341151719/sine-resistor-pcb-analysis/blender/output/c11_35_v8_pcb_isometric.png

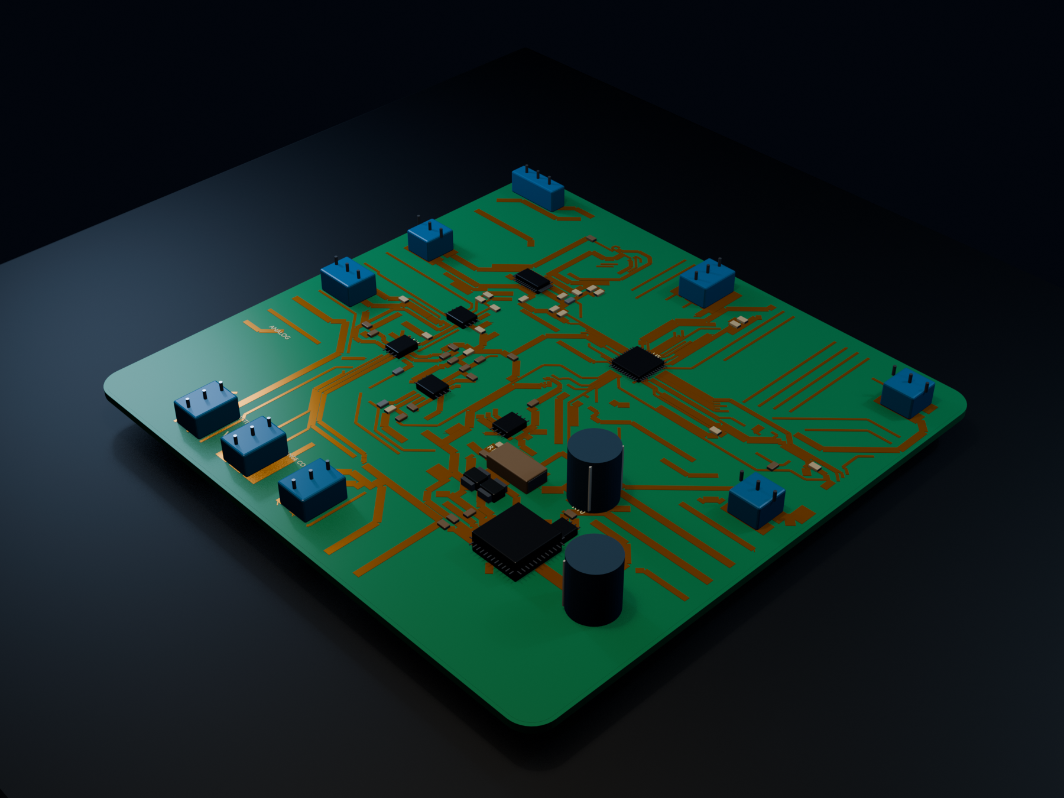
blender/output/c11_35_v8_pcb_isometric.png
