341151719/sine-resistor-pcb-analysis/实际遇到的问题/实板安全排障与根因判定计划.md

# 实板安全排障与根因判定计划

**项目：** Active Acoustic Impedance Controller C11_35  
**日期：** 2026-09-04  
**适用对象：** 已完成SMT的现有板卡  
**目标：** 在不依赖探测IC细脚、不让OPA548长时间进入异常功耗的前提下，用可重复A/B实验确定TP8约100–110 kHz振荡的真实来源，并将它与BOOT/SWD问题、控制算法问题分开。

---

## 1. 当前结论与证据边界

### 1.1 已确认的现象

- TP7/MUL_RAW基本稳定，异常首次明显出现在TP8/VCMD。
- TP8在OPA命令OFF时可出现约100–110 kHz、接近模拟电源轨的大幅周期波形。
- 改变J1的OPA548供电后，TP8波形会发生明显变化。
- OPA ON后J1电源约70 mA进入CC；watchdog关闭OPA后恢复。
- U4 pin6金属脚至U4B_N外部网络约20 mΩ；未上电新板也相同，因此外部pin6兆欧级虚焊模型已经被否定。
- 文档报告OPA OFF时TP9−TP14约0.55–0.65 V；这个值低于OPA548明确Disable阈值0.8 V，但缺少同一振荡时刻的原始波形。

### 1.2 已独立复跑的模型结果

- PCB-aware reduced模型：交越频率1.135410 MHz，相位裕量63.5245°。
- full segmented模型：交越频率1.136326 MHz，相位裕量63.7882°。
- reduced transient尾段TP8仅约1.88×10⁻⁷ Vpp；Gear与Trap算法结论一致。
- 因此，健康OPA1656、1 kΩ/39 kΩ反馈和模型已覆盖的一阶走线/去耦寄生不会自行产生实板的105 kHz振荡。
- 人为加入“U4内部动态异常”能够拟合105 kHz，但它只是等效故障模型，不能代替换件或隔离实验。

### 1.3 当前需要区分的三个故障族

| 故障族 | 能解释什么 | 尚缺的决定性证据 |
|---|---|---|
| U4B本地环路/器件异常 | TP7干净、TP8发振；健康模型与实物不符 | R5断开后仍振；更换U4后消失并可重复 |
| OPA548关断支路经R5参与 | 改变J1会改变TP8；OPA ON后高耗流 | 断开R5后消失；恢复R5后复现 |
| ANA电源或AGND高频异常 | 可从供电/参考端调制U4B | TP11/TP12存在与TP8同步且足够大的纹波；改善供电后可逆消失 |

不得因为“加补偿电容后不振”就直接判定缺少补偿是根因。补偿可能只是在压制任何来源造成的环路异常。

---

## 2. 测试点与可接触位置

### 2.1 连接器引脚——优先用于电源和地

以下映射由当前`project.kicad_pcb`原文件确认。

| 连接器 | Pin 1 | Pin 2 | Pin 3 | 用途 |
|---|---|---|---|---|
| J1 | PWR_P | PGND | PWR_N | OPA548对称电源 |
| J2 | ANA_P_EXT | AGND | ANA_N_EXT | 精密模拟对称电源 |
| J3 | V5_IN | DGND | — | MCU/数字5 V输入 |
| J4 | SPK | PGND | — | 扬声器输出；根因定位期间必须开路 |
| J5 | VK_MCU | VK | VK_EXT | VK来源选择；使用MCU控制时外接1–2桥接 |
| J7 | V3V3 | SWDIO | SWCLK | SWD，另有Pin4=NRST、Pin5=DGND |

接线前必须根据PCB丝印和断电导通再确认Pin 1方向，不能仅凭“左/右”描述接线。

J7没有列入SMT装配，实际焊盘也不适合通电时手压杜邦线。烧录前应一次性焊好匹配排针/短线，或使用带定位的pogo夹具；不得把五根散线临时按在焊盘上完成重复性测试。

### 2.2 现有测试点

| 测试点 | 网络 | PCB坐标(mm) | 用途 | 推荐接法 |
|---|---|---:|---|---|
| TP7 | MUL_RAW | 93.013, 113.362 | U4B输入 | 断电预焊细线；只测量，不外部驱动 |
| TP8 | VCMD | 163.244, 54.307 | U4B输出/OPA548命令 | 断电预焊细同轴中心线 |
| TP9 | OPA_ES | 203.376, 93.677 | OPA548 E/S | DMM测量；需要看交流时预焊线 |
| TP11 | ANA_P | 97.331, 112.346 | U4实际正模拟轨 | 预焊线后示波器测量 |
| TP12 | ANA_N | 93.140, 83.517 | U4实际负模拟轨 | 仅用差分或两通道数学运算测量 |
| TP13 | PWR_P | 203.376, 99.138 | OPA548正轨 | DMM/差分测量 |
| TP14 | PWR_N | 143.305, 86.057 | OPA548负轨 | DMM；绝不能接普通台式示波器地夹 |
| TP16 | AGND | 93.140, 95.455 | 模拟测量参考 | TP7/TP8/TP11/TP12的唯一高频参考 |
| TP17 | PGND | 156.005, 54.307 | 功率测量参考 | TP1/TP2/TP9/TP13/TP14参考 |
| TP1 | SPK | 203.376, 118.696 | 电流取样后扬声器端 | 后期功率级测试使用 |
| TP2 | DRV | 203.376, 88.216 | OPA548功率输出 | 仅在TP8已稳定后使用 |
| TP15 | V3V3 | 187.755, 123.776 | MCU 3.3 V | 数字电源确认 |

**机械限制：** PCB原文件中这些测试点大多实际为约1×1 mm顶层SMD裸焊盘，不是通孔测试柱，而且参考标号在PCB中被隐藏，成品丝印上可能找不到TP编号。上表坐标以PCB左上外形约`(89.965, 51.640)`为参考，可在KiCad中定位。禁止通电时用手持表笔长时间压住。推荐在断电状态焊接30 AWG软线或短细同轴，长度尽量小于50 mm，并用胶带/热熔胶在离焊点5–10 mm处做应力释放。焊完后用放大镜检查锡桥。

### 2.3 没有独立大测试点的U4B_N

U4B_N没有独立编号测试点。若必须同步测反馈比例，不探U4 pin6，优先使用DNP补偿位C14的焊盘；C14 pad 1为VCMD，pad 2为U4B_N。C37/C38/C39/C40/C41也跨接相同两网，可作为备选：

1. 全部电源关闭并确认TP11、TP12、TP13、TP14相对各自地小于0.2 V。
2. 用蜂鸣档寻找与TP8导通的一侧，该侧是VCMD。
3. 另一侧是U4B_N；在这一侧预焊30 AWG短线。即使使用C14，也必须用导通关系复核，不凭左右方向猜测。
4. 上电前再次确认该线未与VCMD或相邻焊盘短路。

不要根据电容在板上的“左/右”猜焊盘编号；以断电导通测试为准。

---

## 3. 仪器与通用安全限制

### 3.1 最低设备

- 三组受控电源：5 V数字电源、±10 V模拟电源、OPA548对称电源。对称电源优先使用跟踪双路或明确隔离的两个通道。
- 两通道或四通道示波器，10×探头；优先使用短地弹簧、细同轴或差分探头。
- 浮地电池式DMM。
- 细线、放大镜、ESD工作台；进行R5/U4操作时需要合格返修工具。

### 3.2 台式示波器接地规则

- 普通台式示波器所有BNC外壳通常与保护地相连，各通道地夹彼此相通。
- 模拟信号TP7/TP8统一以TP16/AGND为参考。
- 功率输出TP1/TP2统一以TP17/PGND为参考。
- 禁止把示波器地夹接到TP12/ANA_N、TP14/PWR_N、TP8或任何信号点。
- 测`TP9−TP14`时优先用浮地DMM；若要观察高频分量，使用差分探头，或两通道分别对TP17测量后用`CH1−CH2`。两个通道的地都只能接TP17。
- 已发生过地夹误接TP2/TP8的事故。每次上电前由第二人或按检查表复核全部地线。

### 3.3 电源连接原则

- 若使用两个电源通道串联生成±电源，先断电用欧姆档确认通道输出之间允许浮地；不允许把两个共地通道强行串联。
- J1中心点只接PGND，J2中心点只接AGND，J3负端只接DGND。板上已有R3连接地域，不再用额外粗线任意短接不同地。
- 先设置电压和限流，再连接板卡；所有改焊均在电源线物理拔除后进行。
- 初次上电不要接扬声器、电子负载或函数发生器。

### 3.4 保守限流与停止条件

下表是排障用保守值，不是产品额定能力签核。

| 电源 | 初始条件 | 初始限流 | 可放宽上限 | 立即停止条件 |
|---|---:|---:|---:|---|
| J3 | 5.0 V | 50 mA | 确认无短路后100 mA；已知固件确需时最高200 mA | 3.3 V异常、器件发热、持续CC |
| J2 | ±8.0 V跟踪预检，随后±10.0 V | 每轨30 mA | 已建立健康基线后每轨50 mA | 任一轨CC超过0.2 s、两轨相差>15 mA、TP8撞轨 |
| J1，OPA OFF | 从±4.0 V开始 | 每轨20 mA | 扫描时每轨30 mA | 任一轨CC、比基线增加>10 mA、器件升温 |
| J1，OPA ON | 仅后期，±4.0 V | 每轨25 mA | 首次脉冲正常后40 mA；本轮不建议超过60 mA | 高频输出>1 Vpp、CC、异常声响或温升 |

若电源只能显示总电流而不能分别显示正负轨，不能执行“轨电流不平衡”判据，应增加串联电流表或使用独立可读通道。

所有阶段通用停止条件：

- TP8出现超过1 Vpp的持续高频时只允许单次捕获，并在0.2 s内关断；明显贴轨时立即关断；
- 任一电源进入CC超过0.2 s；
- 电流比同配置基线上升10 mA以上且原因不明；
- U1/U4/R12/C4达到50 °C停止观察，60 °C为硬停止；没有测温仪时不得用手触摸判断，采用短脉冲和电流门限；
- 负电源极性错误、示波器地线位置不能确认、探线松动。

正常停机时先关闭J2，避免J2仍经R5驱动已经失去供电的OPA548输入；随后关闭J1，最后关闭J3。紧急情况下用总输出键同时关闭J1/J2；若J1已经CC或功率级异常，则优先立即关闭J1并紧接着关闭J2。等待所有正负轨相对各自地低于0.2 V后才能触碰或焊接。需要加速放电时使用10 kΩ、至少1 W绝缘电阻逐轨放电，禁止用螺丝刀短接。

---

## 4. 统一记录格式

每次实验只改变一个变量。每块板分配固定Board ID，至少记录：

| 字段 | 内容 |
|---|---|
| Board ID/批次 | 板号、生产批次、U4/U1顶标照片编号 |
| 硬件状态 | R5装/拆、R10是否并联、Cfb值、J5连接 |
| 电源 | J1/J2/J3设定、电流限制、实际正负轨电流 |
| 控制状态 | 固件版本、OPTR值、OPA命令OFF/ON、DAC设置 |
| 波形 | TP7、TP8 Vpp/频率/DC；必要时U4B_N、ANA轨纹波 |
| 结果 | 稳定/振荡/CC/停止条件 |
| 原始数据 | 示波器截图与CSV文件名 |

示波器应固定使用同一探头倍率、带宽限制和采样率。观察105 kHz时建议：

- 10×探头；
- 采样率至少10 MS/s；
- 时间基准约2–5 µs/div观察单周期，同时保存100–500 µs窗口观察包络；
- 先不开20 MHz带宽限制保存一次原始波形，再开20 MHz限制比较；
- 每次同时保存TP7和TP8，不能用不同时刻的截图计算比例。

---

## 5. 分阶段测试流程

## 阶段A：断电外观与电阻基线

**目的：** 在上电前排除明显错件、焊桥及测试接线风险。

1. 拔除J1/J2/J3/J4全部线缆；等待各测试轨低于0.2 V。
2. 确认J4开路，C14、C37–C41及其他标记DNP的补偿位没有意外装件或锡桥。
3. 拍摄U4、U1顶标和方向照片，记录Board ID。不要只检查振荡板，至少包含一块未修改板。
4. 测U4 pin6外部网络连续性时继续采用已经建立的方法，但不要把20 mΩ解释成芯片内部一定健康。
5. 在电路板内测量R15、R16仅作为筛查：目标约1 kΩ和39 kΩ。若偏差超过标称5%，先考虑并联通路影响；只有抬起一端后的测量才能用于确认错值。
6. 检查J1/J2各轨对中心地是否存在硬短路。电容充电造成的读数变化属于正常可能性，不规定一个绝对电阻门限；使用同批未改板横向比较。

**判定：**

- 多块板同一位置、同一顶标、同一症状：系统性设计/物料问题权重上升。
- 只有个别板异常且外观/阻值不同：装配或器件个体问题权重上升。

## 阶段B：数字与烧录问题独立验证

**目的：** 不给模拟/功率域供电，判断“普通上机和烧录不稳定”是否与模拟振荡是两个问题。

连接：

- J1、J2、J4全部断开。
- J3接5.0 V，初始限流50 mA；确认无短路但正常启动确实需要时再升到100 mA。
- SWD只接J7：Pin1 V3V3检测、Pin2 SWDIO、Pin3 SWCLK、Pin4 NRST、Pin5 DGND。
- 调试器不得同时向目标板供电；只检测V3V3。

流程：

1. 上电后从TP15确认V3V3稳定；若50 mA限流导致正常启动失败，先断电检查无短路，再提高到100 mA。
2. SWD先固定1 MHz并使用connect-under-reset。
3. 读取并记录OPTR；已验证的Flash启动值为`0xFBEFF8AA`，历史异常值为`0xFFEFF8AA`。复位后PC应进入`0x0800....`主Flash范围，而不是`0x1FFF....`系统存储器。
4. 连续执行10次“断电5 s→上电→连接→擦除→写入→verify→复位运行”。
5. 每次记录成功/失败、错误原文、V3V3和NRST状态。
6. 只有1 MHz十次全通过后，才可另做4 MHz对照；4 MHz失败而1 MHz稳定只证明接口裕量问题，不证明MCU损坏。

**判定：**

- J1/J2完全断开仍烧录失败：模拟振荡不是烧录失败的必要条件，继续沿BOOT、SWD接触、NRST及3.3 V调查。
- 数字单独10/10通过，而接入模拟电源后失败：再建立模拟电源接入的单变量A/B。

## 阶段C：原板零输入振荡基线

**目的：** 在OPA始终OFF、J4开路条件下重现实板异常，建立后续A/B基线。

准备：

- 在断电状态预焊TP7、TP8、TP16短线；TP7/TP8只接10×示波器输入。
- J5必须保持“原始故障复现时”的准确状态并记录。若原测试为OPEN，本轮先保持OPEN；只有另立单变量实验时才桥接1–2或2–3，不能在建立基线时顺便改变J5。
- 固件将OPA命令保持OFF，DAC/算法保持静态零测试状态。
- 不接外部函数发生器；TP7是AD633输出，直接驱动会造成输出争用。

上电顺序：

1. J3 5 V上电，确认固件运行且OPA命令OFF。
2. J1设±4.0 V、每轨20 mA，同时使能正负轨。先给处于Disable命令的OPA548供电，再启动J2，是为了避免TP8经R5驱动一个完全无电的OPA548输入。
3. J2先设±8.0 V、每轨30 mA完成极性和电流预检；AD633保证工作范围从±8 V开始，低于此值的波形不能用于根因判定。预检正常后升至原故障条件±10.0 V，每轨35 mA。
4. 立即记录三组电流和TP7/TP8；若触发停止条件，优先总键同时关闭J1/J2；不能同时关闭时按3.4节的紧急停机规则执行，最后关闭J3。
5. 在±4.0、±4.5、±5.0、±5.5、±6.0、±6.5 V逐级改变J1，J2保持±10 V不变。波形稳定且小于1 Vpp时每档最多停留3 s；一旦触发到>1 Vpp持续高频，只做预设单次捕获，并在0.2 s内关闭J1/J2，不继续扫更高电压。优先使用电源总输出键同时关闭；不能同时关闭时先关J2，若J1已CC则先关J1并立即关J2。
6. 每档保存TP7/TP8同步波形、TP8频率/Vpp/DC和J1正负轨电流。若在某档进入CC，不继续提高。

**这个阶段不允许OPA ON。**

**判定：**

- TP7稳定而TP8出现105 kHz：确认问题仍定位在TP7之后。
- J1电压可重复改变TP8波形：证明J1域参与或调制，但不能单凭此点认定OPA548是振荡源。
- 不同板的转变电压高度一致：系统性设计/器件特性权重上升；离散很大则装配、器件批次或接触问题权重上升。

## 阶段D：使用现成TP确认OPA548实际关断状态

**目的：** 不探U1细脚，确认振荡时E/S相对PWR_N是否仍处于Disable区。

连接：

- 浮地DMM直接接TP9与TP14，红表笔TP9、黑表笔TP14。
- 示波器仍只观察TP7/TP8；不把示波器地接TP14。
- DMM只能提供慢速/直流筛查；它不能证明E/S在105 kHz每个周期都未跨越门限。

流程：

1. 重复阶段C中最容易产生规则105 kHz的一档J1电压。
2. 用DMM读取`V(TP9)−V(TP14)`的慢速值；若要记录最小/最大和门限跨越，必须用有足够带宽的差分波形。
3. 在J1各电压档重复；不要只测一个静态电压。
4. 若需要观察E/S交流分量，使用差分探头；没有差分探头则两通道均对TP17测量后相减。

**波形判据：**

- 全过程≤0.8 V：数据手册意义上明确Disable；“R10导致实际一直Enable”不成立。
- 全过程≥2.4 V：实际Enable，过去的“OPA OFF”定义错误。
- 进入0.8–2.4 V或随105 kHz跨越门限：E/S处于未保证区，优先调查R10/U7动态。
- 即使≤0.8 V，也只能证明关断逻辑电平正确，不能证明关断器件在105 kHz下完全没有输入/保护耦合。

仅有DMM时，≤0.8 V或≥2.4 V只能作为平均/慢速状态证据，不得写成“全过程”判定。

## 阶段E：R5隔离——最高信息量实验

**目的：** 直接判断OPA548输入支路是不是TP8振荡成立的必要条件。

返修：

1. 全部电源线拔除，确认TP11/TP12/TP13/TP14相对地均低于0.2 V。
2. 完整拆下R5=100 Ω，不切PCB走线；保存原件或准备同规格新件。
3. 放大检查焊盘。用蜂鸣档确认其中一侧与TP8导通，该侧为VCMD；两焊盘之间应开路。
4. 不在通电状态触碰R5焊盘，也不需要探测OPA_IN_P或U1细脚。

测试E1——J1不供电：

1. J4开路、OPA命令OFF。
2. 先J3上电，再给J2±10 V、每轨35 mA上电；J1保持物理断开。此处R5已经拆除，因此不会经TP8反向驱动无电的OPA548输入。
3. 观察TP7/TP8 10 s。

测试E2——J1供电但OPA OFF：

1. 保持R5拆除。
2. J1从±4.0 V开始，按阶段C的档位扫到异常发生前的最高安全档。
3. 同步记录TP7/TP8和电流。

恢复验证：

1. 全部断电并放电后重新焊接100 Ω R5。
2. 重复阶段C完全相同的电压档和固件状态。

**决定性判因：**

| R5拆除 | R5恢复 | 结论 |
|---|---|---|
| 仍以相同频率/幅度振荡 | 仍振荡 | OPA548输入支路不是必要条件；转向U4本地/ANA供电 |
| 稳定 | 恢复后重新振荡 | OPA548/R5支路是必要条件，形成强因果证据 |
| 稳定 | 恢复后仍稳定 | 不能判因；返修加热或接触变化可能影响了U4/R5周围状态 |
| 频率/幅度改变但未消失 | 恢复后可逆 | OPA548支路是参与者，但可能不是唯一振荡源 |

至少在两块板重复，不能用单板单次结果结束调查。

## 阶段F：若R5拆除后仍振荡——调查U4本地环路

### F1. 同步反馈比例

1. 按2.3节优先在DNP C14的U4B_N侧预焊短线，不探U4 pin6；C37–C41仅作为备选。
2. CH1接TP8，CH2接预焊的U4B_N线；两个通道地都接TP16。
3. 同步读取Vpp和相位，计算`U4B_N Vpp / TP8 Vpp`。

判据：在Cfb确认DNP、正弦基波、共同AGND参考且输入电流可忽略时，健康1 kΩ/39 kΩ反馈的基波比例应接近1/40=0.025。对方波或装有Cfb时应比较105 kHz基波复数幅值和相位，不直接比总Vpp。若在上述条件下稳定得到0.045–0.055：

- 先断电确认R15/R16实物值；
- 检查AGND高频运动；
- 在排除前两项后，才把U4输入异常提高优先级。

### F2. ANA电源轨同步测量

- CH1：TP8对TP16。
- CH2：TP11对TP16，记录ANA_P纹波。
- 测ANA_N时使用差分探头，或两个通道分别测TP12和TP16后相减；禁止地夹接TP12。
- 分别保存100–110 kHz处的幅度与相位。

判据：

- 轨纹波仅几十mV，而TP8接近十几Vpp：不支持“外部电源纹波直接驱动TP8”。已有模型估计需要数V峰值的轨纹波才能直接产生16 Vpp TP8。
- 轨纹波达到0.5 Vpp以上：供电完整性成为高优先级。
- 达到1 Vpp或电源进入CC：立即停机，不继续扫电压。

### F3. Cfb诊断，不作为最终修复结论

1. 全部断电并放电。
2. 优先在C39=22 pF位置安装22 pF C0G/NP0；保持R5拆除状态，重复阶段E1/E2。
3. 记录是否消振、频率、TP8噪声和低频增益。
4. 移除22 pF确认是否恢复；必要时再在C40位置试47 pF。
5. 本阶段不直接安装220 pF作为最终值。

若22/47 pF使振荡消失，只能证明降低高频环路增益有效。只有结合R5隔离、供电测量和U4换件结果才能判断根因。

### F4. U4可逆换件

这是返修级操作，不要求操作者探测SOIC细脚。

1. 选择一块症状可稳定复现的板，保持Cfb=DNP并记录完整基线。
2. 由具备SOIC返修能力的人员更换为来源可追溯的OPA1656IDR。
3. 清洗并检查焊点，不顺便改动R5/R15/R16或去耦。
4. 重复阶段C和阶段E1条件。
5. 如果新U4不振，条件允许时把旧U4装到测试载板或原板复测；否则“换件后好了”仍混入了重焊效应。

强确认条件：同一板、同一条件下旧U4振荡，新U4稳定，而且第二块板重复相同结果。

## 阶段G：若R5拆除后稳定——调查OPA548关断支路

先恢复R5=100 Ω并确认异常可复现，再做以下单变量测试。

### G1. R10加强下拉A/B

1. 断电并放电。
2. 将10 kΩ电阻临时接在TP9与TP14之间，等效与R10=100 kΩ并联。优先焊接带绝缘的短引线，不在通电时夹持。
3. 保持OPA命令OFF，禁止执行OPA ON。
4. 重复阶段C的J1扫描，记录TP9−TP14、TP7/TP8和J1电流。
5. 断电移除10 kΩ后恢复原条件，确认现象是否返回。

判定：

- 并10 kΩ稳定、移除后恢复振荡：E/S偏置或动态是必要因素。
- TP9−TP14始终约0.6 V且并10 kΩ无影响：R10不是当前主因。
- 只改变波形但不消失：E/S参与，但仍有其他发生源。

### G2. J1参与性

保持R5装回、OPA OFF，比较：

- J1±4.0 V；
- J1±5.0 V；
- J1±6.0 V；

不建议把“J1完全断电”与“J1供电关断”直接等价，因为无电的OPA548输入保护结构可能以不同方式加载TP8。只有R5物理拆除才是真正的支路隔离。

### G3. OPA548换件

只有R5隔离已经证明该支路必要、而R10 A/B不能解释时，才安排OPA548返修换件。换件前后保持R5、J1、J2和固件完全一致，并在至少两块板验证。

---

## 6. 功率级重新启用的安全门槛

在满足以下全部条件以前，不允许OPA ON：

- 根因定位阶段J4保持开路；首次OPA ON前改接1 kΩ假负载；
- TP8在10 s观察内没有持续100–110 kHz分量；
- TP8高频Vpp小于50 mV；
- TP7/TP8直流工作点没有贴轨；
- J1/J2没有CC或明显正负轨不平衡；
- R5、Cfb及所有临时线状态已经记录。

### 6.1 首次OPA ON验证

1. 在J4接入1 kΩ、至少2 W的纯电阻假负载；不要直接接扬声器。J1只设±4.0 V，每轨限流25 mA；J2保持±10 V。
2. 示波器CH1接TP8/TP16，CH2接TP2/TP17。
3. 固件输出静态零命令，OPA ON脉冲先限制为20–50 ms；不要依赖5 s watchdog保护。
4. 任一条件出现立即OFF：TP2高频>1 Vpp、TP8高频>50 mVpp、J1触及25 mA限流或温度达到50 °C。
5. 20–50 ms连续三次正常后，可把限流提高到40 mA，再延长至100 ms、500 ms、1 s；每一级都保存波形和电流。

### 6.2 小信号功能测试

- 不从外部函数发生器直接驱动TP7/TP8。
- 使用固件/DAC产生低频命令，并以实测TP7作为真实输入量。
- 从100 Hz开始，令TP7≤10 mVpp；按非反相增益约40估算，TP8约0.4 Vpp。
- 依次测试10、30、100、300、1000 Hz；每次先确认无100–110 kHz寄生，再提高TP7至25 mVpp。
- 在1 kΩ初始假负载下输出稳定前，不提高到会让TP8超过2 Vpp的输入。

### 6.3 负载测试

实际扬声器最后连接。推荐顺序：

1. OPA OFF、J4开路的前级稳定性；
2. OPA ON、1 kΩ纯电阻初始假负载；
3. 合适功率等级的20 Ω纯电阻假负载；
4. 7.2 Ω纯电阻假负载；
5. 实际扬声器。

每换一种负载都从J1±4 V、小信号和低限流重新开始。负载电阻额定功率必须按测试信号计算并留至少2倍裕量；不能使用普通小功率电阻代替。

---

## 7. 根因判定矩阵

| 实验结果 | 支持的根因 | 被削弱的根因 | 下一步 |
|---|---|---|---|
| 数字域单独仍烧录失败 | BOOT/SWD/NRST/3.3 V独立问题 | 模拟振荡是唯一总根因 | 完成10次1 MHz/4 MHz受控A/B |
| R5拆除后105 kHz完全不变 | U4本地、反馈或ANA供电 | OPA548输入支路是必要条件 | F1/F2/U4换件 |
| R5拆除后稳定，恢复后复现 | OPA548/R5支路是维持该现象的必要条件 | 只由与R5无关的机制维持 | G1，再区分输入钳位、E/S、供电耦合和器件故障 |
| R10并10 kΩ后可逆消振 | E/S偏置/动态是维持现象的必要条件之一 | 与E/S状态无关的机制 | 验证ON/OFF裕量、温度/批次和R5两端电流 |
| U4换件后可逆消振 | U4错料/损伤/批次动态异常 | 单纯PCB寄生 | 查顶标、来源、批次和受损机制 |
| 22/47 pF消振但R5/U4 A/B无结论 | 仅证明补偿能压症状 | 无法确定发生源 | 不冻结量产值，继续隔离实验 |
| ANA轨存在同频>0.5 Vpp纹波 | 供电/地耦合参与 | 纯净供电假设 | 查FB1/FB2、去耦回路和电源源阻抗 |
| Cfb=DNP且基波TP8/U4B_N稳定接近1/20 | 实物反馈比、地参考或U4输入异常 | 健康1k/39k假设 | 断电隔离测R15/R16并查AGND；保留同步波形 |
| 多块未修改板完全相同 | 系统性设计/物料/布局 | 随机单板损伤 | 选一个变量跨板A/B |
| 只有受过误接地的板异常 | 个体器件损伤 | 系统性必现问题 | 与全新板同条件比较并换U4 |

根因达到“确认”至少需要：

1. 单变量改变使问题消失；
2. 恢复原变量使问题重新出现，或在第二块板重复；
3. 观察到的后果与电路机制相符；
4. 没有触发供电CC、测量接地或返修加热等混杂变量。

只满足其中一项时最多标记为“相关”或“候选”，不得写成最终根因。

---

## 8. 推荐实际执行批次

### 第一批：无需改焊器件

1. 阶段A外观和阻值筛查。
2. 阶段B数字域10次烧录基线。
3. 预焊TP7/TP8/TP16测量线。
4. 阶段C受控J1扫描。
5. 使用TP9/TP14完成阶段D。

### 第二批：只改R5，信息增益最高

1. 选择症状最稳定的一块板拆R5。
2. 完成E1、E2。
3. 恢复R5重复原条件。
4. 在第二块板重复。

### 第三批：根据R5结果二选一

- R5拆除后仍振：做F1、F2，然后U4换件；Cfb仅作为诊断。
- R5拆除后稳定：做R10并10 kΩ可逆A/B，再决定是否换OPA548。

### 第四批：功率级恢复

只有TP8稳定后才执行阶段6，先在1 kΩ假负载下做毫秒级OPA ON，再做小信号，然后才换20 Ω/7.2 Ω假负载，最后接扬声器。

---

## 9. 禁止事项

- 禁止通电时用普通表笔直接探U4/U1细脚。
- 禁止示波器地夹接负电源轨、TP8、TP2或任意非地信号。
- 禁止在TP7、TP8直接接函数发生器。
- 禁止在100–110 kHz仍存在时执行长达5 s的OPA ON。
- 禁止一边改变J1电压、一边改变限流、固件、Cfb或负载后再把结果当成单变量实验。
- 禁止因为22/47/220 pF使波形变小就宣布“根因是缺电容”。
- 禁止把ngspice的`timestep too small`当成实板振荡证据。
- 禁止使用已经发生示波器误接地的板作为唯一代表板。

---

## 10. 验证基础与局限

### 已执行

- KiCad原理图与PCB网络核对。
- 生产BOM、CPL和Gerber一致性核对。
- PCB-aware reduced/full AC复跑。
- reduced transient使用Gear/Trap两种方法复跑。
- 实际问题对话记录按“实测/仿真/推测/计划”重新分类。

### 本计划的限制

- 当前目录没有可复核的原始示波器CSV、完整截图、板号和逐板重复次数。
- OPA548厂商宏模型的OFF transient不可靠，不能用于关断状态定量签核。
- R15/R16约1/40矛盾缺少同步双通道原始测量。
- R5隔离、R10并联、U4换件和ANA轨同步波形尚未在实板执行。
- 本计划中的限流是排障保护设置，不是产品最大额定电流或最终性能指标。

因此，文档当前给出的是可执行的安全判因流程，而不是预先指定某一个元件为最终根因。

---

## 11. 主要证据来源

- **PCB原文件确认：** `KICAD部分/给厂商的板子加工数据/正弦电阻V7_KiCad10.0.4_校正转换版/project.kicad_pcb`。用于确认J1/J2/J3/J4/J5/J7引脚、TP网络、焊盘尺寸和R5/R10/R15/R16网络。
- **生产BOM确认：** `KICAD部分/给厂商的板子加工数据/正弦电阻V7_KiCad10.0.4_校正转换版/audit/bom_smt_73.csv`。用于确认U1、U4及关键电阻的实际下单值。
- **实板现象来源：** `实际遇到的问题/分支-·-分支-·-SPICE可行性测试结果.md`。其中同时包含用户实测、历史助手推测和仿真结果；本计划没有把三者混为一类。
- **独立复跑网表：** `实际遇到的问题/PCB_AWARE_U4B_OFF_reduced.cir`与`PCB_AWARE_full_extracted_loop.cir`。
- **OPA548数据手册依据：** 推荐双电源范围±4 V至±30 V；Disable为`E/S≤V−+0.8 V`，Enable为`E/S≥V−+2.4 V`；关断静态电流典型约±6 mA，正常静态电流典型约±17 mA；关断器件遇到高于20 kHz信号时泄漏可能增加。
- **AD633数据手册依据：** 工作电源范围±8 V至±18 V。因此低于±8 V只适合短路/极性预检查，不能用于判断正常模拟行为。

证据等级用法：原文件网络和独立仿真数值可以复核；数据手册阈值用于设置边界；“U4内部异常”“OPA548关断耦合”等在完成可逆实板A/B以前仍属于候选解释。
