341151719/sine-resistor-pcb-analysis/实际遇到的问题/分支-·-分支-·-SPICE可行性测试结果.md

> From: https://chatgpt.com/g/g-p-6a4f06948d488191a8b99392c0b437f0/c/6a8c0352-682c-83ec-a9a8-80c052f3bece

> 历史对话归档：包含后续被否定或限定的判断，不宜直接作为当前结论。
> 2026-09-15 复核见 [证据重新审查](../实验还原部分/主动审计/EVIDENCE_REASSESSMENT_20260915.md)：
> 峰值电流不能证明持续 CC；1/40 反馈比例只适用于规定的无补偿/近似高输入阻抗条件；
> 命令 OFF 与硬件 OFF、J1 参与性与振荡起源必须分开确认。

# you asked

message time: 2026-07-09 10:34:38

测试SPICE的可行性。

---

# chatgpt response

我会直接在沙盒里解压运行时和 Python wheel 包，离线安装 PySpice/spicelib，然后跑命令行 ngspice、raw 解析和 PySpice shared-library 三类最小测试。上传说明里提到的 runtime 文件名带“(1)”，但实际挂载路径是不带“(1)”的，我会按实际路径处理。

离线安装已完成。pip 报的是与系统现有包的版本冲突提示，但安装目标是独立的 `/mnt/data/spice_site`，不影响这次 SPICE 可行性测试。下一步验证 ngspice 二进制、动态库和最小 RC 仿真。

命令行 RC 瞬态仿真已经通过：ngspice 生成了 181 个数据点；raw 文件也已生成并可由 spicelib 读取。PySpice shared-library 调用也跑通，末点 `v(out)` 与 raw 解析结果一致。

结论：SPICE 在当前沙盒中可行。上传的两个 ZIP 包足以跑通基础 SPICE 工作流：ngspice 命令行、batch transient、raw 输出、spicelib 解析、OP/AC 分析，以及 PySpice 通过 `libngspice.so` 直接调用。上传说明文档中的目标和限制也与本次实测一致：基础仿真可用，OSDI/Verilog-A 需要额外 `.osdi` 模型文件。

实测结果：

| 项目 | 结果 |
|---|---|
| Python | 3.13.5 |
| ngspice | 42，可执行 |
| 动态库依赖 | `ngspice` 和 `libngspice.so.0` 均无 `not found` |
| PySpice | 1.5，可导入 |
| spicelib | 可导入 |
| ngspice 命令行 transient | 通过，181 个数据点 |
| raw 文件生成 | 通过 |
| spicelib 读取 raw | 通过，traces 为 `time`, `v(in)`, `v(out)`, `i(vin)` |
| OP/AC batch 分析 | 通过 |
| PySpice shared-library transient | 通过，181 个数据点 |

关键输出：

```text
last time: 9.999999999999999e-06
last v(out): 0.004976582241281845
ALL SPICE FEASIBILITY TESTS PASSED
```

我做了两个必要修正：

1. 实际上传路径是 `/mnt/data/ngspice_runtime_linux_x86_64.zip`，不是说明里的带 `(1)` 文件名。
2. `setup_spice_env.sh` 已改成兼容未定义环境变量的写法，例如 `${LD_LIBRARY_PATH:-}`，避免 `set -u` 下报错。

PySpice 测试中出现了两个非致命提示：

```text
Node name 'in' is a Python keyword
Unsupported Ngspice version 42
Using SPARSE 1.3 as Direct Linear Solver
```

这些没有阻止仿真完成。`Using SPARSE...` 已通过 PySpice stderr 判定补丁处理。

生成的文件：

[查看完整测试报告](sandbox:/mnt/data/spice_feasibility_report.txt)  
[下载/复用一键测试脚本](sandbox:/mnt/data/spice_feasibility_test.sh)  
[环境变量脚本](sandbox:/mnt/data/setup_spice_env.sh)

---

# you asked

message time: 2026-08-23 17:34:12

分析这个SPICE的准确性，计算成本高你就分多次计算，拆开算，比如频率拆开，时间拆开或者局部网格拆开。以后也是这样。

Rated power	30 W

Nominal impedance Z	8 Ohm

Frequency response	80–20000 Hz

Mean sound pressure level	86 dB (1 W/1 m)

Opening angle (-6 dB)	113°/4000 Hz

Excursion limit	+/−4 mm

Resonance frequency fs	90 Hz

Magnetic induction	0.95 T

Magnetic flux	180 µWb

Height of front pole-plate	3 mm

Voice coil diameter	20 mm

Height of winding	6 mm

Cutout diameter	100 mm

Net weight	0.38 kg

D.C. resistance Rdc	7.2 Ohm

Mechanical Q factor Qms	2.29

Electrical Q factor Qes	0.95

Total Q factor Qts	0.67

Equivalent volume Vas	2.3 l

Effective piston area Sd	50 cm²

Dynamically moved mass Mms	5.7 g

Force factor Bxl	4.6 T m

Inductance of the voice coil L	0.2 mH

如果我希望在一个被动电声膜，注意是被动性的情况下，使用负阻抗变换器的方式，将其的电阻变小。其会被外界的声压激发，我希望其最终的声学段看过去的电学阻抗小了。

重新强调，我希望是外界有一个声源，我们的电声膜是作为被动的反射体，来改变其阻抗

有一个特点是，我希望其电阻变大变小的方式是正弦的形式。

我希望可以以正弦的形式，甚至多个正弦函数或者任意形状电阻叠加的方式，使得其Rdc从7.2Ω到1-100Ω变化，实时变化，变化速度是10-1000hz之间变化。

---

# chatgpt response

我会把项目按“电声模型正确性、负阻抗实现、时变电阻实现、数值稳定性、物理可实现性”五层拆开检查。计算量大的部分会按频段和调制频率分批跑，不会为了省算力把验证范围缩掉。

项目本身已经展开。我先遇到的是运行环境不再保留上一次会话生成的 `/mnt/data/setup_spice_env.sh`；这不影响项目分析，但要重新用已上传的 runtime/wheel 包初始化，之后再跑分段签核。

基础回归已通过：项目结构检查、验收算法单测、7.2 Ω/1 kHz 纯厂商模型 smoke 都没有仿真或验收失败。现在进入真正关键的两组：固定 1/5/7.2/20/100 Ω，以及 10/30/100/300/1000 Hz 时变阻抗。

我已经按你要求把计算拆开跑了：固定阻抗按 1/5/7.2/20/100 Ω 分开，动态按 10/30/100/300/1000 Hz 分开，并另外做了 90 Hz 外部声压驱动的声学侧校验。运行环境按上传的 ngspice/PySpice 说明重新建立。

结论先说：这个 SPICE 目前可以作为“原理成立 + 低频小信号 + 首板调试”的模型，但不能把它当成“1–100 Ω、10–1000 Hz 任意时变阻抗已经准确实现”的签核模型。固定中间阻值已经不错；1 Ω 和 100 Ω 边界存在明显复阻抗误差；完整 1–100 Ω 正弦变化在当前默认补偿下 5 个调制频率全部不通过。更重要的是，现在的 SPICE 还没有真正建立“入射声波→反射声波”的完整声场模型，所以它不能直接证明真实反射系数。

### 1. 你的物理思路本身成立，但有一个非常关键的方向关系

你的膜片可以完全由外界声压激励，不需要 MCU 主动给它生成音频波形。电路只根据线圈电流形成一个合成电阻，因此本质上是一个“受外界声场驱动的主动电声边界”。

但严格说，它不是一个整体无源器件。膜片可以是被动的，声源也是外部的，但负阻抗变换器、OPA548、AD633 等需要供电，因此整个边界条件是 active boundary。

你真正改变的也不是扬声器的物理 `Rdc=7.2 Ω`。铜线的 Rdc 始终还是约 7.2 Ω。你实现的是：

$$
R_\text{total}(t)=R_e+R_x(t)
$$

其中

$$
R_e=7.2\Omega
$$

所以要得到 1–100 Ω 的“等效总电阻”：

$$
R_x=-6.2\Omega \quad\text{到}\quad +92.8\Omega
$$

也就是说：

- 目标 1 Ω：控制器必须产生约 `-6.2 Ω` 的负电阻；
- 目标 7.2 Ω：控制器约等于 0 Ω；
- 目标 100 Ω：控制器产生约 `+92.8 Ω`。

当前 SPICE 的控制数学关系是正确的。0.1 Ω 电流采样经过约 ×50，AD633 × `VK`，再经过 ×20，最终理论上得到：

$$
V_\text{SPK}\approx R_x(t)I_\text{port}
$$

所以架构思想没有根本性数学错误。

但有一个很重要的电声关系：

$$
Z_\mathrm{surf}(\omega)
\approx
\frac{
R_{ms}
+j(\omega M_{ms}-1/\omega C_{ms})
+\frac{(Bl)^2}{R_\text{target}+j\omega L_e}
}{S_d}
$$

这里是声压/膜速度形式的表面声阻抗。

注意里面是：

$$
\frac{(Bl)^2}{R_\text{target}}
$$

所以在低频近似下，**电阻越小，电磁阻尼反而越大，声学端看到的机械/声学阻力越大。**

这和“把电学电阻变小，所以声学阻抗也变小”并不是同一方向。

按你的参数，在 90 Hz 左右，仅使用这个简化活塞模型：

| 等效电阻 | 90 Hz 表面声阻抗约值 |
|---:|---:|
| 1 Ω | `4460 - j473 Pa·s/m` |
| 5 Ω | `1127 - j19 Pa·s/m` |
| 7.2 Ω | `869 - j9 Pa·s/m` |
| 20 Ω | `493 - j1 Pa·s/m` |
| 100 Ω | `324 - j0.05 Pa·s/m` |

空气特性阻抗大约是 413 Pa·s/m。

所以在这个极简模型中，90 Hz 附近大约 `20–35 Ω` 反而更接近空气阻抗匹配。1 Ω 会使膜片呈现很强的电磁制动，更接近高阻抗边界。

这一点对你最后想控制“反射/吸收”非常重要。

---

### 2. 固定电阻：当前 SPICE 的实际结果

我重新跑了纯厂商宏模型路径的固定阻抗签核，载波为 1 kHz：

| 目标 | SPICE 实测复阻抗 | 结果 |
|---:|---:|---|
| 1 Ω | `1.054 + j0.342 Ω` | 不通过 |
| 5 Ω | `5.046 + j0.122 Ω` | 通过 |
| 7.2 Ω | `7.249 - j0.0079 Ω` | 通过 |
| 20 Ω | `20.001 - j0.767 Ω` | 通过 |
| 100 Ω | `98.816 - j5.605 Ω` | 不通过 |

这里非常重要：1 Ω 的“实部”其实已经相当接近目标，只有约 +0.054 Ω；真正导致它失败的是 `+j0.342 Ω`。

100 Ω 同样不是实部特别糟，实部约 98.8 Ω；主要问题是出现 `-j5.61 Ω`。

也就是说，现在最主要的问题不是“完全做不出负电阻”，而是：

> 合成出来的东西没有保持纯电阻，而逐渐变成了带明显相位的复阻抗。

这和项目报告里判断的 INA149 → OPA1656 → AD633 → OPA1656 → OPA548 整条前馈链的带宽/相位问题一致。

[固定阻抗完整结果 CSV](sandbox:/mnt/data/spice_proj_analysis/SPICE_project_repaired_20260710_FINAL/1SPICE_SPICE_SIM/results_fixed_signoff_combined/all_summary.csv)

---

### 3. 10–1000 Hz 正弦变化：当前版本明确没有通过

你要求：

$$
R(t)=R_0+A\sin(2\pi f_m t)
$$

并且要求 `1–100 Ω`、`fm=10–1000 Hz`。

我把 5 个调制频率分开跑完了。项目当前动态签核使用 10 kHz 电流载波：

| R 调制频率 | p95 实部相对误差 | p95 虚部相对值 | 结果 |
|---:|---:|---:|---|
| 10 Hz | 48.3% | 103% | 失败 |
| 30 Hz | 56.5% | 120% | 失败 |
| 100 Hz | 69.8% | 175% | 失败 |
| 300 Hz | 88.3% | 108% | 失败 |
| 1000 Hz | 115% | 288% | 失败 |

5/5 都是 ngspice 正常完成以后，被工程验收判定失败，并不是求解不收敛。

[动态阻抗完整结果 CSV](sandbox:/mnt/data/spice_proj_analysis/SPICE_project_repaired_20260710_FINAL/1SPICE_SPICE_SIM/results_dynamic_signoff_combined/all_summary.csv)

这里我又进一步检查了一个问题：为什么连 10 Hz 这么慢的调制都这么差？

原因之一已经明确找到了：动态签核使用的是 10 kHz 载波，而当前电路在 10 kHz 本身就不具备足够好的纯电阻合成能力。

我单独跑固定 10 kHz：

- 目标 1 Ω → `2.436 + j3.110 Ω`
- 目标 7.2 Ω → `7.237 + j0.0048 Ω`
- 目标 100 Ω → `76.98 - j46.82 Ω`

这解释了动态结果里一个很明显的现象：

> 10 Hz 调制失败，不代表电路连“每秒变化 10 次”都跟不上；相当一部分误差其实来自 10 kHz 音频/电气载波上的基础相位误差。

所以以后不能只用一个 10 kHz carrier 来评价“10–1000 Hz 电阻变化速度”。

必须变成二维问题：

$$
f_\mathrm{acoustic}\times f_\mathrm{modulation}
$$

也就是“外界声音频率”和“你改变阻抗的速度”必须分开。

---

### 4. 外界声压驱动这一点，我也单独验证了

因为你强调了“不是主动扬声，而是外界声源激励膜片”，所以我没有只看电流注入测试。

我另外跑了：

- 外部声压：1 Pa；
- 声音频率：90 Hz；
- 不加主动音频电流源；
- 固定 Rtarget；
- 分别测 1 Ω、7.2 Ω、100 Ω。

得到声压/膜速度等效表面阻抗：

| Rtarget | SPICE | 同一 T/S 模型解析结果 | 幅值差 |
|---:|---:|---:|---:|
| 1 Ω | `4259 - j445` | `4460 - j473` Pa·s/m | -4.5% |
| 7.2 Ω | `865 - j1.95` | `869 - j9.23` | -0.46% |
| 100 Ω | `324.7 + j0.21` | `323.8 - j0.05` | +0.26% |

[90 Hz 声学侧校验结果](sandbox:/mnt/data/acoustic_probe_90Hz_summary.csv)

这说明一个好消息：

> 当前 SPICE 中“线圈电流 ↔ Bl ↔ 膜速度 ↔ 外界压力”的基本电机耦合写法是正确的。

特别在 7.2 Ω 和 100 Ω，SPICE 与同一组 T/S 参数的解析模型基本重合。

1 Ω 的差异增加到约 4.5%，也符合预期，因为这是负阻抗补偿最激进、控制链误差最容易放大的区域。

但这里一定要区分：

这是“SPICE 与它自己的数学扬声器模型一致”。

它并不能证明实际扬声器也能达到 0.5% 或 4.5% 的准确性。

---

### 5. 目前扬声器模型本身有一个明显的参数一致性问题

当前 netlist 实际使用的是：

`Re, Le, Bl, Mms, fs, Qms, Sd, Xmax`

它由：

$$
C_{ms}=\frac1{M_{ms}(2\pi f_s)^2}
$$

以及

$$
R_{ms}=\frac{2\pi f_sM_{ms}}{Q_{ms}}
$$

计算机械参数。

所以你给的 `Qes=0.95、Qts=0.67、Vas=2.3 L` 实际并没有作为独立约束进入 SPICE。

这造成了数据内部的不一致。

按照现在 SPICE 真正使用的：

- Re = 7.2 Ω
- Bl = 4.6 Tm
- Mms = 5.7 g
- fs = 90 Hz

算出来：

$$
Q_{es}\approx1.097
$$

而资料给的是：

$$
Q_{es}=0.95
$$

偏差约 +15.4%。

进一步得到：

$$
Q_{ts,\ model}\approx0.742
$$

资料是：

$$
Q_{ts}=0.67
$$

差约 +10.7%。

另外由 `Mms/fs/Sd` 得到的 Cms，再换算 Vas，大约只有：

$$
V_{as}\approx1.94L
$$

而你给的是：

$$
2.3L
$$

差约 -15.5%。

反过来如果强制相信 Vas=2.3 L，则对应的谐振频率约是：

$$
82.7Hz
$$

而不是 90 Hz。

所以，目前真正的扬声器模型精度，我认为只能定位成：

> 低频 T/S 一阶近似模型，但它对应的等效扬声器参数并没有完全复现你提供的厂家 T/S 数据。

这是当前“声学准确性”最大的误差源之一。

---

### 6. 还有几个比 SPICE 数值误差更重要的现实模型缺口

第一，当前没有真正的声辐射阻抗。

`BPRESS` 只是直接向膜片施加：

$$
F=P S_d
$$

它没有建立“入射波 + 膜片辐射波 + 反射波”的耦合声场。

因此目前不能直接从这个 SPICE 得到可信的：

- 反射系数；
- 吸声系数；
- 法向声阻抗；
- 前后声场；
- 有限尺寸挡板效应。

这也是为什么我上面算的约 20–35 Ω 接近匹配只能作为理论方向，不能当成最终反射率。

第二，厂家给的这些参数目前完全没有进入模型：

- 86 dB 1W/1m；
- 80–20000 Hz frequency response；
- 113° / 4 kHz opening angle；
- 30 W rated power；
- 0.95 T 磁感应；
- 180 µWb 磁通；
- 极板几何参数。

所以目前的 SPICE 绝对不能声称能够准确模拟 80 Hz–20 kHz 的实际声学行为，尤其 1 kHz 以上。

第三，没有 diaphragm breakup、辐射质量、频率相关机械损耗、Le 的频率依赖和涡流效应。

尤其到 5–20 kHz，单纯 `Le=0.2mH` 加一个理想刚性活塞已经不足以代表真实单元。

第四，没有：

$$
Bl(x),\quad C_{ms}(x),\quad L_e(i,x)
$$

所以接近 ±4 mm 时不能做真实非线性预测。

第五，`Re=7.2 Ω` 是固定常数。

这是 1 Ω 模式非常危险的建模乐观项。

因为 1 Ω 模式要求：

$$
7.2-6.2=1.0\Omega
$$

如果真实线圈因为温升变成 8.2 Ω，而控制器仍认为是 7.2：

$$
8.2-6.2=2.0\Omega
$$

目标直接从 1 Ω 变成 2 Ω。

因此 1 Ω 工作区最终必须有线圈 Re 的温度补偿/慢速标定，否则不可能保持高精度。

第六，外部声源驱动时特别需要关注再生能量。

当前 ±18 V 电源是理想电压源，相当于可以无限吸收返回电源轨的能量。真实电源不一定能够 sink current。

你的系统正好又是“外部声波→膜片→线圈发电→主动负阻抗”。

所以最终硬件一定还要检查：

$$
P_\mathrm{rail}(t)
$$

以及 rail pumping / bus overvoltage，而当前 SPICE 会因为理想电源而低估这一问题。

---

### 7. “full component”实际上仍有几块是理想行为模型

这也影响精度。

例如：

```spice
BVK_RAW VK_RAW 0 V = {soft(time)*(3.3*V(DAC_R)-0.62)}
```

这是理想数学增益/电平转换器。

真实硬件需要把 DAC 的大约 0–3 V 转换成：

$$
VK=-0.62\text{ V}\sim+9.28\text{ V}
$$

这一级真实运放、电阻、带宽、噪声、失调目前没有进入模型。

同样：

```spice
B_VSENSE_TRIM
B_ZSERVO
```

也是行为源。

因此这个所谓 `full_component_template` 更准确地说是：

> 主要信号链使用真实 AD633/OPA548/OPA1656/INA149 厂商宏模型，但 DAC 后级缩放、offset trim、servo 等部分仍然是理想化功能块。

所以现有动态结果其实还有一定程度的乐观性，而不是悲观性。

---

### 8. 你想要的“多个正弦甚至任意形状”在数学上完全可行

当前模型已经实现：

$$
R(t)=
R_0+
A_1\sin(2\pi f_1t+\phi_1)+
A_2\sin(2\pi f_2t+\phi_2)
$$

然后 clip 到 1–100 Ω。

继续扩展成：

$$
R(t)=R_0+\sum_k A_k\sin(2\pi f_kt+\phi_k)
$$

没有结构性问题。

任意形状也可以由 DAC LUT/PWL 实现。

但是当 R 随时间变化以后，这个系统就不是 LTI，而是 LTV 系统。外界如果有一个 `fa` 的声音，会产生：

$$
f_a\pm f_m,\quad
f_a\pm2f_m,\dots
$$

这样的声学/电气边带。

所以以后不能只问：

> “此刻的 R 是多少？”

而要同时看：

- 主载频的等效复阻抗；
- modulation sidebands；
- 是否产生净声学增益；
- 是否出现 parametric instability；
- 电源是否吸收/输出净能量。

---

### 9. 我对这个版本的最终判断

“负阻抗改变外界声压激励膜片的等效声学边界”这个原理是成立的；当前 SPICE 的机电耦合方向也是正确的。

固定低频状态已经足以证明原理，尤其大约 5–20 Ω 区域表现明显好于极端 1 Ω/100 Ω。

但是当前版本还不能完成你最核心的最终要求：

$$
R_\mathrm{target}=1\sim100\Omega
$$

且

$$
f_\mathrm{mod}=10\sim1000Hz
$$

同时在较宽外界声频范围内仍保持“接近纯电阻”的合成阻抗。

当前主要瓶颈不是 ngspice，也不是数值求解，而是实际控制链的带宽和相位。

项目以前做的 fast compensation 也已经给出了同一个方向：U4A/U4B 的反馈电容从 100 pF/220 pF 降到约 10 pF/22 pF 后动态表现明显改善，但仍未全范围通过。因此下一步不应该继续修 DC trim，而应该集中做前馈链相位补偿，或者转成真正的阻抗闭环。

另外，真正面向“被外界声音照射的反射膜”时，还必须把声学辐射阻抗/反射波模型加入 SPICE，否则电子部分即使完全通过，也只能证明“电气端等效阻抗”，不能证明真实“反射面声阻抗”。

后续这个项目我会继续按你说的方式计算：遇到大网格就按 `声频 fa`、`调制频率 fm`、`Rtarget 区域` 和时间段分别拆开跑，而不是减少测试范围。下一轮最值得做的是建立 `fa × fm` 二维声学动态网格，同时先修正 T/S 参数一致性和真实声辐射负载。

---

# you asked

message time: 2026-08-23 17:53:25

# U4B—OPA548局部异常独立 SPICE 仿真 Goal 与验证规划

## 1. 仿真目的

本次仿真不再建立完整的扬声器、AD633、DAC、ADC及阻抗合成系统，而只建立目前实板已经暴露异常的最小局部电路：

```text
TP7 / MUL_RAW
      ↓
U4B / OPA1656
      ↓
TP8 / VCMD
      ↓
R5 = 100 Ω
      ↓
OPA548 +IN

```

本次仿真的核心 Goal 是回答四个问题：

1. 为什么实板在 `OPA OFF` 状态下，TP7基本稳定，而TP8却出现约100～110 kHz的大幅振荡；
2. 为什么改变J1的OPA548供电电压后，TP8会从稳定方波变成不规则纹波；
3. 在反馈网络加入22～220 pF补偿电容后，振荡为什么能够减弱或消失；
4. 找到能够稳定U4B、同时尽可能不影响最终10～1000 Hz阻抗调制的最小补偿方案。

最终目标不是单纯得到“加220 pF以后不振”，而是建立：

> **故障复现 → 根因确认 → 修复参数扫描 → 修复后稳定性与带宽评估**

这一完整证据链。

实板测试已经发现“TP7干净、TP8出现约100～110 kHz大幅异常”，并且原始 `OPA ON` 会导致电源进入CC；同时也已经确认早期曾存在一次示波器跨TP2/TP8造成的测量伪影，因此本次仿真必须把真实振荡与测量负载影响分开。

---

## 2. 当前实板状态

目前已经基本排除MCU和DAC作为100 kHz振荡的直接来源。

已有测试链为：

```text
DAC1
→ TP6正常

DAC2
→ TP5具有正常可重复变化

TP7 MUL_RAW
→ 基本稳定

TP8 VCMD
→ 出现异常振荡

```

因此异常第一次明显出现于：

```text
TP7
 ↓
U4B
 ↓
TP8

```

实板主要现象为：

```text
J2 ≈ ±10 V

J1较低时：
TP8 ≈ 接近电源轨的大幅周期波形
频率 ≈ 100～110 kHz

U4B_N：
存在相同频率波形
与TP8基本同相
幅度明显小于TP8

J1提高到约±6 V以上：
TP8由规则振荡变为不规则纹波

```

同时，在最初测试中：

```text
OPA ON
→ 电源进入约70 mA CC
→ 5秒watchdog关闭OPA
→ 电流恢复

```

因此目前最合理的假设是：

```text
U4B局部动态异常
        ↓
TP8产生错误VCMD
        ↓
OPA548输入受到大幅高频驱动
        ↓
OPA ON后功率级参与
        ↓
出现异常耗流

```

但这个因果关系目前还没有被严格证明，因此正是本次SPICE仿真的主要任务。

---

# 3. 建立独立最小模型

第一版模型只保留：

```text
OPA1656 U4B
R15
R16
反馈补偿电容 Cfb
R5
OPA548输入级
J1供电
J2供电
探头等效负载

```

不加入：

```text
AD633
INA149
U4A
扬声器
RSH
MCU
DAC
ADC

```

TP7直接使用独立电压源模拟。

初始设置：

```text
V(TP7) = 0 V

```

并叠加很小的启动扰动，例如：

```text
1 mV脉冲

```

用于触发可能存在的不稳定模式。

这是必要的，因为理想SPICE模型在完全对称的0 V初始状态下，即使系统理论上不稳定，也可能长时间停留在数学上的零点。

---

# 4. 必须以实板参数重新建立模型

这里不能直接沿用现有旧SPICE模板。

当前已有SPICE模板中U4B仍存在：

```text
R_U4B_G = 1 kΩ
R_U4B_F = 19 kΩ

```

即闭环增益约20。

但当前实板实际参数为：

```text
R15 = 1 kΩ
R16 = 39 kΩ

```

所以：

[
A\_v=1+\frac{39k}{1k}\approx40
]

本次仿真必须修改为：

```text
R15 = 1 kΩ
R16 = 39 kΩ
R5  = 100 Ω

```

U4B使用OPA1656厂商宏模型。

OPA548使用现有厂商模型。

供电初始设为：

```text
J2：
ANA_P = +10 V
ANA_N = -10 V

J1：
PWR_P = +5 V
PWR_N = -5 V

```

OPA548首先保持Disable状态。

---

# 5. 第一阶段：复现实板100～110 kHz异常

第一轮：

```text
Cfb = 0 pF
J1 = ±5 V
J2 = ±10 V
TP7 ≈ 0
OPA548 = OFF

```

Transient建议至少仿真：

```text
2～5 ms

```

最大步长应明显小于100 kHz周期，例如：

```text
maxstep ≤ 100 ns

```

重点记录：

```text
V(TP7)
V(U4B_N)
V(TP8)
I(ANA_P)
I(ANA_N)
OPA1656 output current

```

第一目标是判断：

> 在TP7基本为零的条件下，模型能否自行产生接近100～110 kHz的持续振荡。

如果能够复现：

```text
TP7稳定
TP8振荡

```

说明实板异常可以由现有电路拓扑和器件动态特性解释。

如果完全不能复现，则不能直接否定实板结果，而应继续加入：

```text
TP8走线电容
OPA548输入电容
PCB寄生电容
电源ESR/ESL
示波器探头

```

逐步寻找振荡产生条件。

---

# 6. 第二阶段：判断OPA548输入是否参与振荡

保持U4B参数不变，对J1进行扫描：

```text
±4 V
±5 V
±5.5 V
±6 V
±6.5 V
±7 V
±8 V

```

每个工作点记录：

```text
TP8 Vpp
振荡频率
U4B_N Vpp
OPA548输入电流
J2供电电流

```

重点观察是否出现类似实板：

```text
低J1：
规则100kHz振荡

提高J1：
振荡突然改变为不规则状态

```

同时再做一个A/B：

```text
A：R5 = 100 Ω，并连接OPA548

B：断开R5，相当于OPA548输入完全隔离

```

判断标准非常明确。

如果断开R5后仍然出现相同振荡：

> 根因主要属于U4B局部环路。

如果断开R5后稳定，而连接OPA548后才振：

> OPA548输入负载是振荡成立的重要条件。

如果两者都振，但频率和幅值不同：

> U4B本身稳定裕量不足，OPA548输入进一步改变了极限环工作状态。

这一结果最符合目前的实板现象。

---

# 7. 第三阶段：补偿电容扫描

确认振荡机制以后，在：

```text
TP8 ↔ U4B_N

```

即R16两端并联反馈电容。

扫描：

```text
Cfb =
0 pF
4.7 pF
10 pF
22 pF
47 pF
100 pF
220 pF

```

其中当前已有220 pF，可以作为实板强补偿诊断值。

对应R16=39 kΩ，其近似反馈极点分别会逐渐下降。

特别是：

```text
22 pF  → 约185 kHz
47 pF  → 约87 kHz
100 pF → 约41 kHz
220 pF → 约18.5 kHz

```

因此220 pF应该能够非常明显地影响当前110 kHz异常。

每个值记录：

```text
是否持续振荡
TP8 Vpp
振荡频率
启动后的settling
J2电流

```

最终不是选择“电容最大”的方案，而是：

> **寻找能够可靠消除持续振荡的最小Cfb。**

---

# 8. 第四阶段：AC环路稳定性分析

Transient只能说明“振不振”，不能充分解释“为什么”。

因此必须增加U4B的AC loop-gain分析。

主要输出：

```text
0 dB crossover frequency
Phase Margin
Gain Margin

```

建议工程判据：

```text
Phase Margin < 30°
→ 明显风险

30～45°
→ 边缘稳定

≥45°
→ 基本可接受

≥55°
→ 更适合作为目标

```

然后建立：

```text
Cfb
↔
Phase Margin
↔
带宽

```

之间的关系。

理想结果可能类似：

```text
0p     → 不稳定
22p    → 裕量仍小
47p    → 接近可接受
100p   → 稳定
220p   → 很稳定但过补偿

```

具体数值必须由实际模型计算，不能预先假定。

---

# 9. 第五阶段：验证修复对1 kHz控制带宽的影响

因为最终系统需要：

```text
10～1000 Hz

```

电阻调制，所以不能只解决100 kHz自激。

对每个稳定的Cfb，在TP7输入：

```text
10 Hz
100 Hz
300 Hz
1000 Hz

```

小信号正弦。

测量：

```text
TP8增益
TP8相位

```

修复后的目标应为：

```text
1000 Hz范围内：
没有明显幅值损失
没有过大的额外相位延迟

同时：
100 kHz自激完全消失

```

如果：

```text
47p稳定
100p稳定
220p稳定

```

但47 pF的1 kHz相位性能最好，则优先47 pF。

这就是为什么220 pF不能因为“实板不振了”就直接定版。

---

# 10. 第六阶段：重新模拟OPA ON→CC

只有TP8已经稳定以后，才进入最终验证。

建立两组仿真：

```text
Case A：
Cfb = 0
TP8允许出现原始振荡
随后OPA ON

Case B：
使用最佳Cfb
TP8已经稳定
随后OPA ON

```

比较：

```text
J1电流
J2电流
TP8
OPA548输出

```

如果出现：

```text
Case A：
OPA ON → 大电流

Case B：
OPA ON → 电流恢复正常

```

则基本证明：

> U4B自激是原始OPA ON→CC的重要根因。

如果：

```text
Case B
仍然OPA ON→CC

```

则说明：

> U4B问题已经修复，但OPA548功率级仍存在第二个独立故障。

此时才继续单独建立OPA548输出级模型，检查反馈、RSH、R46、snubber及限流。

---

# 11. 最终仿真交付结果

本次独立SPICE任务最终应输出四项结论：

**第一，根因。**

明确回答100～110 kHz究竟来自：

```text
U4B自身稳定性
OPA548输入加载
二者共同作用
或PCB寄生因素

```

**第二，修复参数。**

得到类似：

```text
建议Cfb = XX pF
最小安全值 = XX pF
220 pF是否属于过补偿

```

而不是凭经验猜电容。

**第三，修复后性能。**

确认：

```text
TP8无持续100kHz振荡
相位裕量满足要求
J2异常耗流下降
10～1000Hz仍保持足够带宽

```

**第四，与原始CC问题建立因果关系。**

最终必须明确回答：

```text
修复TP8以后
OPA ON是否还会产生异常电流？

```

只有这一项通过，才可以宣布这轮“OPA ON→CC”排查形成完整闭环。

因此，这次独立SPICE仿真的核心并不是重新验证整个正弦电阻系统，而是非常具体地解决：

> **为什么TP7正常而TP8产生约100～110 kHz异常；OPA548输入为什么会改变这个振荡；最小补偿电容是多少；修复以后是否真正消除最初的OPA ON→CC，同时保留10～1000 Hz阻抗调制能力。**

完成这一局部模型以后，再把得到的最佳U4B参数放回完整阻抗合成SPICE模型进行最终动态Signoff，效率会远高于继续在整块实板上逐颗尝试电容。

---

# chatgpt response

我会按你这份局部验证规划直接做成独立模型，不再牵扯完整阻抗系统。先复现实板异常，再做 R5/OPA548 参与性 A/B、J1 扫描、Cfb 扫描、环路裕量和 10–1000 Hz 带宽，最后才做 OPA ON→CC 因果验证。

先指出一个电路层面的关键信号：你测到 `U4B_N` 与 TP8 同频、同相、幅值约小几十倍，本身正是 39 kΩ/1 kΩ 非反相反馈网络应有的现象，不能单独证明 U4B_N 在“发振”。真正要看的是断开 OPA548 输入、去掉探头负载后是否仍存在自激。

第一阶段已经得到很明确的否定结果：用 TI 的 OPA1656/OPA548 厂商宏模型、R15=1 kΩ、R16=39 kΩ、R5=100 Ω、J2=±10 V、J1=±5 V，TP7 施加 1 mV 启动扰动后，TP8 会回到约 19.57 mV 的静态偏置，没有任何 100–110 kHz 持续自激。OPA548 输入断开、10×/1×探头负载变化也都不产生振荡。

这轮独立 U4B—OPA548 局部 SPICE 已经按你的规划完成了主要验证。结果比“找到一个能止振的电容”更有价值，因为它把几种根因明显区分开了。

核心结论是：

> 当前 TI 厂商宏模型不支持“U4B 在 R15=1 kΩ、R16=39 kΩ、R5=100 Ω、正常 OPA548 输入负载下，本身会产生 100–110 kHz 自激”这个假设。

也就是说，实板的 100–110 kHz 异常里还缺少一个当前最小模型没有包含的真实因素。

### 1. 100–110 kHz 能否复现？

不能。

采用：

- OPA1656 TI 厂商宏模型；
- OPA548 TI 厂商宏模型；
- R15 = 1 kΩ；
- R16 = 39 kΩ；
- R5 = 100 Ω；
- J2 = ±10 V；
- J1 = ±5 V；
- OPA548 Disable；
- TP7 = 0 V，并注入 1 mV 启动扰动；
- transient 2 ms；
- maxstep = 100 ns；

最终 TP8 收敛到约：

$$
V_{TP8}\approx19.57\text{ mV}
$$

尾段振荡 Vpp 只有数值噪声级，没有任何 100–110 kHz 持续振荡。

更重要的是，以下 A/B 全都不振：

| 状态 | 结果 |
|---|---|
| OPA548 输入经 R5 连接 | 稳定 |
| R5/OPA548 输入完全断开 | 稳定 |
| 无探头负载 | 稳定 |
| 10×：约 10 MΩ // 10 pF | 稳定 |
| 1×：约 1 MΩ // 100 pF | 稳定 |
| 额外 200 pF | 稳定 |

因此目前可以排除：

> “正常示波器探头电容直接让当前 U4B 电路在 100 kHz 发振”。

你之前 TP2/TP8 跨接造成的测量伪影仍然完全可能，但那不是普通“探头负载”问题，而是错误电气连接。

---

## 2. U4B 本身稳定性怎么样？

比原先怀疑的好很多。

对 Cfb=0 的 U4B 做独立 loop-gain：

$$
f_c \approx 1.139\text{ MHz}
$$

$$
PM\approx62.3^\circ
$$

$$
GM\approx39.9\text{ dB}
$$

因此按照你定义的工程标准：

> ≥55°，属于比较健康的稳定状态。

不是 30° 左右的边缘系统。

Cfb 扫描：

| Cfb | 0 dB crossover | Phase Margin | Gain Margin |
|---:|---:|---:|---:|
| 0 pF | 1.14 MHz | 62.3° | 39.9 dB |
| 4.7 pF | 2.42 MHz | 117.5° | 24.1 dB |
| 10 pF | 7.58 MHz | 108.8° | 19.8 dB |
| 22 pF | 13.1 MHz | 85.9° | 16.5 dB |
| 47 pF | 16.3 MHz | 73.4° | 14.6 dB |
| 100 pF | 18.1 MHz | 66.9° | 13.5 dB |
| 220 pF | 19.0 MHz | 63.5° | 12.9 dB |

这里有个很值得注意的地方：

你是在 R16 两端并联 Cfb，因此随着频率升高，反馈阻抗下降，闭环噪声增益也下降。它并不是传统意义上“加电容降低 loop crossover”的简单主极点补偿。

所以不能用：

> “220 pF 把运放带宽压下来，因此稳定。”

这种简单解释。

---

## 3. OPA548 输入有没有参与？

有，而且找到了一个相当有价值的非线性转折点。

J1 扫描得到：

| J1 | OPA548 +IN 经 R5 的平均电流 | J2 正轨耗流 | TP8 |
|---:|---:|---:|---|
| ±4 V | ≈0 | 3.90 mA | 稳定 |
| ±5 V | ≈0 | 3.90 mA | 稳定 |
| ±5.5 V | ≈0 | 3.90 mA | 稳定 |
| ±6 V | 5.2 µA | 3.91 mA | 稳定 |
| ±6.5 V | 1.74 mA | 5.64 mA | 稳定 |
| ±7 V | 3.02 mA | 6.92 mA | 稳定 |
| ±8 V | 3.03 mA | 6.93 mA | 稳定 |

为什么恰好约 ±6～6.5 V 开始变化？

TI 的 OPA548 宏模型内部有约：

$$
BV\approx5.2\text{ V}
$$

的输入差分保护。

OPA548 Disable 时，其输出/反相输入停在接近负电源轨的位置，而 +IN 通过 R5 接近 0 V。

J1=±5 V 时，两输入间的差分还低于约 5.2 V。

J1继续升高后：

$$
|V_+-V_-|>5.2V
$$

模型里的输入保护开始导通。

结果就是：

> OPA548 即使处于 OFF，也开始通过 R5 对 TP8/U4B 形成非线性的毫安级负载。

这与实板的一个现象非常吻合：

> J1 提高到约 ±6 V 以上后，TP8 波形突然从规则状态变成另一种不规则状态。

所以目前我认为：

**OPA548输入参与实板异常的可能性很高。**

但当前模型告诉我们的更准确描述是：

> OPA548 OFF 状态下的输入非线性加载可以改变 U4B 的工作状态，但单靠这一机制还不足以产生 100 kHz 自激。

---

## 4. PCB/探头电容到底要多大才会让 U4B 真振？

我继续按你的要求增加 TP8 寄生电容。

结果非常清晰：

| TP8额外电容 | Phase Margin |
|---:|---:|
| 10 pF | 62.3° |
| 100 pF | 61.6° |
| 220 pF | 60.6° |
| 470 pF | 58.3° |
| 1 nF | 52.1° |
| 2.2 nF | 29.0° |
| 4.7 nF | **−12.2°** |
| 10 nF | −41.8° |

所以大约到：

$$
C_{TP8}\sim 4.7\text{ nF}
$$

才能明确把这个模型推入不稳定。

我又对 4.7 nF 跑了真实 transient。

确实自激：

$$
V_{TP8,pp}\approx4.96V
$$

但频率是：

$$
f_{osc}\approx1.32\text{ MHz}
$$

不是：

$$
100\sim110\text{ kHz}
$$

这一点很重要。

所以：

> 实板 100–110 kHz 不太像普通几十/几百 pF 输出电容导致的经典 OPA1656 capacitive-load oscillation。

甚至正常 1× 探头约 100 pF，离需要的几 nF 还有一个数量级以上。

---

## 5. 还有一个非常强的反证

我人为建立了一个真正的“4.7 nF 输出电容导致 U4B 不稳定”的压力模型，然后扫描 Cfb。

结果：

| Cfb | 4.7 nF负载下 PM |
|---:|---:|
| 0 pF | −12.2° |
| 4.7 pF | 27.8° |
| 10 pF | 28.1° |
| 22 pF | 16.6° |
| 47 pF | −1.7° |
| 100 pF | −16.1° |
| 220 pF | −24.6° |

也就是说，如果真实问题单纯是：

> OPA1656 输出直接驱动大电容，所以发振

那么增加到 100/220 pF 的 R16 并联电容在这个模型里反而会重新恶化稳定性。

因此，如果你的实板实际观察是：

> 220 pF 明确让 100 kHz 异常明显减弱/消失，

那么这反而进一步说明：

**实板异常并不像简单的 U4B capacitive-load instability。**

220 pF 很可能是在：

- 衰减进入 U4B 的 100 kHz 扰动；
- 改变某个非线性极限环；
- 减少 OPA548 输入保护参与程度；
- 改变当前最小模型里没有的 PCB/电源耦合路径；

而不是简单“修复 OPA1656 本身相位裕量”。

---

# 6. 那么 Cfb 为什么在实板可能有效？

因为它对 100–110 kHz 的闭环增益抑制非常明显。

无 Cfb：

$$
A_v\approx40
$$

也就是约：

$$
32.04\text{ dB}
$$

100/110 kHz 附近：

| Cfb | 100 kHz gain | 相对0pF抑制 |
|---:|---:|---:|
| 0 pF | 32.05 dB | 0 |
| 22 pF | 30.70 dB | ~1.35 dB |
| 47 pF | 28.09 dB | ~4 dB |
| 100 pF | 23.40 dB | ~8.7 dB |
| 220 pF | 17.23 dB | ~14.8 dB |

110 kHz 时 220 pF 的额外抑制约：

$$
15.6\text{ dB}
$$

所以，即使振荡的“源头”不是 U4B 自己，220 pF 也完全可能因为降低 U4B 对 100 kHz 信号/扰动的增益而把实板现象压掉。

这解释力比“220 pF增加相位裕量”更强。

---

# 7. 10–1000 Hz 会不会被补偿电容破坏？

不会严重影响。

1 kHz：

| Cfb | 增益变化 | 相位 |
|---:|---:|---:|
| 0 pF | 基准 | −0.04° |
| 22 pF | 几乎0 | −0.34° |
| 47 pF | 几乎0 | −0.68° |
| 100 pF | −0.003 dB左右 | −1.41° |
| 220 pF | −0.013 dB左右 | −3.05° |

所以单纯按你现在的：

$$
10\sim1000Hz
$$

阻抗调制频率看，甚至 220 pF 都不算严重。

但这里必须重新提醒我们之前发现的问题：

> 阻抗调制频率 ≠ 被控制的声频/电流 carrier 频率。

到了 20 kHz：

| Cfb | 增益相对DC | 相位 |
|---:|---:|---:|
| 47 pF | −0.25 dB | −13.4° |
| 100 pF | −0.98 dB | −26.1° |
| 220 pF | **−3.41 dB** | **−46.0°** |

所以如果最终电声阻抗控制要覆盖高音频：

**220 pF 确实偏重。**

---

# 8. 当前我对 Cfb 的选择

这轮不能诚实地宣布：

> “最小安全值 = XX pF”

因为最关键的前提没有成立——SPICE 中：

$$
Cfb=0
$$

本身就是稳定的。

所以现在不存在由该模型计算出的“最小止振电容”。

但如果把目标定义成：

> 尽量压制实板 100–110 kHz，同时尽量不伤害最终带宽，

我会把候选排序为：

**47 pF → 100 pF → 220 pF**

其中目前最值得实板重点验证的是：

$$
\boxed{100\text{ pF}}
$$

原因是：

- 1 kHz 几乎无幅度损失；
- 只有约 1.4° 相移；
- 100–110 kHz 可得到约 9 dB 抑制；
- 比 220 pF 对 10–20 kHz 的破坏明显小。

所以目前可以说：

> **100 pF 是本轮局部 SPICE 给出的首选折中候选。**

但不能说：

> **100 pF 已经被证明是最小安全值。**

这两句话区别很重要。

---

# 9. OPA ON → CC 的关系

这里得到了一条很强的“后果证据链”。

由于局部模型不自行产生 105 kHz，我没有伪造一个所谓“成功复现”。

而是另外做了压力测试：

人为向 U4B 输入 105 kHz，使 Cfb=0 时：

$$
TP8\approx16.05V_{pp}
$$

也就是模拟你实板看到的“接近轨的大幅 100–110 kHz VCMD”。

随后让 OPA548 ON，并接入当前项目里的主要 HF 负载：

- speaker：7.2 Ω + 0.2 mH；
- snubber：4.7 Ω + 47 nF。

结果：

| Cfb | TP8 Vpp | OPA548输出Vpp | J1平均输入功率 | OPA548输出Irms |
|---:|---:|---:|---:|---:|
| 0 pF | 16.05 V | 8.21 V | **0.918 W** | **145 mA** |
| 10 pF | 15.26 V | 8.21 V | 0.890 W | 138 mA |
| 22 pF | 13.53 V | 8.17 V | 0.819 W | 133 mA |
| 47 pF | 9.86 V | 8.11 V | 0.508 W | 95.6 mA |
| 100 pF | 5.67 V | 5.84 V | 0.307 W | 55.9 mA |
| 220 pF | 2.78 V | 2.86 V | 0.142 W | 24.2 mA |

无补偿时，J1两路模型平均电流达到约：

$$
68mA
$$

和

$$
116mA
$$

量级。

所以你的实板：

> OPA ON → 约70 mA CC

从电路物理上是完全合理的。

尤其是 4.7 Ω / 47 nF snubber 在 100 kHz 已经不是“几乎开路”。

47 nF 在 100 kHz：

$$
X_C\approx33.9\Omega
$$

和 4.7 Ω 串联以后，对 100 kHz 功率级是一个相当明显的负载。

所以现在可以建立：

$$
100kHz\ 大幅VCMD
$$

↓

$$
OPA548\ 高频大幅输出
$$

↓

$$
speaker+snubber\ 高频电流
$$

↓

$$
J1\ 电流显著增加
$$

↓

$$
电源进入CC
$$

这条链是 SPICE 支持的。

但是还差第一箭头：

> **究竟什么在实板上产生了原始 100–110 kHz TP8？**

这轮还没有找到。

因此现在的准确结论是：

> **TP8的100–110 kHz异常足以解释后续OPA ON→CC；但尚不能证明这个100–110 kHz由U4B自身稳定性问题产生。**

---

# 10. 当前根因优先级

现在我会把根因判断调整为：

**“U4B自身相位裕量不足”已经明显降级。**

目前更值得怀疑的是：

1. OPA548 Disable 状态输入的非线性加载 + 实板寄生；
2. U4B/OPA548 之间 PCB 上实际存在但 SPICE 未包含的耦合；
3. ANA ±10 V 电源上的实板 HF 纹波/公共阻抗；
4. 元件焊接、阻值、污染或反馈路径实际与图纸不一致；
5. 某个从 OPA548/电源返回 TP8/U4B 的寄生反馈；
6. 测量接线。

我还额外做了假设性的 J2 ESR/ESL 压力测试：

- 0.1–5 µH；
- 0.05–0.5 Ω；
- 100 nF + 10 µF 本地去耦；

仍然没有产生持续振荡。

因此普通“电源线有一点电感”也不足以直接解释。

---

## 下一次实板最有判别力的一个测试

现在最值得做的不是继续随意换 Cfb。

而是：

$$
\boxed{\text{真正断开 R5 一端}}
$$

然后保持其他所有条件不变，再看 TP8。

如果：

**R5断开后 TP8 仍然100–110 kHz：**

那 OPA548 基本退出根因，继续集中检查 U4B、J2、电源去耦、39k/1k反馈和 PCB。

如果：

**R5断开后 TP8立即稳定：**

那么这轮 SPICE 找到的 OPA548 Disable 输入非线性加载就会成为非常强的根因线索，下一版模型就应该专门建：

$$
OPA548\ OFF输入保护
+
R5
+
PCB寄生
+
实际J1供电阻抗
$$

而不是再研究整个阻抗合成系统。

完整报告和所有关键 CSV、netlist、运行脚本已经整理：

[下载完整 U4B—OPA548 局部 SPICE 报告](sandbox:/mnt/data/u4b_local_spice/U4B_OPA548_local_SPICE_report.md)

[下载完整仿真交付包 ZIP](sandbox:/mnt/data/U4B_OPA548_local_SPICE_deliverable.zip)

其中包含 J1 扫描、Cfb transient、loop margin、带宽、寄生电容压力测试、供电寄生压力测试和 105 kHz→OPA ON 高耗流验证的全部关键结果。

---

# you asked

message time: 2026-08-24 15:30:21

这个 SPICE 结果其实非常有价值，因为它把之前最直观的一个判断推翻了：

> **问题核心已经不应该定义为“U4B 原理设计天然不稳定”。更准确的定位是：实板上的 U4B B 通道没有按照理想的** **`R15=1k / R16=39k + OPA1656`** **闭环在工作。**

模型在 `Cfb=0` 时有约 62.3° 相位裕量，正常探头、200 pF负载以及相当大的供电寄生都没有产生实板的 100～110 kHz 自激。

所以现在根因搜索范围已经明显缩小。

## 1. 哪些原因现在可以基本降级

第一，**不是 MCU/DAC/AD633 产生了 100 kHz**。你实测 TP7 干净，而异常第一次出现在 TP8。

第二，**不是正常 OPA1656 + 1k/39k 这个拓扑本身天然会振**。SPICE 的 nominal model 是稳定的：

```text
Cfb = 0
Loop crossover ≈ 1.14 MHz
PM ≈ 62°
GM ≈ 40 dB

```

这已经不是“边缘稳定”。

第三，**不是普通示波器探头电容导致的**。模型一直加到 220 pF，PM 仍约 60°；要到约 2.2 nF 才明显危险，4.7 nF 才真正模拟出自激，而且频率约 1.32 MHz，不是实板的 100～110 kHz。

第四，**220 pF 不能再被解释成“修复了U4B设计缺陷”**。因为模型里没220 pF原本就稳定。220 pF真正做的是显著压低100 kHz附近的增益，所以它可以“压住症状”，但不等于找到了症状产生的根因。

---

# 2. 现在最可能的核心原因

我会把嫌疑重新排序成：

### 第一嫌疑：U4B 的实际负反馈没有真正进入 U4 pin6

这是目前我认为最值得优先排除的。

理论结构：

```text
                 R16 39k
TP8 OUT ─────────/\/\/\────●──── U4 pin6 (-IN)
                            │
                           R15 1k
                            │
                           AGND

```

SPICE假定这个连接是完美的。

但是实板可能出现：

```text
R15正常
R16正常

R15/R16交点 ─────●
                  X   ← 虚焊/裂焊/接触异常
                pin6

```

这里有一个很容易被骗的地方：

即使 U4 pin6 根本没有焊好，你测所谓的：

```text
U4B_N

```

仍然会看到100 kHz。

因为R15/R16本身仍然形成分压：

```text
TP8振荡
 ↓
39k
 ↓
U4B_N测试焊盘
 ↓
1k
 ↓
AGND

```

所以：

> **“U4B\_N和TP8同频、同相”并不能证明这个反馈信号真的进入了OPA1656 pin6。**

这正是 nominal SPICE 永远无法模拟出来的实板故障。

而且你的实测：

```text
TP7 ≈ 干净
U4B_N ≈ 0.9 Vpp
TP8 ≈ 大幅100~110 kHz

```

对于一个正常闭环的OPA1656来说非常异常。

---

# 3. 第二嫌疑：U4B这个通道已经损坏

这也属于高概率项。

SPICE使用的是：

```text
“健康的OPA1656”

```

它不可能模拟：

```text
输出级损伤
输入级损伤
局部ESD损伤
内部补偿异常
B通道部分失效

```

而测试过程中曾经发生过：

```text
普通示波器黑夹错误接TP8
→ TP8被强制拉到示波器地
→ J2从约20mA冲到70mA

```

TP8正是U4B输出。

这一次操作确实给U4B输出级施加过很强的负载。

但这里不能倒果为因：原来的 `OPA ON→CC` 在这次错误示波器连接之前就已经存在。因此目前不能说“示波器一定把U4烧坏了”。

只能说：

> **从发现100 kHz自激之后的状态来看，U4B损伤已经成为SPICE无法覆盖、但实板必须排除的高优先级原因。**

而且U4A正常并不能证明U4B正常。它们虽然在同一个OPA1656封装里，却是两个独立放大通道。

---

# 4. OPA548是什么角色？现在不是第一根因，更像“第二参与者”

SPICE得到的一个结果与实板非常吻合：

```text
J1 ≤ ±5.5V
OPA548 +IN加载很小

约±6V开始变化

±6.5V以后
经R5的输入电流明显增大

```

这很好地解释了实板为什么出现：

```text
J1 < 6V
→ 一种100kHz规则振荡

J1 > 6V
→ 波形变成另一种不规则纹波

```

也就是说：

```text
异常TP8
 ↓
R5
 ↓
OPA548输入保护/非线性
 ↑
J1电压改变

```

这条反馈加载确实存在。

但是它**不能作为100 kHz的最初根因**。

原因很简单：

模型中加入这个非线性以后仍然没有自己起振。

所以我现在对它的定义是：

> **OPA548 Disable输入是“振荡状态改变器/非线性负载”，不是目前已经证明的“振荡发生器”。**

特别是实板在 J1<6 V 时已经存在规则100 kHz振荡，这更说明问题首先应该继续查 U4B一侧。

---

# 5. SPICE报告还有一个需要谨慎的地方

我进一步检查了交付包里的CSV和测试电路。

OPA548 Disable模型在不同J1电压下表现出了很强的非线性状态变化，所以：

```text
6.0 V
6.5 V
5.2 V保护阈值

```

这些数字适合用于解释趋势，但**不能直接当成真实OPA548实物的精确门限**。

因此本次仿真真正可靠的是：

```text
“OPA548输入加载随J1发生明显非线性变化”

```

而不是：

```text
“实物一定在6.500V发生某个确定事件”

```

这一点需要区分。

---

# 6. “OPA ON → 70mA CC”反而已经比较容易解释

报告的105 kHz压力测试非常有价值：

```text
TP8大幅105kHz
↓
OPA548开启
↓
OPA548功率级输出高频
↓
功率电流明显增加

```

无Cfb时模拟出的OPA548输出约8.2 Vpp，已经足够造成70mA级甚至更高的供电电流。

但这里有一个需要修正的逻辑点：

**报告里的Stage 6加入了7.2 Ω + 0.2 mH扬声器模型，而你原来这轮 OPA ON 调试实际上是J4空载。**

所以 Stage 6 不是原始实验条件的严格复现。

不过这不意味着解释失败。

因为你的功率输出还有：

```text
4.7Ω + 47nF
snubber / Zobel

```

在105 kHz时，47 nF的容抗只有约32 Ω。

因此如果OPA548输出约8.2 Vpp，**光这一条snubber支路就已经可以产生接近0.09 A RMS量级的高频电流**。

也就是说即使：

```text
J4 = 空载

```

只要：

```text
TP8 = 大幅100kHz
↓
OPA ON
↓
OPA548输出跟着100kHz

```

仍然完全有可能：

```text
snubber吃掉大量HF电流
↓
J1碰70mA CC

```

所以我现在认为：

> **“OPA ON→CC”很可能已经不是一个独立神秘故障，而是100 kHz异常进入功率级后的直接后果。**

下一版SPICE应把Stage 6重新跑成：

```text
J4 OPEN
只保留真实snubber

```

这样才能与原始测试完全对应。

---

# 7. 因此当前真正的“核心问题”可以压缩成一句话

现在不是：

> 为什么OPA548一开就70mA？

而应该变成：

> **为什么健康OPA1656模型在完全相同1k/39k参数下非常稳定，而实际U4B却在TP7安静时产生100～110 kHz接近电源轨的输出？**

这才是根因问题。

目前最合理的答案不是“缺220pF”，而是：

> **实板U4B闭环存在模型里没有的异常，最优先怀疑 pin6负反馈实际连接/焊接异常，其次是U4B器件本身异常；OPA548 Disable输入的非线性加载在后面参与并改变振荡形态。**

---

# 8. 现在只需要三个实验，就能真正定位

我不建议继续扫十几个TP。

### 实验1——最重要：直接证明 pin6 真的接上了

全部断电。

不要测“U4B\_N焊盘到TP8”。

要把万用表探针真正碰到：

```text
U4 pin6 金属引脚本身

```

分别测：

```text
U4 pin6金属脚 → U4B_N的R15/R16交点
≈ 0Ω

U4 pin6金属脚 → TP16
≈ 1kΩ

U4 pin6金属脚 → TP8
≈ 39kΩ

```

关键是：

**表笔要碰芯片腿，而不是碰同一焊盘。**

如果第一项不通或不稳定：

> 根因基本已经找到——U4B负反馈没有真正进入OPA1656。

这比继续焊220pF重要得多。

---

### 实验2——不拆R5也能判断OPA548到底拉了多少电流

如果R5太小，不方便抬脚，可以不拆。

两通道：

```text
CH1 → TP8
CH2 → R5的OPA548侧焊盘

两个GND → TP16

```

示波器：

```text
MATH = CH1 - CH2

```

那么：

[
I\_{R5}=\frac{V\_{TP8}-V\_{OPA548+IN}}{100\Omega}
]

保持：

```text
OPA OFF
J1 = ±5V
J2 = ±10V

```

看100 kHz时R5两端压差。

如果：

```text
TP8振得非常大
但R5压差很小

```

那么：

> OPA548不是振荡源，继续查U4B。

如果：

```text
R5上存在明显100kHz压降

```

比如几十到几百mV：

> OPA548输入正在以mA级动态电流显著加载TP8，需要把真实OPA548输入网络纳入根因模型。

这项测试可以部分替代“抬R5”。

---

### 实验3——如果反馈连接正常，直接处理U4

如果：

```text
pin6确实连接正常
+
R5动态电流很小
+
TP7仍然干净
+
TP8仍100kHz满幅

```

这时候我不会再继续调补偿。

优先：

```text
重焊 U4 pin5 / pin6 / pin7

```

再测试。

如果没有改变：

**直接换一颗新的OPA1656。**

换完以后：

```text
Cfb仍保持DNP
OPA OFF

```

先看TP8。

如果：

```text
旧U4 → 100kHz
新U4 → TP8稳定

```

那么根因就真正闭环：

> **U4B器件/焊接问题。**

这比“加220pF不振了”强得多。

---

# 9. 220pF现在应该放在什么位置

220 pF仍然有用，但是它现在应该叫：

> **诊断/抑制措施**

不是：

> **根因修复。**

因为仿真明确告诉我们：

```text
正常U4B：
0pF就稳定

```

220pF只是把100～110kHz的传递再压低约15.6dB。

所以如果：

```text
加220p
→ TP8不振
→ OPA ON不CC

```

能够证明：

```text
100kHz异常确实导致了CC

```

但仍不能证明：

```text
100kHz为什么产生

```

这是两个不同问题。

最终若需要保留更宽声频性能，报告本身也显示100pF比220pF更加折中：100pF在1kHz只有约−1.4°相位，而220pF到20kHz已经产生约−3.4dB、−46°的明显影响。

---

## 当前最终诊断

我会把当前根因概率排序写成：

```text
最高：
U4 pin6 / R15-R16反馈实际焊接连接异常

很高：
U4B通道器件异常/损伤

中等：
OPA548 Disable输入非线性加载 + 实际寄生
（确定参与，但不像第一振荡源）

较低：
U4局部供电去耦/PCB寄生异常
前提是实物C15/C16等确实装对

很低：
普通示波器探头电容导致

基本否定：
正常OPA1656 + 1k/39k拓扑天然100kHz不稳定

```

因此，**现在不要优先继续研究补偿值。最关键的一刀是“U4 pin6金属腿的真实连续性”，第二刀是“R5两端100kHz压降”，第三刀才是重焊/替换U4。**

做完这三刀，基本就能从“仿真缺失因素”进一步收敛到具体的器件或连接问题。

\*\*\*

基于以上判断，尝试各种假设去做SPICE，尝试找到一种SPICE构造假设，即单个PCB错误，并且是加工商常见的错误，符合我们讨论中的成立和不成立的问题，比如引脚或者其他。
这个时间可能很长，因为需要多轮SPICE调试，多个角度假设和规划，但是这个很有必要，请深入完成。

---

# chatgpt response

我会把这次任务当成“单点 PCB/装配故障反推”来做，不预设 pin6 虚焊就是答案。会优先构造加工商常见、且能同时满足“TP7干净、TP8约100–110 kHz大幅振荡、J1升高后波形改变、nominal SPICE稳定、220 pF能压症状”的单一故障假设，并逐个用 SPICE 淘汰。

这类反推不能只测“完全断路/完全短路”，因为冷焊最常见的电气表现往往是“高接触电阻 + 极小寄生电容”，它可能恰好产生额外极点。第一批我会扫 U4 的 pin5/pin6/pin7 接触故障、R15/R16 开路/错值、R5 错值和常见焊桥；只有能在粗扫描里接近 100 kHz 的假设才进入 2–5 ms 精细仿真。

粗扫描现在已经进入真实厂商宏模型计算；163 个 pin 接触组合明显比 nominal 测试昂贵，所以我不会让一次大批量超时拖住全部结果。接下来按 pin6、pin7、pin5 分组分别跑，并优先保留接近 80–150 kHz 且 TP8 为伏级的候选。

这轮多轮 fault-injection SPICE 已经找到一个目前解释力显著高于其他假设的“单一 PCBA 故障”。

结论不是“pin6 完全开路”，而是更具体的：

> **U4B pin6（−IN）存在非润湿/裂焊/虚焊形成的高阻接触，等效接触电阻约 1.6–2.0 MΩ，板上 R15/R16 网络本身仍然完好。**

这个构造非常关键，因为它同时满足此前看起来互相矛盾的现象：

> TP7可以很干净；U4B_N测试点看起来仍然“反馈正常”；健康 nominal SPICE 不振；真正进入 OPA1656 pin6 的反馈却已经严重失真；共振频率自然落到约100–110 kHz；OPA548不需要成为最初振荡源；J1变化会改变振荡形态；22–220 pF 会强烈压制症状；OPA ON 后即使 J4 OPEN，仅真实 snubber 就足以产生接近 CC 的电流。

而且非润湿、poor wetting、open/partially soldered joint 本身就是实际 SMT 装配中存在的典型缺陷类别。TI 的资料也把 gull-wing 焊点的 wetting/non-wetting 作为焊接质量问题讨论；装配资料同样把 poor wetting/open solder joint 列为典型回流缺陷。([Texas Instruments](https://www.ti.com/jp/lit/pdf/szza004?utm_source=chatgpt.com))

## 1. 最重要的新发现：pin6“完全断”反而不是最佳模型

我首先把很多直观故障都实际塞进了 SPICE：

| 单一故障假设 | SPICE结果 | 与实板100–110 kHz匹配 |
|---|---|---|
| R16 开路/错值 | DC跑偏、饱和或稳定改变 | 差 |
| R15 开路/错值 | 可严重降低稳定性，但主要共振在数百kHz～MHz | 差 |
| pin6 完全开路 | 没有形成目标100–110 kHz大振荡 | 差 |
| pin5 接触不良 | 没有目标模式 | 差 |
| pin7 输出脚接触不良 | 没有目标模式 | 差 |
| R5 错值/短路/大阻 | 不能独立产生目标模式 | 差 |
| pin5-pin6 / pin6-pin7 等焊桥 | 主要表现为DC异常/饱和 | 差 |
| TP8正常探头电容 | 不振 | 已基本否定 |
| TP8约4.7 nF | 能振，但约1.32 MHz | 频率不符 |
| 去耦异常 | 常规范围不振 | 较差 |
| 极端30 µH供电寄生+缺去耦 | 约167 kHz | 能振但物理条件过于极端 |
| OPA548 OFF输入非线性 | 能改变U4B负载 | 是参与者，不是第一源 |
| **pin6 MΩ级高阻接触** | **100–110 kHz高Q共振** | **高度匹配** |

所以目前不是宽泛地说“反馈可能虚焊”。

可以进一步缩成：

$$
\boxed{R_{\text{contact,pin6}}\approx1.6\sim2.0\ {\rm M\Omega}}
$$

这一非常具体的故障窗口。

---

# 2. 最惊人的结果：接触电阻直接“调”出了实板的频率

我重新把 OPA1656 的**物理引脚**与板上的 `U4B_N` 节点拆开：

```text
TP8
 │
39k R16
 │
 ●──────── U4B_N测试点
 │
1k R15
 │
GND

但：

U4B_N ●── Rcontact_fault ── U4 pin6 metal lead
```

然后扫描 `Rcontact_fault`。

考虑一个很小的 0.05 pF 焊点跨隙寄生后：

| pin6接触电阻 | 共振峰 |
|---:|---:|
| 1.40 MΩ | 120.0 kHz |
| 1.50 MΩ | 116.1 kHz |
| 1.60 MΩ | 112.5 kHz |
| **1.65 MΩ** | **110.4 kHz** |
| 1.70 MΩ | 108.9 kHz |
| 1.75 MΩ | 107.4 kHz |
| **1.80 MΩ** | **105.9 kHz** |
| 1.85 MΩ | 104.5 kHz |
| 1.90 MΩ | 103.0 kHz |
| 1.95 MΩ | 101.6 kHz |
| **2.00 MΩ** | **100.7 kHz** |
| 2.20 MΩ | 95.7 kHz |

也就是说：

$$
\boxed{1.65\sim2.0\,{\rm M\Omega}}
$$

恰好把共振峰扫过：

$$
\boxed{100\sim110\,{\rm kHz}}
$$

这不是预先把一个 LC 调到105 kHz得到的。

SPICE 中没有增加一个人为的105 kHz谐振器。

它是：

> OPA1656厂商宏模型已有的输入动态特性 + 正常39k/1k反馈 + 一个pin6高阻接触

自己产生的。

[下载 pin6 精细频率映射](sandbox:/mnt/data/pcb_fault_search/pin6_fine_map.csv)

---

# 3. 为什么这个故障以前特别容易漏掉

这是它解释力最强的地方。

假设：

$$
R_{contact}=1.8M\Omega
$$

板上的 R15/R16 仍然完全正常。

所以你拿表从：

```text
U4B_N测试点 → TP8
```

依然得到：

$$
39k\Omega
$$

而：

```text
U4B_N测试点 → GND
```

依然得到：

$$
1k\Omega
$$

示波器测 U4B_N 也仍然会看到：

$$
V_{U4B_N}\approx\frac{V_{TP8}}{40}
$$

本次 transient 得到：

$$
\frac{V_{U4B_N}}{V_{TP8}}\approx0.02499
$$

几乎就是理论：

$$
1/40=0.025
$$

更重要的是，相位：

```text
TP8                    reference
U4B_N board test node  ≈ -0.004° relative to TP8
actual U4 pin6         ≈ -80.2° relative to TP8
```

所以示波器会告诉你：

> “U4B_N和TP8完全同相，反馈分压也正确。”

但真正发生的是：

> **测试点上的反馈正确；真正进入硅片 pin6 的反馈已经落后约80°。**

这非常接近你之前提出的“U4B_N会骗人”，但 SPICE 把它进一步定量化了。

---

# 4. 为什么1.8 MΩ这么危险

nominal：

$$
R_{contact}\approx0
$$

得到：

$$
f_c\approx1.139MHz
$$

$$
PM\approx62.3^\circ
$$

非常健康。

随着 pin6 接触电阻增加：

| Rcontact | crossover | PM |
|---:|---:|---:|
| 10 kΩ | 965 kHz | 32.8° |
| 33 kΩ | 681 kHz | 15.8° |
| 100 kΩ | 429 kHz | 7.7° |
| 330 kΩ | 244 kHz | 3.8° |
| 1 MΩ | 142 kHz | 2.15° |
| **1.8 MΩ** | **106 kHz** | **1.63°** |
| 2.2 MΩ | 95.9 kHz | 1.48° |
| 3.3 MΩ | 78.4 kHz | 1.24° |

这意味着：

> nominal设计的62°相位裕量，被一个pin6高阻焊接故障吃到只剩约1–2°。

它不再是“OPA1656天然不稳定”。

而变成：

$$
\boxed{\text{反馈信号没有真正低阻地进入 }-IN}
$$

---

# 5. 更直接的证据：闭环在105.9 kHz出现巨大的共振峰

对：

$$
R_{pin6}=1.8M\Omega
$$

闭环频响得到：

无额外 contact C 时，共振峰大约：

$$
105.7kHz
$$

共振 peaking：

$$
+38.6dB
$$

考虑 0.05 pF 的接触跨隙寄生：

$$
f_{peak}\approx105.7kHz
$$

依然存在：

$$
+29.2dB
$$

额外 peaking。

甚至把跨隙电容增加到 1 pF，仍然存在约：

$$
9.4dB
$$

的100 kHz附近 peaking。

所以这个机理对“小寄生电容到底是0.02还是0.1 pF”并不脆弱。

[下载接触寄生电容扫描](sandbox:/mnt/data/pcb_fault_search/pin6_contactC_closed.csv)

---

# 6. “TP7干净、TP8却接近轨”也能重构

然后我没有给 TP7 大信号。

只给：

$$
2mV_{pk}
$$

的105.93 kHz微小扰动。

对于理想 pin6：

这只是一个非常小的输出。

但是：

$$
R_{pin6}=1.8M\Omega
$$

后，TP8 transient 达到：

$$
\boxed{13.9V_{pp}}
$$

也就是说：

```text
TP7：
几mV级，很容易在较大垂直量程下看起来“基本干净”

TP8：
十几Vpp
```

非常接近你的实际描述。

输入幅度扫描更明显：

| TP7 105.93kHz Vpk | TP8 Vpp |
|---:|---:|
| 0.1 mV | 0.67 V |
| 0.2 mV | 1.34 V |
| 0.5 mV | 3.53 V |
| 1 mV | 7.08 V |
| **2 mV** | **13.91 V** |
| 3 mV | 17.05 V |

到了0.5–3 mV输入以后，输出已经明显进入非线性，因此不再是简单线性倍数。

这给出一个非常合理的实板路径：

```text
极小的100kHz噪声/纹波/耦合
          ↓
正常板完全无害
          ↓
pin6高阻反馈故障
          ↓
105kHz高Q共振
          ↓
被放大几十dB
          ↓
TP8变成伏级乃至接近电源轨
```

因此根因不需要 MCU/DAC 本身“生成一个大100 kHz”。

---

# 7. 但这里必须保持一个严格的边界

这是目前还没有完全闭环的部分。

在 TI nominal macro 的精确参数下：

$$
PM\approx+1\sim2^\circ
$$

仍然是微小的正相位裕量。

因此只给一次：

```text
1mV startup pulse
```

SPICE得到的是大约105 kHz的长时间 ringing，而不是数学上永远不衰减的自激。

Cfb=0，J1=±5 V 时：

$$
\tau_{\rm decay}\approx102\mu s
$$

J1=±6.5 V：

$$
\tau_{\rm decay}\approx230\mu s
$$

而且尾部残余振铃明显增加。

所以我不会声称：

> “已经用一个pin6故障在TI nominal宏模型中100%产生了无限持续的自激。”

现在真正证明的是：

> **pin6 MΩ级虚焊可以把一个原本PM≈62°的系统推到105 kHz附近、PM≈1°的极高Q边界状态。**

真实器件的 GBW/相位、PCB寄生、噪声、OPA548输入非线性以及宏模型误差只需要再移动非常小的量，就可能跨过：

$$
PM=0^\circ
$$

进入真实持续极限环。

这比人为加4.7 nF再得到1.32 MHz自激更符合实板。

[启动扰动/振铃结果](sandbox:/mnt/data/pcb_fault_search/pin6_impulse.csv)

---

# 8. J1≈6 V后波形为什么变化，也开始对上了

这是第二个很强的交叉验证。

pin6=1.8 MΩ、Cfb=0：

J1=±5 V：

$$
PM\approx1.63^\circ
$$

到了厂商 OPA548 macro 的非线性转折附近：

J1=±6.5 V：

$$
PM\approx0.68^\circ
$$

也就是说 OPA548 OFF 输入正常存在的非线性加载，把本来就只剩约1–2°的 U4B 再推向稳定边界。

细扫显示最低点正好在模型约6.5 V附近。

而 transient 的启动振铃衰减时间：

$$
102\mu s\rightarrow230\mu s
$$

也增加了一倍以上。

在持续105.9 kHz微扰下，输出THD随J1也发生很大变化。例如相同2 mV激励：

```text
J1=5.5 V → THD约48%
J1=6.5 V → THD约74%
J1=8 V   → THD约84%
```

所以非常容易出现：

```text
低J1：
较规则的极限环/共振

提高J1：
OPA548输入保护开始显著参与
→ 非线性阻尼/加载改变
→ 波形变乱
```

这正好符合实板。

但仍要保持之前的限制：

> 6.5 V 是 OPA548 宏模型的数值，不是我对真实芯片精确门限的预测。

真正可靠的是“J1改变会强烈扰动这个已经极度边缘化的环路”。

[下载 pin6 × J1 × Cfb 环路扫描](sandbox:/mnt/data/pcb_fault_search/pin6_cfb_j1_ac.csv)

---

# 9. 220 pF为什么有效，现在出现了更好的解释

这是我认为最漂亮的一部分。

在 nominal 健康U4B里：

$$
Cfb=0
$$

本来就有62° PM。

所以220 pF不可能叫“修复OPA1656设计”。

但在：

$$
R_{pin6}=1.8M\Omega
$$

这个故障模型里：

Cfb=0：

$$
f_c\approx105.96kHz,\quad PM\approx1.63^\circ
$$

Cfb=100 pF：

$$
PM\approx66.7^\circ
$$

Cfb=220 pF：

$$
PM\approx43^\circ
$$

也就是说反馈电容提供了一条高频旁路：

```text
TP8
 │
 ├── R16 39k ──┐
 │              │
 └── Cfb ───────┤→ NFB_BOARD
                 │
              bad pin6 contact
```

它不是在“修一个本来不稳定的OPA1656”。

而是在：

> **绕过/补偿那个高阻 pin6 接触故障导致的高频反馈损失。**

这解释完全不同。

---

# 10. transient甚至把实板“加电容就消失”重构出来了

仍然：

$$
R_{pin6}=1.8M\Omega
$$

TP7只含2 mVpk /105.93 kHz：

| Cfb | TP8 Vpp |
|---:|---:|
| 0 | **13.91 V** |
| 4.7 pF | 2.68 V |
| 10 pF | 1.41 V |
| 22 pF | 0.679 V |
| 47 pF | 0.327 V |
| 100 pF | 0.156 V |
| 220 pF | **0.072 V** |

甚至考虑更保守的0.05 pF虚焊跨隙电容：

| Cfb | TP8 Vpp |
|---:|---:|
| 0 | **4.70 V** |
| 4.7 pF | 1.96 V |
| 10 pF | 1.19 V |
| 22 pF | 0.629 V |
| 47 pF | 0.318 V |
| 100 pF | 0.155 V |
| 220 pF | **0.0725 V** |

因此：

> “220 pF能够让实板症状明显减弱/消失”

现在反而成了支持 pin6 高阻反馈故障的证据之一。

[更保守0.05 pF模型的Cfb结果](sandbox:/mnt/data/pcb_fault_search/pin6_resonance_transient_c005.csv)

---

# 11. R5断开测试也有明确预测

我把 OPA548 输入真正断开。

在 pin6=1.8 MΩ 故障下：

```text
R5=100Ω，OPA548 connected:
TP8 ≈ 4.70 Vpp

R5≈∞，OPA548 completely disconnected:
TP8 ≈ 4.61 Vpp
```

基本不消失。

所以这个新模型预测：

> **如果真实故障就是pin6高阻，抬掉R5以后100–110 kHz的U4B共振仍然应该存在。**

幅度/波形可能变化，但根本共振不会消失。

这与：

> OPA548是状态改变器，而不是最初振荡发生器

完全一致。

[下载 R5 A/B](sandbox:/mnt/data/pcb_fault_search/pin6_r5_ab.csv)

---

# 12. 我也重新跑了你要求修正的 Stage 6：J4 OPEN

这次严格取消扬声器。

只有：

```text
OPA548 OUTPUT
      │
     4.7Ω
      │
     47nF
      │
     GND

J4 = OPEN
```

105.93 kHz 时：

$$
|Z_{\rm snubber}|\approx32.3\Omega
$$

先重复旧的“大TP8异常”测试。

Cfb=0：

```text
TP8             16.05 Vpp
OPA548 output    7.91 Vpp
J1平均输入功率    0.896 W
OPA548输出Irms    164 mA
```

这里已经完全没有扬声器。

所以原先 Stage 6 的逻辑缺口现在补上了：

> **J4 OPEN并不能阻止100 kHz TP8异常把OPA548推入高电流状态。真实4.7Ω+47nF snubber本身就足够。**

[下载严格J4 OPEN结果](sandbox:/mnt/data/pcb_fault_search/stage6_j4open.csv)

---

# 13. 更重要的是，把“pin6单故障”直接接到J4 OPEN Stage 6，也对上了

这一次不是人为给TP7 0.2 V。

只给：

$$
2mV_{pk}
$$

然后：

```text
pin6 = 1.8 MΩ fault
Cfb = 0
TP8 → ~13.6 Vpp

随后 OPA548 ON
J4 OPEN
仅真实 snubber
```

结果：

```text
TP8                 13.63 Vpp
OPA548 output         7.91 Vpp
J1正轨平均电流量级    108 mA
J1负轨平均电流量级     69 mA
平均输入功率           0.89 W
OPA548 output Irms    163 mA
```

这里最值得看的是：

$$
\boxed{\text{其中一条J1 rail正好约69mA}}
$$

这已经与：

```text
实板：
OPA ON → bench supply ~70mA CC
```

处在同一量级。

而且：

$$
J4=\mathrm{OPEN}
$$

所以现在得到了一条相当完整的构造：

```text
U4 pin6高阻虚焊
        ↓
U4B形成约105kHz极高Q闭环
        ↓
很小的HF扰动被放大
        ↓
TP8出现十几Vpp异常
        ↓
OPA548 OFF输入非线性随J1改变波形
        ↓
OPA ON
        ↓
OPA548输出100kHz大信号
        ↓
4.7Ω + 47nF snubber产生巨大HF电流
        ↓
J1进入~70mA甚至更高电流区域
```

这已经不需要假设第二个功率级故障。

---

# 14. 为什么“高阻虚焊”比“完全没焊”更符合

这一点以后实板测试需要特别注意。

完全开路：

$$
R\rightarrow\infty
$$

不一定落在目标工作模式。

而：

$$
R\sim1\!-\!3M\Omega
$$

恰好和 OPA1656 输入自身的小电容共同形成严重的动态反馈错误。

所以一个：

```text
看起来接着
但实际只有污染/残留物/极差的接触形成MΩ级路径
```

可能比一个完全悬空的腿更危险。

TI提供的 OPA1656 是53 MHz GBW的高速双运放，厂商也专门要求非反相布局中 RF/RG 靠近器件并保持输入走线短；这也说明反相输入节点的实际连接完整性对这种高带宽环路很重要。([Texas Instruments](https://www.ti.com/product/ja-jp/OPA1656?utm_source=chatgpt.com))

对于装配制造，poor wetting、non-wetting、open/partially soldered joint 都是实际存在的缺陷类型，并可能形成差的或间歇性连接。([Indium Corporation](https://www.indium.com/blog/introduction-to-head-in-pillow-and-non-wet-open-defects-in-electronics-assembly/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))

所以从“加工商常见单故障”的角度，我现在会把第一名写成：

$$
\boxed{\text{U4 pin6 non-wet / cracked / marginal solder joint}}
$$

而不是泛泛的“PCB寄生”。

---

# 15. 现在这个模型给出了一个非常强的实板可证伪预测

如果模型正确，断电后：

```text
U4B_N测试点 → GND
≈ 1kΩ

U4B_N测试点 → TP8
≈ 39kΩ
```

依然可能全部正确。

真正异常的是：

```text
U4 pin6 金属腿
       ↓
U4B_N PCB pad / test node
```

正常：

$$
<1\Omega
$$

故障模型：

$$
\boxed{\sim1.6-2.0M\Omega}
$$

相应地：

```text
pin6 metal → GND
```

不再约1 kΩ，而可能进入MΩ量级。

```text
pin6 metal → TP8
```

也不再约39 kΩ，而进入MΩ量级。

因此现在的第一实验甚至比以前更具体：

> **不要先用蜂鸣档。直接使用DMM电阻档，探针一端真正压在OPA1656 pin6裸露金属腿，另一端压在pin6对应PCB焊盘/反馈测试节点。**

而且要轻压、松压各测一次。

如果是裂焊，机械压力可能会让：

```text
1.8M
→ 数百k
→ 几Ω
→ open
```

来回跳。

如果出现这种现象，证据会非常强。

---

# 16. 当前根因排序已经改变

综合这一轮实际 fault injection，我现在会这样排：

| 排名 | 假设 | 当前判断 |
|---:|---|---|
| **1** | **U4 pin6高阻虚焊/非润湿/裂焊** | **非常强；已构造出100–110kHz匹配模型** |
| 2 | U4B内部损伤导致等效输入/补偿异常 | 仍然很高，但目前不需要它就已经可以解释大量现象 |
| 3 | OPA548 OFF输入非线性 | 已证明是参与者/状态改变器 |
| 4 | U4供电/去耦局部异常 | 常规寄生扫描不支持作为第一根因 |
| 5 | R15/R16开路或错值 | 频率行为不匹配 |
| 6 | pin7/pin5虚焊 | SPICE不匹配 |
| 7 | 焊桥 | 多数表现为DC错误/饱和 |
| 8 | 正常探头负载 | 基本否定 |
| 9 | nominal OPA1656+1k/39k本身不稳定 | 已否定 |

所以我会把之前：

> “pin6反馈连接异常是第一嫌疑”

提高一个等级：

> **“pin6并非完全开路，而是MΩ级边缘接触”现在已经是有定量SPICE支持的第一根因模型。**

---

# 17. 这轮仍然没有假装解决的一件事

目前还不能说“100%证明实板就是1.8 MΩ”。

因为 TI SPICE macro 在这个点仍然给：

$$
PM\approx+1^\circ
$$

而不是明确：

$$
PM<0^\circ
$$

因此它非常接近实板，却不是严格的“无任何扰动自动无限起振”复现。

真实器件和 PCBA 不会与 TI nominal macro 完全一致，因此这是非常合理的根因候选，但最终证据必须来自：

$$
\boxed{\text{直接测pin6 metal-to-pad连续性}}
$$

或者重焊 pin6 后：

```text
100–110kHz消失
```

更强的是：

```text
只重焊pin6
不换U4
不改Cfb
→ 异常消失
```

如果发生这一结果，根因闭环程度会远高于“加220 pF以后好了”。

---

几个关键原始结果可以直接查看：

[pin6 接触电阻→100–110 kHz精细映射](sandbox:/mnt/data/pcb_fault_search/pin6_fine_map.csv)  
[pin6接触寄生电容鲁棒性](sandbox:/mnt/data/pcb_fault_search/pin6_contactC_closed.csv)  
[pin6故障 transient / TP7微扰→TP8大幅异常](sandbox:/mnt/data/pcb_fault_search/pin6_resonance_transient.csv)  
[pin6启动振铃与J1影响](sandbox:/mnt/data/pcb_fault_search/pin6_impulse.csv)  
[pin6 × Cfb × J1稳定性扫描](sandbox:/mnt/data/pcb_fault_search/pin6_cfb_j1_ac.csv)  
[R5连接/断开 A/B](sandbox:/mnt/data/pcb_fault_search/pin6_r5_ab.csv)  
[修正后的 J4 OPEN、仅 snubber 的 CC 验证](sandbox:/mnt/data/pcb_fault_search/stage6_j4open.csv)

这轮结果已经足够改变下一步实板排查顺序：**第一优先级不是更换220 pF，也不是先换OPA548，而是直接检查/重焊 U4 pin6 金属腿本身。**如果 pin6 实测确实是 <1 Ω 且机械扰动完全稳定，那么这个最强模型才会被实板证伪，届时第二优先级才应转向“U4B硅片内部损伤”的故障宏模型。

---

# you asked

message time: 2026-08-24 16:44:51

U4PIN6和U4BN是20毫欧，应该没问题。包括完全没上过电的新板。请深入的分析逻辑判断原因

---

# chatgpt response

20 mΩ 这个结果会直接把“pin6 高阻/虚焊”从第一嫌疑里剔除，而且你说**未上电的新板也同样是20 mΩ**，这还同时否定了“上电后损伤才造成反馈脚接触异常”这一支。现在需要重新从“哪些单点故障能让健康拓扑在实板上变成100–110 kHz，而又不破坏直流连通性”来排。

现在要特别区分“DC连通正确”和“AC闭环正确”。20 mΩ只能证明 **pin6↔U4B_N 铜/焊点是好的**；它还没有证明 R15 底端的高频地、R16 实际阻值/器件、U4 供电脚的高频阻抗、以及 U4 本体型号/通道动态是对的。接下来最有价值的是寻找“DC欧姆表全部正常，但100 kHz反馈仍错误”的故障。

还有一个现在必须升到很高优先级的逻辑点：**现有局部 SPICE 把 OPA548 的 E/S 直接硬拉到 PWR_N 来代表 OFF，但实板不是这样。** 实板是 `OPA_ES --R10=100k→PWR_N`，同时还有 TLP185 光耦；项目审计文件也明确写过这条真实 E/S 路径未完整建模。  
而 TI 对 OPA548 明确提醒：器件处于 shutdown 时，**高于20 kHz的信号会增加 leakage**。你的异常恰好是100–110 kHz，而且改变 J1 会改变 TP8 波形。因此我先把“真实E/S关断路径”补进局部 SPICE。

20 mΩ 这个结果很关键。它基本把上一轮最强的“U4 pin6 高阻虚焊/裂焊”模型直接证伪了。尤其你在完全未上电的新板上也测到同样的 20 mΩ，说明至少“U4 pin6 金属脚 → U4B_N PCB 网络”的制造连续性是稳定可靠的，不应该再围绕 pin6 焊点继续浪费时间。

我重新从因果关系、真实 BOM、OPA548 数据手册和新的局部 SPICE 重新推了一遍。结论发生了比较大的变化：

> 现在最值得优先怀疑的，不再是 U4B 本身，而是“我们一直以为 OPA548 处于 OFF，但实板上的 OPA548 很可能根本没有被可靠地 Disable”。

而且这是一个所有板都会共有的系统性硬件问题，不是随机焊接问题。

本轮仍使用你上传并验证的 ngspice 42 环境。

## 一、20 mΩ到底排除了什么，没排除什么

它明确排除了：

$$
U4\ pin6 \rightarrow U4B\_N
$$

之间存在 kΩ/MΩ 级接触不良。

所以我上一轮构造出来的：

$$
R_{\text{pin6-contact}}\approx1.6\sim2M\Omega
$$

虽然数学上很好地重构了 100–110 kHz，但与真实测量不符，应该废弃，不能再作为根因。

但是 20 mΩ只证明：

$$
\boxed{\text{芯片外部金属脚到PCB节点连接正常}}
$$

它没有证明下面这些事情：

$$
R15=1k,\qquad R16=39k
$$

在实物上一定正确；

也没有证明 U4B 内部输入级/补偿网络没有损伤；

更没有证明 OPA548 真正处于 Disable。

而现在最后这一项出现了很强的问题。

---

# 二、我认为现在最重要的新发现：R10=100 kΩ 很可能根本不能把 OPA548 关掉

你的冻结硬件是：

```text
OPA548 E/S
    |
    +---- U7 TLP185 ---- PWR_P
    |
   R10
  100k
    |
  PWR_N
```

项目自己的 BOM 映射明确写了：

- R10 = 100 kΩ；
- OPA_ES → PWR_N；
- 这条 E/S 路径此前实际上没有完整进入 SPICE；
- U7/TLP185 也没有进入原来的主模型。

这很重要，因为之前我们的所谓：

```text
OPA OFF
```

SPICE 实际上是直接把：

```text
E/S = PWR_N
```

硬拉死。

那是一个“理想关断”。

实板根本不是这么关的。

---

## 三、OPA548 数据手册给出的条件非常明确

TI 对 OPA548 的要求是：

真正 Disable：

$$
V_{ES}\le V_-+0.8V
$$

Enable：

$$
V_{ES}\ge V_-+2.4V
$$

或者 E/S 直接开路，也属于 Enable。

更关键的是，E/S 被拉低时，其典型电流为：

$$
I_{ES,L}\approx -70\mu A
$$

TI 还说明：

- disable time ≈ 1 µs；
- enable time ≈ 3 µs；
- 正常工作时 E/S 本身典型就在 $V_-+3.5V$ 左右。([Texas Instruments](https://www.ti.com/lit/ds/symlink/opa548.pdf?ts=1779835629890))

于是看你的 R10：

$$
R10=100k\Omega
$$

仅仅用一个数量级估算：

$$
70\mu A\times100k\Omega=7V
$$

也就是说，100 kΩ 根本不是一个“强下拉”。

如果希望按照这个典型电流把 E/S 保证压在：

$$
V_-+0.8V
$$

附近，那么电阻量级应该是：

$$
R\lesssim\frac{0.8}{70\mu A}
\approx11.4k\Omega
$$

注意：这个 11.4 kΩ 是根据典型电流得到的工程尺度，不是我建议直接拿它作为量产保证值。

但它已经足够说明：

$$
\boxed{100k\Omega\ \text{比应有的下拉强度弱了接近一个数量级}}
$$

---

# 四、我把真实 R10=100k 放回 TI OPA548 原始宏模型，结果非常明确

我没有再把 E/S 硬接 PWR_N。

而是重新建立：

```text
OPA_ES
 |
100k
 |
PWR_N
```

U7 OFF，即光耦晶体管开路。

结果无论 J1 是：

```text
±4
±5
±5.5
±6
±6.5
±7
±8 V
```

OPA548 模型最后都把：

$$
V_{ES}-V_-
$$

拉到了：

$$
\boxed{3.4786V}
$$

左右。

而 TI 的定义是：

$$
\ge2.4V
$$

就是 Enable。

所以按照 TI 自己的宏模型：

> **R10=100k + U7 OFF，并不是 OPA548 OFF，而是 OPA548 ON。**

这是目前整个排查中非常重要的一处模型/硬件基线错误。

我又独立扫了 R10：

| R10 | SPICE得到 $V_{ES}-V_-$ | OPA548状态 |
|---:|---:|---|
| 1 kΩ | 0.070 V | 明确 Disable |
| 2.2 kΩ | 0.153 V | Disable |
| 4.7 kΩ | 0.323 V | Disable |
| 10 kΩ | **0.673 V** | **满足 TI Disable 条件** |
| 22 kΩ | 1.415 V | 未定义区 |
| 33 kΩ | 2.041 V | 未定义区 |
| 47 kΩ | 2.769 V | Enable |
| 68 kΩ | 3.437 V | Enable |
| **100 kΩ** | **3.479 V** | **Enable** |

这个结果相当明确。

所以你以前定义的：

```text
MCU says OPA OFF
```

和真正电气意义上的：

```text
OPA548 output stage disabled
```

很可能不是一回事。

---

# 五、这会重新解释为什么“改变 J1 会改变 TP8”

这是一个非常强的因果线索。

U4B 是 J2 供电：

```text
J2 → ANA_P / ANA_N → U4
```

而 OPA548 是 J1 供电：

```text
J1 → PWR_P / PWR_N → OPA548
```

现在实验现象是：

```text
TP7基本不变
J2不变

但改变J1
    ↓
TP8波形明显改变
```

如果 OPA548 真的彻底 Disable、而且与 TP8 动态隔离，那么：

> J1 从 ±4 V 改到 ±8 V，不应该能够强烈改变一个由 J2 供电的 U4B 输出。

但实际上它改变了。

所以只能说明 J1 域和 TP8 之间存在一个有意义的动态连接。

电路上最明显的就是：

```text
TP8
 ↓
R5 = 100Ω
 ↓
OPA548 +IN
```

以及：

```text
OPA548
 ↓
DRV / snubber / PGND
 ↓
PGND–AGND
 ↓
U4系统
```

因此现在：

$$
\boxed{\text{OPA548支路必须重新上升为核心参与者}}
$$

不是因为“猜 OPA548 坏了”，而是因为 **J1 → TP8 的因果性要求某个 J1 域器件参与**。

---

# 六、但我还不能说“R10=100k就是100 kHz振荡的唯一根因”

这一点必须严格。

我把真实：

```text
R10=100k
OPA548 E/S
J4 OPEN
snubber
R5
OPA1656
```

都重新放进模型以后：

OPA548 确实变成了实际上处于 enabled 的状态。

但是：

$$
TP8
$$

仍没有自己形成 100–110 kHz、十几伏的大振荡。

TP8 只有几十 µV 量级的 HF 成分。

OPA548 输出端模型出现了约：

$$
440\sim460kHz
$$

的小幅 HF 状态，约 0.14 Vpp 左右，而不是实板的 105 kHz。

所以：

> **R10=100k 是一个已经可以确认存在的硬件设计问题，但目前还不能说它单独就是100 kHz发生器。**

更合理的机制现在变成：

$$
\boxed{
\text{OPA548没有真正OFF}
+
\text{真实输入/输出非线性}
+
\text{R5}
+
\text{snubber}
+
\text{实际PDN/地回路}
}
$$

共同形成一个 nominal macro 还没有完整复现的耦合极限环。

这比“U4B天然不稳定”合理得多。

---

# 七、为什么100–110 kHz恰好也值得注意

TLP185 不是一个理想开关。

Toshiba 给出的 TLP185 输出晶体管：

$$
C_{CE}\approx10pF
$$

典型。([东芝半导体存储器](https://toshiba.semicon-storage.com/info/TLP185%28SE_datasheet_en_20191118.pdf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))

而你的结构：

```text
PWR_P
  |
TLP185 Cce
  |
OPA_ES
  |
100k
  |
PWR_N
```

于是非常粗略地有：

$$
\tau=100k\times10pF=1\mu s
$$

对应：

$$
f=\frac{1}{2\pi\tau}
\approx159kHz
$$

与此同时 OPA548：

```text
Disable ≈ 1 µs
Enable  ≈ 3 µs
```

也是 µs 级。([Texas Instruments](https://www.ti.com/lit/ds/symlink/opa548.pdf?ts=1779835629890))

所以 E/S 这个节点本身就不是一个理想数字节点，而是：

> **100 kΩ 高阻节点 + 光耦寄生 + OPA548 内部状态机/模拟电路**

其动态时间尺度和100 kHz处在同一数量级。

而 TI 更直接警告：

> OPA548 shutdown 用于低于 20 kHz 的低频应用；关断器件遇到高于20 kHz的信号时，leakage current 可能增加。([Texas Instruments](https://www.ti.com/lit/ds/symlink/opa548.pdf?ts=1779835629890&utm_source=chatgpt.com))

你的异常：

$$
100\sim110kHz
$$

远高于20 kHz。

所以现在不能再把 Disable 状态的 OPA548 当作：

```text
+IN = 一个普通几pF、无限输入阻抗的负载
```

那是过于理想化的。

---

# 八、还有第二个非常关键的逻辑矛盾：U4B_N 的幅度

这个问题我认为现在必须重新认真看。

你以前测过大致：

```text
TP8 → 接近 ±10V轨的大波形
U4B_N → 约0.9Vpp
```

但是只要：

```text
R15 = 1k
R16 = 39k
pin6 与 U4B_N = 20mΩ
```

那么这是一个非常硬的数学关系：

$$
V_{U4B_N}\approx
V_{TP8}\frac{1k}{39k+1k}
$$

即：

$$
\boxed{V_{U4B_N}\approx0.025V_{TP8}}
$$

假设 TP8 已经几乎从 −9 V 到 +9 V：

$$
V_{TP8}\approx18V_{pp}
$$

那么 U4B_N 应该只有：

$$
18/40=0.45V_{pp}
$$

即使 TP8 真能达到完整：

$$
20V_{pp}
$$

也只有：

$$
0.50V_{pp}
$$

而不是0.9 Vpp。

反过来：

$$
0.9/18=0.05
$$

恰好接近：

$$
1/20
$$

这特别值得注意，因为项目历史上旧模型恰恰曾经使用过：

```text
R16 = 19k
R15 = 1k
```

对应：

$$
\frac1{20}=0.05
$$

项目资料也明确记录过旧19k模型后来才改成真实39k。

我不是说“实板一定装了19k”。

但是：

> **如果0.9 Vpp和约18 Vpp是同时、同一AGND参考、同样探头倍率测出来的，那么它与1k/39k物理上不相容。**

这不是 SPICE 判断，是欧姆定律。

因此现在 R15/R16 **实际阻值**必须重新确认。

20 mΩ只确认了：

```text
pin6 → U4B_N
```

并没有确认：

```text
R15 = 1.000k
R16 = 39.0k
```

---

# 九、这给出了三个可能解释

如果下一次同步测量仍然得到：

$$
U4B_N/TP8\neq1/40
$$

那么只剩三大类原因：

| 可能性 | 含义 |
|---|---|
| R15/R16实际值不对 | 装错值、旧BOM、制造映射错误 |
| AGND在100 kHz显著运动 | 你测到的不是同一个真正参考 |
| U4 pin6存在异常交流输入电流 | U4B内部输入/ESD结构损伤或异常 |

第一项最好查。

第二项需要差分测量。

第三项才指向 U4B 芯片内部损坏。

---

# 十、U4B损坏现在应该放在哪里

20 mΩ并不能排除 U4B 硅片损坏。

因为：

```text
DMM
pin6 metal → pad = 20mΩ
```

测的是：

> 外部引脚与PCB。

它测不到：

- 内部 bond / ESD 网络的动态异常；
- JFET输入级损伤；
- 内部补偿异常；
- B通道输出级损伤。

因此，如果现在正在测试的那块板之前经历过 TP8 被错误接地等事件：

**U4B内部损伤仍然成立。**

但是你补充“未上过电的新板 pin6也是20mΩ”只能证明：

> 新板也不存在 pin6虚焊。

它不能说明新板的 U4B 也已经坏了。

所以这里有一个非常重要的分叉：

如果**全新板第一次安全上电也出现同样100–110 kHz**：

> U4B偶发损伤的概率会大幅下降，系统性设计问题几乎必然上升。

如果只有已经测试过的板振，而新板不振：

> U4B损伤重新升高。

---

# 十一、目前我会这样重新排序根因

| 优先级 | 根因 | 当前判断 |
|---:|---|---|
| **1** | **OPA548实际上没有被可靠Disable：R10=100k过大** | **已经发现明确设计问题** |
| **2** | **OPA548/R5/真实E/S/PGND形成实板耦合HF环路** | **很高；能解释J1改变TP8** |
| **3** | **R15/R16实际比例或AGND参考与假定不一致** | **很高；0.9Vpp比例存在硬矛盾** |
| 4 | U4B内部硅片损坏 | 单板故障时中高；若新板也振则明显降低 |
| 5 | U4供电/AGND-PGND高频耦合 | 可能是耦合环的一部分 |
| 6 | 实际U4型号/错料 | 需要核丝印，但概率较低 |
| 7 | pin5/pin7焊接 | SPICE和现象匹配较弱 |
| **已降级** | pin6虚焊 | **20mΩ实测基本否定** |
| **基本否定** | 正常1k/39k+健康OPA1656天然振荡 | nominal SPICE约62° PM |
| **基本否定** | 正常探头电容 | 220pF都不足以产生该模式 |

而且项目原来的硬件/SPICE映射其实已经写过“OPA548 E/S 路径未建模，需要加入 R10 和光耦验证”，只是此前没有把它提升到根因级别。

---

# 十二、现在最有价值的实验已经不是再测 pin6

下一步我建议按一个非常严格的因果树走，只需要少数实验。

第一刀，也是现在信息增益最高的一刀：

### 实测 OPA548 pin7 E/S

保持：

```text
MCU命令 OPA OFF
J1供电
```

万用表或示波器测：

```text
U1 pin7 E/S
相对于
U1 pin4 PWR_N
```

不要对 PGND 测绝对电压，直接看：

$$
\Delta V_{ES}=V(pin7)-V(pin4)
$$

判据来自 TI：

$$
\Delta V_{ES}\le0.8V
$$

才是真正 Disable；

$$
0.8<\Delta V_{ES}<2.4V
$$

属于未保证区；

$$
\Delta V_{ES}\ge2.4V
$$

就是 Enable。([Texas Instruments](https://www.ti.com/lit/ds/symlink/opa548.pdf?ts=1779835629890))

如果你实际得到：

```text
~3–3.5 V
```

那么会直接证明：

> **过去所有“OPA OFF状态下TP8仍振”的实验，其实都不是OPA548真正OFF。**

这会是整个排查最大的突破。

---

然后第二刀：

### 临时在 R10 上并一个 10 kΩ

这样：

$$
100k\parallel10k\approx9.1k
$$

当 U7 OFF 时，SPICE得到：

$$
V_{ES}-V_-\approx0.67V
$$

已经进入 TI 的明确 Disable 区。

此时暂时**不要测试 OPA ON**。

只保持 OFF，然后观察 TP8。

如果：

```text
原100k：
100–110kHz大幅异常

并10k：
TP8立即稳定
```

那就已经非常接近根因闭环：

$$
\boxed{\text{OPA548过去根本没有真正关断}}
$$

如果仍然振，再进入下一刀。

---

第三刀：

### 真正抬掉 R5

这会比断 J1 更干净。

因为断掉 J1 后，没有供电的 OPA548 输入仍然可能通过内部保护结构加载 TP8。

R5抬脚后则真正得到：

```text
TP8 ─X─ OPA548
```

此时：

如果 TP8 稳定：

$$
\boxed{\text{OPA548支路是必要条件}}
$$

如果 TP8仍原样100–110 kHz：

$$
\boxed{\text{OPA548输入支路基本退出第一根因}}
$$

然后才值得回去集中检查 U4B 本体、R15/R16和PDN。

---

# 十三、同时一定要重新做一次1/40比例实验

两通道同测：

```text
CH1 = TP8
CH2 = U4B_N
两个探头GND都只接TP16/AGND
```

不要分两次截图。

直接看：

$$
\frac{V_{U4B_N,pp}}{V_{TP8,pp}}
$$

健康1k/39k必须非常接近：

$$
\boxed{0.025}
$$

如果测成：

$$
0.045\sim0.055
$$

那么现在不要再讨论 SPICE 稳定性。

先直接断电测：

```text
R15两端 ≈ 1.000k
R16两端 ≈ 39.0k
```

因为这会说明：

> **实际板上的反馈网络和我们用于SPICE的网络根本不是同一个。**

这一项的重要程度仅次于 E/S。

---

# 十四、我目前最倾向的完整因果链

现在最合理的工作假设已经变成：

```text
R10 = 100k 设计过弱
        ↓
所谓 OPA OFF 时
OPA548 实际仍 enabled / 位于非可靠状态
        ↓
TP8通过R5始终与OPA548输入动态连接
        ↓
OPA548功率级 + E/S + 输入保护
+ snubber + PGND/AGND
形成真实板上的HF非线性耦合
        ↓
某个100kHz附近扰动被维持/放大
        ↓
U4B闭环努力纠正
所以TP7仍干净、TP8却大幅异常
        ↓
改变J1
改变OPA548工作区/输入保护/E/S状态
        ↓
规则100kHz → 不规则纹波
        ↓
OPA真正被命令ON时
功率级进一步参与
        ↓
snubber产生大HF电流
        ↓
电源进入约70mA CC
```

其中最前面的：

$$
\boxed{R10=100k不能可靠关断OPA548}
$$

已经有数据手册 + BOM + 厂商宏模型三重证据。

中间的：

$$
\boxed{\text{到底哪个真实寄生把它锁定在100–110kHz}}
$$

目前还没有100%复现。

这就是现在证据边界。

所以我不会把新的假设再说成“已经找到最终根因”。

但是相较于 pin6 虚焊，它已经强很多，因为它既是**真实存在的设计错误**，又能直接解释最关键的实验事实：

> **为什么只改变 J1，J2供电的 TP8 却明显改变。**

现在最应该做的不是换 U4，也不是加220 pF，而是先测一次：

$$
\boxed{V(U1\ pin7)-V(U1\ pin4)}
$$

在“OPA OFF”时到底是多少。

如果你测出来是大约 3～3.5 V，我们的排查方向会立即发生决定性收敛。

---

# you asked

message time: 2026-08-24 17:14:24

是的。你现在这个 `U4 pin6 ↔ U4B_N ≈ 20 mΩ`，而且在完全未上电的新板上也一样，意义非常强：

> **上一轮“pin6 存在 1.6–2.0 MΩ 高阻虚焊”的模型应当直接降级/否定。**

它曾经能够在 SPICE 中拟合 100–110 kHz，但现在有直接实测与它矛盾。不能因为某个故障模型“拟合得漂亮”就继续保留它作为主因。

而这反过来暴露了真正重要的问题：**当前局部 SPICE 并不是 PCB 的一比一电气提取模型。它正确模拟了局部原理图的一部分，但没有真正模拟 PCB 布局。**

我重新直接解析了当前 KiCad PCB 和这次 SPICE deliverable，已经能比较明确地回答你。

---

## 一、这份 SPICE 和 PCB 到底“一致到什么程度”

核心 U4B 小信号部分是对得上的：

```text
PCB                     SPICE
R15 = 1.000 kΩ          1 kΩ        ✓
R16 = 39.0 kΩ           39 kΩ       ✓
R5  = 100 Ω             100 Ω       ✓
U4 = OPA1656            TI宏模型     ✓
U1 = OPA548             TI宏模型     ✓
J2测试 = ±10V           ±10V         ✓
```

所以它很好地回答了：

> “假设这些器件之间都是理想导线、理想电源连接、正常器件，那么这个原理拓扑会不会自己100 kHz自激？”

答案是：

**不会。**

报告得到 `Cfb=0` 时约 `PM=62.3°`，这是相当健康的 nominal 回路。

这个结论我认为仍然成立。

但是：

> **它不能证明PCB没有问题。**

因为它实际上不是 PCB extraction，而是“手工重建的局部等效电路”。

---

# 二、我重新核对后，发现局部 SPICE 和真实 PCB 有几个重要差异

这里有些差异会直接影响我们现在的根因判断。

### 1. SPICE里的U4供电是理想的，PCB不是

局部模型直接：

```text
VANA_P ANA_P 0 +10
VANA_N ANA_N 0 -10
```

意思就是：

> OPA1656电源脚上直接存在一个零阻抗、零电感的±10V电源。

而真实PCB是：

```text
J2
 ↓
ANA_P_EXT / ANA_N_EXT
 ↓
FB1 / FB2
 ↓
ANA_P / ANA_N
 ↓
PCB走线
 ↓
U4 pin8 / pin4
```

而且这些电源还同时供：

```text
U2 AD633
U3 INA149
U4 OPA1656
U8 OPA1656
以及其他模拟器件
```

也就是说，真实的 U4 电源既不是独立，也不是零阻抗。

---

# 三、这里我发现一个相当值得怀疑的PCB布局问题：U4负电源去耦距离非常远

这是我认为目前最值得重新调查的设计级问题之一。

TI 对 OPA1656 的建议非常明确：

> 每个电源脚都应通过低 ESR 的 0.1 µF 陶瓷电容就近旁路到地，反馈电阻也应尽可能靠近反相输入。([Texas Instruments](https://www.ti.com/jp/lit/ds/symlink/opa1656.pdf?utm_source=chatgpt.com "OPA165x 超低ノイズ、低歪み、FET 入力、Burr-Brown™ オーディオ・オペアンプ datasheet (Rev. C)"))

我直接根据 KiCad PCB 铜线计算了 U4 电源脚到实际去耦电容的走线路径。

结果：

```text
U4 ANA_P → C15 100nF
走线约 15.5 mm

U4 ANA_N → C16 100nF
走线约 27.7 mm

U4 ANA_N → C10 100nF
走线约 29.9 mm
```

特别是：

> **负电源 pin4 到最近100 nF旁路的实际铜线接近28～30 mm。**

对于普通低速运放可能还能工作。

但 U4 是：

```text
OPA1656
GBW ≈ 53 MHz
```

而你的 U4B nominal 环路 crossover 仿真又正好是：

```text
≈1.14 MHz
```

此时 20～30 mm 的供电走线已经不能继续当作“0 Ω导线”。

这恰好是当前 SPICE完全没有模拟的东西。

---

# 四、为什么之前的“供电寄生压力测试”没有排除这个问题

这是本次 SPICE 报告里一个容易被误解的地方。

报告说：

> 加入0.1～5 µH供电寄生仍然不振。

看上去好像已经排除了电源完整性问题。

但我重新看了它实际生成的 SPICE：

```text
电源
 ↓
R/L寄生
 ↓
ANA_P
 ↓
100nF + 10uF
直接接地
 ↓
U4
```

也就是说：

> **它把100 nF和10 µF当成直接贴在U4供电节点上的理想本地去耦。**

真实PCB却不是这样。

真实PCB是：

```text
U4 pin4
   │
   │ 很长PCB铜线
   │
   ├────────约28~30 mm──────── C16/C10
   │
ANA_N网络
```

这两者的物理意义完全不同。

换句话说：

**之前的 supply stress 测试实际上把最需要调查的“U4脚到旁路电容之间的寄生”短路掉了。**

因此它不能合理否定这个方向。

---

# 五、而且这个长度对应的寄生频率恰好很敏感

这里可以做一个数量级分析。

PCB走线典型可以按：

```text
约0.5～1 nH/mm
```

估算。

28 mm可能产生：

```text
约15～30 nH
```

数量级的寄生电感。

如果与：

```text
1 µF
```

级旁路共同作用，那么：

[
f\approx\frac{1}{2\pi\sqrt{LC}}
]

对于15～30 nH：

```text
约0.9～1.3 MHz
```

是什么概念？

你的 SPICE 刚刚算出来：

```text
U4B loop crossover ≈1.139 MHz
```

这两个频率竟然在同一数量级。

这就非常值得警惕了。

它不证明根因一定是去耦，但说明：

> **当前PCB的负电源布局正好在U4B的环路交越频率附近可能不再表现成理想电源。**

而 nominal SPICE 把这一部分完全理想化了。

这是比“pin6虚焊”更符合“所有板都可能共有”的设计级问题。

---

# 六、第二个明显的PCB风险：U4B反馈网络没有真正做到局部化

TI明确要求 RF/RG 尽量贴近反相输入。([Texas Instruments](https://www.ti.com/jp/lit/ds/symlink/opa1656.pdf?utm_source=chatgpt.com "OPA165x 超低ノイズ、低歪み、FET 入力、Burr-Brown™ オーディオ・オペアンプ datasheet (Rev. C)"))

PCB中我算出的实际走线：

```text
U4 pin6 → R16
约7.45 mm

U4 pin6 → R15
约9.39 mm

U4 pin7 → R16
约6.94 mm
```

这些还不算特别离谱。

真正的问题是：

**U4B\_N和VCMD不是只连接R15/R16。**

你为了补偿实验放了：

```text
C14
C37
C38
C39
C40
C41
C42
R45
```

大量 DNP 位置。

虽然元件不焊：

> **铜线和焊盘仍然存在。**

我直接统计当前 PCB 的 routed copper：

```text
U4B_N：
约76.9 mm总走线

VCMD：
约115.2 mm总走线
```

其中大量属于去 DNP 补偿位置的支路。

所以真实情况并不是 SPICE 的：

```text
            R16
OUT ───────/\/\/\──── pin6
                     │
                    R15
                     │
                    GND
```

而更接近：

```text
                 ┌── 长stub ── 空焊盘
                 ├── 长stub ── 空焊盘
                 ├── 长stub ── 空焊盘
TP8 ─────────────┼── R16 ── U4B_N
                 │            │
                 │            ├── 长stub
                 │            ├── 长stub
                 │            └── 长stub
                 │
                 └────────── R5 → OPA548
```

这个是典型的：

> **原理图没问题，但PCB改变了高频网络。**

普通SPICE如果没有加这些 parasitic stub，是看不出来的。

---

# 七、第三个差异更加重要：SPICE里的OPA548实际上被大幅简化了

这是我认为必须修正的地方。

局部模型中，OPA548大致是这样：

```text
+IN ← R5 ← TP8

-IN ───────┐
           │
OUT ───────┘
```

也就是把：

```text
-IN
OUT
```

直接接成电压跟随器。

但是PCB实际是：

```text
OPA548 OUT
   ↓
R46 = 0Ω
   ↓
DRV
   ↓
RSH2 = 0.1Ω
   ↓
SPK
   ↓
R6 = 0Ω
   ↓
OPA548 -IN
```

同时还有：

```text
DRV → R12/C4 snubber → PGND
DRV → D1 → PWR_P
PWR_N → D2 → DRV
```

这些在初始局部模型里没有。

因此：

> **OPA548 OFF时，真实 -IN/OUT/+IN 的电位关系与局部SPICE并不完全相同。**

这尤其重要，因为你已经观察到：

```text
OPA OFF:
TP2约有-0.4V附近状态

TP8振荡
```

而局部SPICE给OPA548输出额外放了：

```text
1MΩ → GND
```

这也不是PCB上的真实元件。

所以报告中：

```text
“J1≈6～6.5V以后OPA548输入保护开始加载”
```

可以支持“OPA548参与了”，但具体数值和加载方式不能直接等同实板。

---

# 八、还有一个很明显的不一致：E/S状态没有按你的实板模拟

真实实板现在已经测到：

```text
OPA OFF：
TP9 - TP14 ≈0.55～0.65V
```

但局部 SPICE 的 OFF 是：

```text
OPA548 E/S
直接接 PWR_N
```

也就是：

```text
VES - V- = 0V
```

而不是：

```text
≈0.6V
```

这并不是完全一样的状态。

OPA548官方明确指出：

```text
E/S ≤ V- +0.8V
→ Disable
```

而且特别说明：

> 输出Disable时，对高于约20 kHz的信号，漏电可能增加。([Texas Instruments](https://www.ti.com/jp/lit/ds/symlink/opa548.pdf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\&ts=1779326632349\&utm_source=chatgpt.com "OPA548 高電圧、大電流オペアンプ datasheet (Rev. D)"))

你的异常恰恰是：

```text
≈100～110 kHz
```

所以这里非常值得重新建立模型：

```text
E/S = V- + 0.55
      ↓
      +0.60
      ↓
      +0.65V
```

而不是直接：

```text
E/S = V-
```

这可能不是振荡第一来源，但当前SPICE并没有真实复现你的关断工作点。

---

# 九、还有一个明确的数值不一致：OPA548限流电阻

当前 PCB/BOM：

```text
R7 = 57.6 kΩ    已贴
R8 = 33.2 kΩ    DNP
R9 = 22.1 kΩ    DNP
```

而这次局部 SPICE：

```text
RCL = 33.2 kΩ
```

也就是模拟用的是本应 DNP 的值。

这不会解释 OPA OFF 时 TP8 为什么100 kHz，但它意味着：

> **OPA ON后的CC仿真不能认为与真实PCB严格等效。**

所以这一项必须改。

---

# 十、TP7在SPICE中也过于理想

局部模型直接使用：

```text
VTP7 = ideal voltage source
```

实际却是：

```text
AD633 OUT
   ↓
PCB走线
   ↓
U4 pin5
```

而且 MUL\_RAW 在PCB中总走线约：

```text
44.7 mm
```

TP7测试点又是在另一条支路上。

因此：

```text
“TP7测试点看起来干净”
```

与：

```text
“U4 pin5在几十MHz范围绝对干净”
```

不是完全同一个结论。

对于100 kHz基波差别不大。

但是对于一个高速运放局部稳定性问题，真正应该观察：

```text
U4 pin5
```

而不只是远端TP7。

SPICE里的理想电压源相当于把TP7节点阻抗强制为：

```text
0 Ω
```

这会人为吸收任何从U4输入耦回来的高频能量。

真实 AD633 输出不是0 Ω。

所以这也是一个潜在“SPICE把系统稳定化”的地方。

---

# 十一、还有一个遗漏：U4A完全没有参与局部SPICE

真实 U4 是：

```text
一个双运放封装

U4A
+
U4B
```

它们：

```text
共用 ANA_P
共用 ANA_N
共用硅片
```

而局部SPICE只实例化了一只独立OPA1656模型：

```text
U4B
```

没有：

```text
U4A
```

真实U4A本身增益也很高。

所以：

```text
U4A输出电流
↓
共同电源阻抗
↓
U4B
```

这条可能的交叉耦合路径也被局部模型删除了。

即使 TP5 看起来正常，也建议下一版把：

```text
U4A + U4B
```

同时放进去。

---

# 十二、所以现在PCB问题的概率排序，我会重新改成这样

你测得pin6只有20 mΩ以后，我不会再把焊接虚接放第一。

目前我的排序是：

| 优先级问题当前判断 | | |
| --- | --- | --- |
| **1** | **U4供电去耦布局/供电阻抗，特别是ANA\_N** | **很值得怀疑；现有SPICE没有真实模拟** |
| **2** | **U4B反馈/VCMD超长DNP stub与寄生耦合** | **PCB级明显风险** |
| **3** | **OPA548真实Disable状态 + R5接口 + 实际反馈路径** | **确定参与，当前SPICE简化过度** |
| **4** | U4A/U4B共电源、双通道耦合 | 局部模型遗漏 |
| **5** | AD633真实输出阻抗/TP7局部高频污染 | 目前没有充分排除 |
| **6** | AGND/PGND返回路径和两层PCB地阻抗 | 需要PCB寄生模型 |
| **7** | U4芯片损坏 | 如果多块新板也同样振，概率明显下降 |
| 很低 | pin6 MΩ虚焊 | **20mΩ实测已经基本否定** |
| 很低 | OPA1656+1k/39k原理拓扑天然不稳定 | nominal SPICE已经否定 |

其中第一和第二项有一个共同特点：

> **如果所有PCB都采用同一个layout，它们会在所有板上重复出现。**

这正好符合你现在开始怀疑“是不是PCB设计本身”的方向。

---

# 十三、所以，这份SPICE应该怎样升级，才能真正检查PCB

下一版不要再叫：

```text
U4B局部SPICE
```

应该改成：

> **PCB-faithful U4/OPA548 parasitic model**

至少加入下面这些真实因素：

```text
J2
↓
FB1 / FB2真实模型
↓
PCB supply trace R+L
↓
U4 pin8 / pin4

U4 pin8 → C15
加入15.5mm走线寄生

U4 pin4 → C16/C10
加入28~30mm走线寄生

同时放入：
U4A
U4B
U2 AD633输出模型

反馈网络：
R15/R16实际位置
VCMD/U4B_N DNP stub寄生C/L

OPA548：
R5=100
R6=0
R46=0
RSH2=0.1
R12=4.7
C4=47n
D1/D2
R7=57.6k

E/S：
V- + 0.55~0.65V sweep

J4：
OPEN
```

然后做：

```text
power ramp
而不是一开始就给理想±10V

J2先上/J1后上
J1先上/J2后上
同时上电
```

这一点也非常重要。

真实板子的上电瞬态，而不是SPICE“时间0已经稳定在±10V”，有可能把系统推入某个非线性极限环。

---

# 十四、现在我认为最值得马上做的一个实板A/B实验

不是继续测pin6。

而是直接针对目前最明显的PCB弱点：

> **给U4本体做真正的本地去耦。**

保持原板不拆件，临时飞焊：

```text
U4 pin8 ANA_P
→ 100 nF
→ 最近AGND

U4 pin4 ANA_N
→ 100 nF
→ 最近AGND
```

线一定非常短。

最好：

```text
电容就在U4腿旁
引线几毫米以内
```

尤其优先：

```text
pin4 ANA_N
```

因为PCB现有负电源100nF实际要走约28～30mm。

然后完全不改：

```text
R15
R16
R5
Cfb
```

保持：

```text
Cfb = DNP
OPA OFF
```

重新看 TP8。

这个A/B的判别力极高。

如果：

```text
飞本地100nF前：
TP8 100~110kHz

飞本地100nF后：
明显降低/消失
```

那根因就会非常集中：

> **U4电源完整性/去耦布局问题。**

如果完全不变：

再进入：

```text
反馈长stub
OPA548输入
AD633/U4A耦合
```

方向。

---

## 最核心的判断

所以现在我的答案是：

**这次SPICE和PCB在“原理图核心参数”上基本一致，但远远不能称为“和PCB完全一致”。**

它已经非常可靠地告诉我们：

> **健康OPA1656 + 1k/39k本身不会100 kHz自激。**

但它**没有合理排除PCB级问题**，因为它忽略了真实走线、去耦位置、地回路、双通道共享电源、AD633输出阻抗、OPA548真实反馈/E/S状态，以及多个DNP补偿支路的铜线寄生。

而我现在直接检查当前PCB后，最值得关注的设计事实是：

> **U4负电源的100 nF去耦实际铜线路径约28～30 mm，而U4B自身环路交越频率约1.14 MHz；同时U4B\_N和VCMD还带有很长的DNP补偿支路。**

这两项在当前局部SPICE中都被理想化掉了。

因此下一步我不会继续追“pin6虚焊”，而会优先追**PCB电源完整性和局部布局寄生**。如果你要继续用 SPICE 定位，应该直接把当前 KiCad 几何转换成上述 PCB-aware 寄生模型，而不是再做单一元件 fault injection。
\*\*\*

基于以上PCB分析重新做审查，并给出修改后的SPICE模型和审查结果。

---

# chatgpt response

我会按“PCB几何/网络→寄生等效→局部模型→A/B仿真→修改建议”重新做，不沿用上一版把供电/去耦理想化的假设。重点会验证你指出的四个缺口：U4供电走线、DNP stub、真实 OPA548 反馈/E/S、以及 U4A/AD633 共电源耦合。

---

# you asked

message time: 2026-08-24 17:20:55

我补充了一个你可能需要的资料，当前环境你没有KICAD，但是需要KICAD的地方我都可以做。你核心是完成真实模型的修正。

---

# chatgpt response

这份补充资料足够了：它包含可直接解析的 `project.kicad_pcb/.sch`、校正后的 BOM 和审计数据，所以即使没有 KiCad GUI，我也能做电气几何提取。接下来我会把“理想导线”替换为从 PCB 路由长度、层、过孔和焊盘推导出的 R/L/C 近似网络，并把真实 OPA548 功率回路和 E/S 状态一起放回。

我已经从 PCB 文本直接复核了你给出的关键几何：U4 pin8→C15 是 **15.51 mm**；pin4→C16 是 **27.71 mm**；pin4→C10 是 **29.90 mm**；pin6→R16 是 **7.45 mm**；pin7→R16 是 **6.94 mm**；MUL_RAW 总布线约 **44.65 mm**；VCMD/U4B_N 总布线分别约 **115.2/76.9 mm**。这些数值与你的人工 KiCad 解析一致，可以作为模型修正的几何基准。

有一个重要的模型修正我会单独区分：PCB 上的补偿电容并不都等效于“直接并在 R16 上”。例如 C37–C41 距 U4 两端实际路由约 32–44 mm；C14 也在另一处。因此新模型会同时比较“R16本地补偿”和“远端DNP焊盘补偿”，不能再把它们视为同一个 Cfb。

这份 KiCad 补充资料已经足够让我把模型从“局部原理图 SPICE”推进到“PCB-aware 模型”。我已经直接解析了 `.kicad_pcb/.kicad_sch` 和校正 BOM，不需要 KiCad GUI 才能继续核心工作。

目前得到的结论比上一轮更收敛。

第一，PCB 几何已经实际进入模型，而不是只做数量级估算。我提取并使用了这些关键路径：

| 路径 | PCB实际路由长度 |
|---|---:|
| U4 pin8 → C15 100 nF | 15.51 mm |
| U4 pin4 → C16 100 nF | 27.71 mm |
| U4 pin4 → C10 100 nF | 29.90 mm |
| U4 pin4 → C12 1 µF | 32.03 mm |
| U4 pin6 → R16 | 7.45 mm |
| U4 pin6 → R15 | 9.39 mm |
| U4 pin7 → R16 | 6.94 mm |
| U2 AD633 W → U4 pin5 | 8.53 mm |
| U4 pin7 → R5 | 58.76 mm |
| U4 pin7 → TP8 | 76.44 mm |
| U4 pin7 → C41 | 25.84 mm |
| U4 pin6 → C41 | 30.85 mm |

整网 routed copper 则约为：

```text
MUL_RAW   44.65 mm
VCMD      115.20 mm
U4B_N      76.90 mm
ANA_P     146.51 mm
ANA_N     171.99 mm
```

因此新的模型已经不再把这些网络当成理想导线。

---

## PCB-aware AC 的结果很重要

我把以下因素同时加入：

- PCB实际 ANA_P/ANA_N 分布 R/L；
- 去耦电容放在真实的远端位置；
- FB1/FB2；
- U4A + U4B 两个 OPA1656 通道；
- AD633 厂商宏模型；
- MUL_RAW、VCMD、U4B_N 分布寄生；
- DNP 补偿焊盘/支路寄生；
- OPA548真实 R5/R6/R46/RSH2 反馈结构；
- J4 OPEN；
- 4.7 Ω + 47 nF snubber；
- R7修正为真实的57.6 kΩ；
- SS56B钳位；
- 实测的 OPA548 OFF `E/S≈V−+0.55～0.65 V`；
- AGND/PGND 分开后经 R3=0 Ω连接。

中央估计得到：

$$
f_c=1.1363\text{ MHz}
$$

$$
PM=63.79^\circ
$$

也就是说，从原来理想模型的：

$$
PM\approx62.3^\circ
$$

变成真实一阶 PCB 提取后：

$$
PM\approx63.8^\circ
$$

没有恶化。

寄生范围扫描：

```text
较低PCB寄生： PM ≈ 62.55°
中央估计：     PM ≈ 63.79°
较高PCB寄生： PM ≈ 73.84°
```

都没有接近100 kHz自激。

因此现在可以明确修正上一版判断：

> **U4去耦距离28–30 mm虽然布局并不理想，但仅靠这一点不足以解释100–110 kHz。**

同样：

> **VCMD/U4B_N 的 DNP长stub确实应该纳入模型，但在合理PCB寄生范围内，它也不足以单独产生当前异常。**

这两个方向的根因优先级都应该下降。

[PCB-aware loop结果](sandbox:/mnt/data/pcb_faithful_model/loop_v2_results.csv)

---

## “飞100 nF到U4脚旁”在SPICE里的结果

这个实验我也先在 PCB 提取模型里做了。

原PCB：

$$
PM=63.7882^\circ
$$

再直接在 U4 pin8/pin4 附近增加理想本地100 nF：

$$
PM=63.7881^\circ
$$

几乎没有区别。

这并不代表实板A/B没有测试价值——实际飞电容还能改变未建模的地回流和器件局部供电。

但模型已经告诉我们：

> 如果飞100 nF以后实板100 kHz完全消失，那么原因不会只是我们目前估算的“28 mm走线≈几十nH”这么简单，而意味着实际板上还有模型缺失的PDN/回流耦合。

---

## PGND/AGND 也做了独立扫描

我把以前的统一0 V拆成：

```text
AGND
 ↓
R3 = 0Ω + parasitic L
 ↓
PGND
```

并把等效连接电感从：

$$
0.1nH
$$

一直扫到非常夸张的：

$$
1000nH
$$

小信号 U4B PM 基本仍保持：

$$
63.788^\circ
$$

所以：

> **单纯R3/AGND-PGND连接电感也不是小信号100 kHz自激根因。**

但这一结论只针对 OPA OFF、小信号。

OPA548发生100 kHz大电流以后，ground bounce 仍然可能成为“症状放大器”。

[AGND/PGND扫描](sandbox:/mnt/data/pcb_faithful_model/ground_loop_results.csv)

---

# 另一个重要修正：AD633不能再用理想TP7源

这个是你的 PCB 审查指出的正确问题。

我独立用 AD633 厂商宏模型测了其输出阻抗。

100 kHz：

$$
Z_{out}\approx0.282+j4.301\Omega
$$

110 kHz：

$$
Z_{out}\approx0.338+j4.728\Omega
$$

所以旧模型：

```text
VTP7 = ideal voltage source
Zout = 0
```

确实不够真实。

新的完整 AC 模型已经直接使用 AD633 宏模型；reduced transient 模型则使用这个测得的频率相关源阻抗作为等效。

这一修正以后不会再退回去。

---

# 但又发现了一个比PCB寄生更严重的模型问题：OPA548厂商宏模型的OFF状态不可信

这是现在非常关键的一点。

实板已经测得：

$$
V_{ES}-V_-\approx0.55\sim0.65V
$$

根据 TI：

$$
V_{ES}\le V_-+0.8V
$$

属于明确 Disable。

所以我没有继续沿用之前“R10=100k导致OPA没有真正OFF”的推断；**实测优先，这个推断应该撤回。**

问题转移到了模型本身。

我用 TI OPA548 官方宏模型设置：

$$
E/S=V_-+0.6V
$$

跑 transient。

它给出了：

```text
OPA548 output ≈ -4.64 V
J1正轨 ≈ 57 mA
J1负轨 ≈ 57 mA
```

即使没有任何输入异常。

但 TI 数据手册规定 shutdown quiescent current 的典型值只有约：

$$
6mA
$$

而 disabled output 的典型 leakage 是几mA级，且器件是高阻关断行为。TI还明确说明，关断器件遇到高于20 kHz的信号时，leakage可能增加。([Texas Instruments](https://www.ti.com/jp/lit/ds/symlink/opa548.pdf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))

因此现在可以明确：

> **OPA548官方宏模型适合 ON 状态闭环/功率级分析，但不能把它的 Disable transient行为当作实物真值。**

这也是为什么之前很多：

```text
J1变化
OPA548 OFF输入加载
TP8影响
```

仿真的具体电流和门限只能作为趋势，不能作为实物定量结果。

---

# 所以真实模型现在拆成两种 OPA548 状态

这是我认为正确的最终建模架构。

### OPA ON

使用：

```text
TI OPA548 vendor macro
```

并保留真实：

```text
R5 = 100Ω
R6 = 0Ω
R46 = 0Ω
RSH2 = 0.1Ω
R7 = 57.6k
R12 = 4.7Ω
C4 = 47nF
D1/D2 = SS56B
J4 = OPEN / speaker两种状态
```

### OPA OFF

不再直接相信 TI 宏模型的大信号关断输出。

改用 datasheet-constrained surrogate：

```text
Differential input:
10 MΩ || 6 pF

Common-mode input:
1 GΩ || 4 pF

E/S:
实测 V− + 0.55～0.65 V

Output:
高阻 disabled model
+
datasheet leakage约束

输入到±J1 rail：
保护钳位敏感度模型
```

TI 对输入阻抗给出的数据正是：

$$
10^7\Omega\parallel6pF
$$

和：

$$
10^9\Omega\parallel4pF
$$

。([Texas Instruments](https://www.ti.com/jp/lit/ds/symlink/opa548.pdf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))

这样才不会让厂商宏模型错误的 shutdown output 状态污染 U4B 根因分析。

---

# SS56B也已经修正

PCB/BOM实际是：

```text
SS56B
60 V / 5 A Schottky
```

不是以前抽象的小二极管。

该系列公开资料给出的典型结电容约：

$$
C_j\approx300\sim320pF
$$

@1 MHz、4 V反偏量级。([YIC Electronics](https://www.yic-electronics.com/pdf/SS56B.html?utm_source=chatgpt.com))

所以新模型中央值使用：

$$
320pF
$$

并做150–700 pF敏感度扫描。

这也是一个以前遗漏的、比较大的功率节点寄生。

---

# OFF surrogate transient结果

我已经开始用这套新的 OFF 模型做大信号 transient。

把：

- PCB供电寄生；
- U4A；
- U4B；
- AD633约束输出阻抗；
- DNP stub；
- R5；
- OPA548 datasheet input impedance；
- 真实反馈；
- J4 OPEN；
- snubber；
- SS56B约320 pF；
- AGND/PGND；

全部保留后：

正常状态仍然不振。

甚至把 PCB RLC 寄生人为扩大到2–3倍：

```text
trace L ×3
trace C ×3
SS56 Cj → 1000pF级
AGND/PGND L → 200nH
J1外部线电感 → 2µH
```

也没有自己产生100–110 kHz。

这又排除了一个相当大的区域：

> **正常关断OPA548的被动寄生 + 一阶PCB寄生，不足以产生当前100 kHz。**

---

## TP7小HF扰动测试

比如在 TP7加入：

$$
1mV_{pk},\ 105kHz
$$

PCB-aware transient得到：

$$
TP8\approx80.14mV_{pp}
$$

正好就是：

$$
2mV_{pp}\times40\approx80mV_{pp}
$$

而 J1：

```text
±4V
±5V
±6V
±7V
±8V
```

几乎不改变结果。

5 mVpk：

$$
TP8\approx400.7mV_{pp}
$$

仍然只是正常40倍。

所以正常 OFF input impedance 也不能解释：

```text
几mV TP7 HF
→ 十几V TP8
```

这和之前那个已经被20mΩ否定的pin6故障模型完全不同。

---

# 但是PCB-aware模型发现了一条以前没有量化的100 kHz路径

我又专门做了：

$$
ANA_P/N\ supply\ ripple\rightarrow TP8
$$

传递函数。

结果比较意外。

如果给 J2 正轨一个1 V小信号扰动：

100 kHz：

$$
|TP8/V_{ANA+}|\approx2.21
$$

110 kHz：

$$
\approx2.48
$$

负轨：

100 kHz：

$$
\approx2.12
$$

110 kHz：

$$
\approx2.39
$$

原因主要不是 U4B 自己的 PSRR。

而是：

```text
ANA rail ripple
       ↓
AD633
       ↓
MUL_RAW
       ↓
U4B ×40
       ↓
TP8
```

在100 kHz，完整模型中：

$$
1V\ supply\ ripple
\rightarrow
约55mV\ TP7
\rightarrow
约2.2V\ TP8
$$

如果把 AD633 输出替换为真正的理想零阻抗干净 TP7：

正轨100 kHz：

$$
TP8/V_{rail}\approx0.0061
$$

负轨100 kHz：

$$
\approx0.093
$$

立即下降很多。

所以：

> **如果真实 ANA_P/ANA_N 本身存在100–110 kHz纹波，AD633是一个很有效的 supply-ripple→TP8 路径。**

[供电纹波完整传递](sandbox:/mnt/data/pcb_faithful_model/supply_transfer.csv)

[固定干净TP7后的供电传递](sandbox:/mnt/data/pcb_faithful_model/supply_transfer_tp7clamp.csv)

---

# 但这还不是最终根因

为了把 TP8 推到比如：

$$
15V_{pp}
$$

单纯按：

$$
2.2V/V
$$

需要好几伏的 ANA rail 纹波。

这对于正常 ±10 V J2 不合理。

所以：

> J2普通几十mV开关纹波不能单独解释接近轨的TP8异常。

但这个结果给下一步实测增加了一个很重要的节点：

```text
U4 pin8 ANA_P
U4 pin4 ANA_N
```

必须看100–110 kHz。

如果这里有非常大的局部振铃，那意义会完全不同。

---

# 当前模型审查后的根因排序

经过这次真正的 PCB-aware 模型，我会重新排成：

| 优先级 | 假设 | 新判断 |
|---:|---|---|
| 1 | **OPA548 OFF状态存在数据手册未充分定义、宏模型也不能可靠模拟的 >20 kHz非线性行为** | 仍很高，尤其因为实物波形依赖J1 |
| 2 | **U4B器件本体异常/损伤** | 如果只有已测试板异常，仍然很高 |
| 3 | **100–110 kHz实际是外部/电源域驱动，而不是U4B自主振荡** | 比以前明显升高 |
| 4 | AD633/ANA rail HF耦合 | 已证明存在明显传递路径 |
| 5 | OPA548→PGND→AGND大信号耦合 | 可能参与极限环，但小信号不是根因 |
| 6 | PCB反馈/DNP stub | 已加入模型，单独不足以致振 |
| 7 | U4本地去耦距离 | 设计可以改善，但单独不足以解释100k |
| 很低 | pin6高阻焊接 | **20mΩ直接否定** |
| 很低 | 正常OPA548 OFF几pF输入负载 | 新 surrogate SPICE否定 |
| 很低 | nominal OPA1656+39k/1k天然不稳 | full PCB-aware仍≈64° PM |

其中有一个条件非常重要：

如果**全新、从未经历错误测量/CC的新板第一次上电也出现完全相同100–110 kHz**，那么：

> U4B单颗损坏会大幅下降，系统性 OPA548-off/电源驱动/布局架构会上升。

反之，如果新板正常：

> U4B损伤会重新成为第一候选。

---

## 关于你能帮我做的 KiCad 工作

目前暂时不需要你替我操作 KiCad。核心拓扑和路由长度已经能从文本项目中提取。

真正可以进一步提高寄生精度的只有几项，后面需要时再取：

- PCB实际板厚；
- 铜厚，当前暂按35 µm；
- F.Cu–B.Cu介质厚度；
- 材料 εr；
- 实验时220 pF到底焊在 R16本地，还是 C14/C37–C41 中哪个位置。

这些影响的是 R/L/C 定量精度，但根据目前敏感度扫描，**不会把64°突然变成100 kHz自激**，所以它们不是当前阻塞项。

当前最重要的模型结论可以压缩成一句：

> **第一阶真实PCB寄生已经加入以后，健康U4B仍稳定；因此继续单纯增加走线L/C已经不再是高价值方向。真正没有被可靠建模、同时又与J1强相关的核心，只剩OPA548关断态的高频非线性/实际器件行为，以及可能的外部100–110 kHz激励。**

下一轮应该围绕这两个变量继续，而不是再调PCB寄生参数。

---

# you asked

message time: 2026-08-24 17:58:54

给出一个加入板子非理想因素版本的SPICE

---

# chatgpt response

可以。我会直接给你一个可运行的 PCB-aware SPICE 版本，不只写思路：保留 U4A/U4B、AD633、真实 OPA548 功率回路与 J4 OPEN/snubber，并把 U4供电走线、远端去耦、MUL_RAW/VCMD/U4B_N 路由、DNP焊盘寄生、AGND/PGND连接、实测 E/S≈V−+0.6 V 等非理想因素参数化。

我会给你两个层级，避免“真实”与“可读/可调”混在一起：主文件是一个可读的 reduced-order PCB-aware 模型，适合继续做 transient/root-cause；同时附一个从 PCB 分段铜线直接提取的 full-extracted loop 版本，用来复核 reduced 模型没有把关键寄生简化错。两者都改成相对路径并随包附上所需厂商模型。

模型文件已经生成。现在我在做最后一步验证：实际用 ngspice 跑一遍 reduced 版的 loop + transient，再跑 full-extracted loop，对比相位裕量和是否出现意外收敛/节点定义问题。只有两者都能稳定运行，我才把文件给你。

已经给出一个“加入板子非理想因素”的可运行 SPICE 版本，并且实际用 ngspice 42 验证通过。

主文件是这个：

[PCB-aware U4B / OPA548 OFF reduced SPICE](sandbox:/mnt/data/PCB_AWARE_SPICE_v1/PCB_AWARE_U4B_OFF_reduced.cir)

它不是以前的理想局部模型，而是已经加入：

- J2→FB1/FB2→U4 的供电 R/L；
- U4 pin8→C15 15.5 mm 实际去耦路径；
- U4 pin4→C16/C10/C12 约 27.7–32.0 mm 实际去耦路径；
- U4A 与 U4B 共用同一非理想电源；
- AD633 厂商宏模型，不再把 TP7 当成 0 Ω 理想源；
- MUL_RAW 8.525 mm 实际路线 R/L/C；
- U4B pin7→R16、pin6→R16、pin6→R15 的实际反馈路径寄生；
- VCMD/U4B_N 的 DNP 空焊盘和长 stub 寄生；
- TP8 10×探头负载；
- U4 pin7→R5 约58.76 mm VCMD路线；
- AGND / PGND 分开，并加入 R3/走线等效 R/L；
- J1电源引线电感、470 µF电容；
- R5=100 Ω；
- R6/R46；
- RSH2=0.1 Ω；
- 4.7 Ω + 47 nF snubber；
- J4 OPEN；
- SS56B 约320 pF级结电容；
- OPA548 OFF 使用 datasheet-constrained surrogate，而不是错误地相信厂商宏模型的 shutdown transient。

里面顶部几个参数可以直接改：

```spice
.param J1=5
.param J2=10

.param HFAMP=0
.param HFREQ=105k

.param CFB=1a

.param RGND=5m
.param LGND=2n

.param LJ1=0.2u
.param CDIODE=320p
```

例如测试100 pF：

```spice
.param CFB=100p
```

测试 TP7 是否只需1 mV的105 kHz污染就能激起异常：

```spice
.param HFAMP=1m
.param HFREQ=105k
```

其中：

```spice
CFB=1a
```

实际上就是把 Cfb 当作 DNP。

我还给了一个更详细的“铜线逐段提取版”：

[PCB full-extracted loop SPICE](sandbox:/mnt/data/PCB_AWARE_SPICE_v1/PCB_AWARE_full_extracted_loop.cir)

这个版本不是把28 mm线路简化成一个电感，而是保留了 PCB extraction 得到的大量：

```text
trace segment R
trace segment L
distributed C
pad node
branch
```

它主要用于验证 reduced-order 模型有没有把 PCB 简化错。

两个模型实际对比：

| 模型 | U4B loop crossover | Phase Margin |
|---|---:|---:|
| reduced PCB-aware | 1.13541 MHz | 63.52° |
| full copper extraction | 1.13633 MHz | 63.79° |

差异只有：

$$
\Delta f_c\approx-0.08\%
$$

以及：

$$
\Delta PM\approx-0.26^\circ
$$

所以 reduced 版非常适合后续继续做大规模 fault injection 和 transient，而不需要每次都跑几百个铜线节点。

更重要的是，这个版本在：

```text
Cfb = DNP
OPA OFF
J1 = ±5 V
J2 = ±10 V
J4 = OPEN
```

下跑3 ms transient 后：

$$
TP8_{\rm tail,Vpp}\approx1.9\times10^{-7}V
$$

也就是仍然没有100–110 kHz持续振荡。

这意味着现在这个结论比原局部模型强很多：

> **不只是理想原理图稳定；加入目前从PCB中能够合理提取的一阶走线、远端去耦、DNP stub、地回路、AD633输出阻抗以及正常OPA548 OFF被动负载以后，健康U4B仍然稳定。**

因此如果实板仍然振，剩下的搜索对象就更应该集中在：

1. 某个实际器件的大信号/关断态行为没有被厂商模型覆盖；
2. 真实板存在模型中尚未取得的局部电源/地大幅100 kHz波形；
3. 某个元件实际值/安装状态与 KiCad/BOM 不同；
4. U4B或其他器件本体异常；
5. OPA548在>20 kHz shutdown状态下的非线性行为。

完整便携包也整理好了，包含两份 SPICE、OPA1656/AD633/OPA548模型、运行脚本和验证结果：

[下载 PCB_AWARE_SPICE_v1 完整包](sandbox:/mnt/data/PCB_AWARE_SPICE_v1.zip)

[验证结果 CSV](sandbox:/mnt/data/PCB_AWARE_SPICE_v1/validation_summary.csv)

下一步最适合直接在这个版本上继续做的，不是再泛扫线路电感，而是建立“**实板可疑器件状态 fault matrix**”，例如分别把 OPA548 OFF 高频非线性、U4B损伤等效、R15/R16错值、局部去耦开路/错料、AD633供电纹波耦合逐个注入，看哪一个能够第一次真正生成100–110 kHz持续大幅振荡。

---

# you asked

message time: 2026-08-24 18:10:58

这版 `PCB_AWARE_SPICE_v1` 已经把问题推进了一层：**健康的原理图 + 当前已提取的一阶 PCB 非理想因素，仍然无法产生实板的 100–110 kHz。** 因此后续不应该继续泛扫“走线电感是多少”，而应该寻找**模型仍没有表达、但真实 PCBA 一定存在的机制**。

这里最重要的不是再加更多寄生，而是重新定义 fault matrix 的优先级。

### 一、这版 SPICE 已经排除了什么

目前 reduced 与 full copper extraction 的结果几乎一致：

```text
reduced： fc ≈ 1.135 MHz，PM ≈ 63.52°
full：    fc ≈ 1.136 MHz，PM ≈ 63.79°
```

而且 Cfb=DNP、J1=±5 V、J2=±10 V、OPA OFF、J4 OPEN 时，3 ms 后 TP8 只有约 `1.9×10⁻⁷ Vpp`。这意味着下列解释已经明显降级：

```text
正常 OPA1656 + 1k/39k 本身不稳定        ×
目前建模的 VCMD/U4B_N 长走线寄生         ×
目前建模的远端去耦路径                   ×
正常 10×探头负载                        ×
正常 AD633 输出阻抗                     ×
目前的一阶 AGND/PGND 寄生                ×
正常 OPA548 OFF 被动输入负载             ×
```

因此，真实板与模型之间还缺的是\*\*“状态错误”或“耦合机制”，而不是简单增加几 nH 就能解决的问题。\*\*

---

## 二、我认为现在第一优先级已经不是 U4B 损坏，而是“PCB互耦没有被提取”

这是当前模型一个非常重要的盲区。

你现在的 extraction 主要表达了：

```text
每条走线自己的：
R
L
对参考地 C
```

但没有看到真正意义上的：

```text
Net A ↔ Net B mutual capacitance
Net A ↔ Net B mutual inductance
```

这是关键区别。

例如真实 PCB 上：

```text
VCMD / TP8
```

总铜线约115 mm，而且是一个：

```text
增益约40倍的高速运放输出
```

如果其中一部分与：

```text
MUL_RAW / U4 pin5 (+IN)
```

平行、邻近，就会形成：

```text
                 Cpar
TP8 ─────────────||────────── U4B +IN
 ↑                                │
 └──────── OPA1656 ×40 ───────────┘
```

这不是负反馈。

这是**高频正反馈**。

而你当前模型里的：

```spice
CMULTA MUL0 AGND ...
CMULTB U4P AGND ...

CSTUBV U4O AGND ...
```

都是“到地电容”。

它们无法模拟：

```text
U4O → U4P
```

直接的互电容。

这是目前我认为最值得跑的第一项 fault injection。

建议直接增加：

```spice
.param C_VCMD_TO_PLUS=0

CXP U4O U4P {C_VCMD_TO_PLUS}
```

扫描：

```text
0
0.02 pF
0.05 pF
0.1 pF
0.2 pF
0.5 pF
1 pF
2 pF
5 pF
```

不仅要看：

```text
会不会振
```

还要记录：

```text
振荡频率是否进入100~110kHz
PM
TP8 Vpp
```

如果例如：

```text
0.2~1pF
```

就能把系统推到105 kHz附近，那么这会成为一个非常强的**PCB设计级根因**。

因为这种问题：

```text
每块相同PCB
→ 都可能重复
```

而普通“每条线到地”的 extraction 完全看不到。

---

# 三、第二优先级：AGND目前仍然过于理想

当前模型虽然分开了：

```text
AGND
PGND
```

并且加了：

```text
RGND
LGND
```

但整个模拟区域里的：

```text
R15 ground
AD633 ground
U4 decoupling ground
J2 return
```

本质上仍共用一个理想：

```text
AGND node
```

真实 PCB 不可能如此。

尤其 U4B：

```text
              R16 39k
TP8 ─────────/\/\/\── U4B_N
                         │
                       R15 1k
                         │
                      AGND_R15
```

真正控制闭环的是：

```text
U4B_N - U4P
```

而不是相对于某个抽象“全板 AGND”。

假如输出电流/电源电流产生：

```text
100 kHz local ground bounce
```

并通过 R15 底端进入反馈：

```text
TP8变化
↓
电源/地电流变化
↓
AGND_R15变化
↓
U4B -IN变化
↓
TP8进一步变化
```

就可能形成另一种公共阻抗反馈。

所以第二个 fault matrix 应该把 AGND 分区：

```text
AGND_J2
AGND_U4_DECOUP
AGND_R15
AGND_AD633
AGND_R3
```

而不是一个节点。

重点扫描例如：

```text
R = 1 / 5 / 10 / 20 / 50 / 100 mΩ
L = 0.5 / 1 / 2 / 5 / 10 / 20 / 50 nH
```

尤其是：

```text
AGND_R15 ↔ AGND_U4
```

这个路径。

这比继续加：

```text
J1 lead inductance
```

重要得多。

---

# 四、第三优先级：OPA548 OFF 模型仍然是最大未知器件模型

当前文件自己也写得很清楚：

```text
OPA548 OFF
≠ TI macro
```

而是一个：

```text
datasheet-constrained surrogate
```

这是合理的工程选择，但它也意味着：

> **目前跟实板现象相关性最强的一个器件状态，恰恰还没有真实模型。**

实板非常特殊的证据是：

```text
改变J1
→ TP8振荡形态明显变化
```

尤其：

```text
约6V附近出现状态变化
```

所以 OPA548 OFF 输入绝不是完全无关。

目前 surrogate：

```text
RDIFF = 10 MΩ
CDIFF = 6 pF
RCM = 1 GΩ
CCM = 4 pF
COFF = 20 pF
```

仍然是**线性近似 + 简单二极管钳位**。

真实芯片可能存在：

```text
+IN → 内部差分级
+IN → E/S相关节点
+IN → OUT
+IN → V+/V-
-IN → OUT
```

的频率相关、非线性路径。

所以建议第三组 fault matrix 不要直接“乱改OPA548”。

而是专门增加：

```text
C(INP,OUT)
C(INP,PWR_N)
C(INP,PWR_P)
C(INP,INN)
R(INP,OUT)
```

分别扫。

例如：

```text
CIN_OUT：
0.1p → 0.2p → 0.5p → 1p → 2p → 5p → 10p → 20p

CIN_RAIL：
1p → 5p → 10p → 50p → 100p

RIN_OUT：
100M → 10M → 1M → 100k
```

重点不是找到某一个“真实值”。

而是回答：

> **是否存在一个物理上合理的小耦合，就能够把健康63°环路推到105kHz异常？**

如果必须加：

```text
500pF
```

才能复现，那么这个假设就应该降级。

如果：

```text
1~5pF
```

即可高度复现，那就值得继续做实板验证。

---

# 五、第四优先级必须查“实际装配状态 ≠ KiCad”

这是非常容易被 SPICE 忽略的一类根因。

SPICE现在证明的是：

> **“如果板子真的和KiCad/BOM一样”，它应该稳定。**

所以恰恰应该检查：

```text
实板到底是不是真的和KiCad一样？
```

尤其我建议实板直接逐项确认：

| 元件应有状态 | |
| --- | --- |
| R15 | 1 kΩ |
| R16 | 39 kΩ |
| R5 | 100 Ω |
| C14 | **DNP** |
| C37\~C41 | **DNP** |
| C15 | 100 nF |
| C16 | 100 nF |
| C10 | 100 nF |
| C11/C12  | 1 µF |
| U4 | 真正 OPA1656，型号/顶标正确 |
| FB1/FB2  | 与BOM一致 |
| D1/D2 | 与设计一致 |

这里尤其需要重新强调：

### C14

历史版本里出现过：

```text
C14 = 100 nF
```

而当前版本是：

```text
C14 = DNP
```

如果加工厂用了旧贴片文件/BOM，那么：

> SPICE模拟的是DNP，但所有实板可能统一贴了错误电容。

这会完美符合：

```text
不是随机单板故障
而是每块板都具有同一个问题
```

所以这个检查的优先级甚至高于换U4。

---

# 六、第五优先级：U4型号错误，而不只是“U4损坏”

如果只有一块测试板出现问题：

```text
U4损坏
```

很合理。

如果多块同批次板都出现：

```text
约100~110kHz
```

则应该把：

> **装错运放**

放到很高的位置。

例如：

```text
封装兼容
引脚兼容
但GBW / 稳定性 / 输入结构不同
```

的器件被错误贴装。

这类问题的特点就是：

```text
PCB连续性全部正确
R15/R16全部正确
SPICE用OPA1656永远稳定
实板却每块都振
```

所以建议实际读：

```text
U4 top marking
```

并与 OPA1656 的实际批次标记规则核对。

不要只依赖加工BOM记录。

---

# 七、第六优先级：真实105kHz源可能在供电/地，而不是TP7

现在 `HFAMP` 是：

```spice
VHF ZHF AGND SIN(...)
```

也就是人为把105kHz污染注入AD633/TP7方向。

但真正的板子也可能是：

```text
J2电源存在105kHz ripple
```

或者：

```text
AGND存在105kHz common-mode disturbance
```

然后经 PSRR/CMRR/非线性耦合进入 U4B。

所以建议新增：

```text
HF_J2P
HF_J2N
HF_AGND
```

分别扫描：

```text
100 µV
300 µV
1 mV
3 mV
10 mV
30 mV
100 mV
```

频率：

```text
80k
90k
100k
105k
110k
120k
150k
```

判断是否存在很明显的：

```text
105kHz选择性放大
```

这还有一个很现实的来源：

**台式电源控制环/开关频率。**

当前模型：

```text
理想电压源 + R/L
```

并没有模拟真实bench supply的控制环。

因此如果100～110kHz恰好来自外部电源，它永远不会在当前SPICE里“自己出现”。

实板最直接的对应测试就是：

```text
OPA OFF

TP11 ANA_P 对 TP16
TP12 ANA_N 对 TP16

AC coupling
10~20mV/div
2us/div
```

重点找：

```text
100~110kHz
```

这里需要真正使用短地弹簧，不能再长地夹跨节点。

---

# 八、我建议 fault matrix 不要超过这7组

按照当前证据，优先级应该是：

| 顺序Fault family原因 | | |
| --- | --- | --- |
| **1** | `VCMD → U4B +IN` PCB互电容 | 当前 extraction 明显可能漏掉，且能形成真正正反馈 |
| **2** | 分布式 AGND / R15底端 ground bounce | 当前模型把模拟地过度理想化 |
| **3** | OPA548 OFF 高频非线性/内部耦合 | J1依赖强烈支持其参与 |
| **4** | 实际BOM/贴装状态不符 | nominal PCB SPICE稳定后优先级大幅上升 |
| **5** | 错装/异常 OPA1656 | SPICE无法覆盖实际硅片错误 |
| **6** | J2/AGND外部105kHz污染 | 当前理想电源不会自动生成 |
| **7** | C15/C16/FB等局部器件故障 | 可做单件 fault injection |

我反而暂时不会继续重点扫：

```text
R15从1k变到1.1k
J1电感0.2u变0.3u
探头10p变15p
DNP stub增加10%
```

因为已经证明 nominal 系统有约63°裕量，这种小变化不太可能凭空把它推成10 V级100kHz自激。

---

# 九、什么样的 fault 才算“找到根因”

这是下一轮SPICE最重要的筛选规则。

不能只满足：

```text
“会振”
```

必须同时满足：

### 条件A

```text
频率 = 100~110kHz附近
```

### 条件B

```text
TP7只有很小信号
但TP8可以进入几V乃至接近轨
```

### 条件C

```text
J1改变到约6V附近时
波形/幅度发生明显改变
```

### 条件D

```text
OPA OFF时已经存在
```

### 条件E

```text
增加100/220pF后
异常明显下降
```

### 条件F

```text
OPA ON以后
J4 OPEN仍能通过snubber等路径产生70mA级电流
```

只有一个 fault family 能同时满足：

```text
A+B+C+D+E+F
```

时，才值得称为：

> **核心根因候选。**

如果只是：

```text
加4.7nF
→ 1.3MHz自激
```

虽然也叫“振荡”，但应该直接淘汰。

---

## 当前我最看重的两个方向

基于这版 PCB-aware 模型，我现在最建议先跑：

```text
① VCMD → U4B +IN mutual-C sweep
```

以及：

```text
② 分布式 AGND / R15 return impedance
```

原因不是它们一定正确，而是：

> **它们是目前 PCB extraction 中真正没有覆盖、又能够形成正反馈的两个物理机制。**

而 OPA548 OFF 非线性排第三，是因为它已经确定参与 J1 依赖，但目前还缺“它能主动制造105 kHz”的证据。

所以这版 SPICE 的意义已经不是继续证明“PCB没问题”，恰恰相反：**它把问题从普通R/L/C寄生缩小到了“互耦、局部地回路、器件非线性/装配状态”这几个真正有可能被一阶PCB模型漏掉的层次。**

如果下一轮 fault matrix 按这个顺序跑，最有可能真正把根因从“还有若干可能”压到一两个可直接在实板上证伪的机制。

继续建立新的SPICE并检查结果

---

# chatgpt response

我会直接在 `PCB_AWARE_SPICE_v1` 上扩展 fault matrix，不再改基础 nominal。第一轮先做你排前两位的机制：`VCMD→U4B +IN` 互电容，以及 `R15 local ground ↔ U4/AD633/J2 ground` 的分布式公共阻抗；筛选标准严格按 100–110 kHz、伏级 TP8、Cfb 可抑制、J1 依赖来判。

互电容第一轮已经给出很清楚的方向：`VCMD→U4B +IN` 从 0 扫到 **5 pF** 时 PM 只从 63.52°降到约60.54°，甚至 20 pF 仍约50°；它主要把 MHz 级交越往更高频推，并没有制造105 kHz选择性。也就是说，物理上合理的 0.02–2 pF 直接互电容不是主因。接下来我把重点转到分布式地回路，而不是继续把互电容扫到不现实的几十/上百 pF。

第二组也基本被否定：即便把 `R15/局部U4地` 的公共阻抗扩大到很不现实的 **1 Ω + 100 nH**，PM仍约 **63.4°**；在你建议的 1–100 mΩ、0.5–50 nH 范围内变化几乎不可见。因此“正常公共地阻抗本身形成105 kHz正反馈”不是主因。  
现在我转到第三组：OPA548 OFF 内部未建模耦合，并同时检查“实际贴装状态≠KiCad”里哪些错误元件状态有能力产生目标频率。

继续按你的 A–F 判据做了新一轮 fault matrix，并且已经生成一个新的参数化 SPICE。结果出现了明显收敛：你提出的前几类 PCB 漏建机制大多可以降级，而第一个真正落在 100–110 kHz 的候选已经出现。

### 1. `VCMD → U4B +IN` 互电容：基本降级

直接加入：

```spice
CXP U4O U4P {C_VCMD_PLUS}
```

扫描 0.02 pF～50 pF。

物理上比较合理的范围结果：

```text
0 pF     PM ≈63.5°
0.1 pF   ≈63.5°
0.5 pF   ≈63.2°
1 pF     ≈62.9°
2 pF     ≈62.4°
5 pF     ≈60.5°
```

即使到了很大的 20 pF，PM 仍约 50°。

在 105 kHz 处，0～5 pF 几乎不改变 loop gain/phase：

$$
|T|\approx+22.5{\rm dB},\qquad
\angle T\approx-93^\circ
$$

所以：

> **实际 PCB 中合理的0.02～2 pF VCMD→+IN互电容不能解释100–110 kHz。**

这条从第一优先级明显下降。

[互电容扫描](sandbox:/mnt/data/PCB_AWARE_SPICE_fault_v2_release/results/mutual_c_ac.csv)

---

### 2. R15/local AGND 公共阻抗：也基本降级

我把 R15 bottom ground 单独拆出来，扫描：

```text
R = 1～100 mΩ
L = 0.5～50 nH
```

随后又故意扩大到：

```text
1 Ω + 100 nH
```

结果 PM 仍然大约：

$$
63.4^\circ\sim63.8^\circ
$$

没有出现105 kHz选择性。

而实际 PCB 还有 F.Cu/B.Cu AGND pour；真实公共阻抗大概率比故意施加的极端值更低。

因此：

> **正常的R15 ground bounce不能作为100 kHz第一根因。**

[局部地扫描](sandbox:/mnt/data/PCB_AWARE_SPICE_fault_v2_release/results/local_ground_ac.csv)

[更极端U4局部地扫描](sandbox:/mnt/data/PCB_AWARE_SPICE_fault_v2_release/results/u4_local_ground_ac.csv)

---

### 3. OPA548 OFF漏掉的普通被动耦合：也不够

我分别加入：

```text
C(INP,OUT)
C(INP,PWR_P)
C(INP,PWR_N)
C(INP,INN)
R(INP,OUT)
```

电容一直扫到：

$$
100pF
$$

电阻从：

$$
100M\Omega\rightarrow100k\Omega
$$

结果对 U4B loop 仍只有很小影响。

甚至进一步构造了 band-limited negative input admittance，故意让 OPA548 OFF 输入表现出主动负导纳，也没有自然产生105 kHz模式。

所以当前结论变成：

> **如果 OPA548 OFF 是关键参与者，缺失的必须是非线性状态转换/内部主动机制，而不是“数据手册少写了几pF”。**

[OPA548 OFF耦合扫描](sandbox:/mnt/data/PCB_AWARE_SPICE_fault_v2_release/results/opaoff_coupling_ac.csv)

---

### 4. 普通装配错误也基本没有命中105 kHz

我又扫了：

- R15错值；
- R16错值；
- R5错值；
- C14/C37～C41误贴；
- 单个/多个去耦开路；
- FB状态等。

其中有趣的是 R15：

```text
R15 = 1k      → 正常
R15 = 2k      → PM≈46°
R15 = 5k      → PM≈17°
R15 = 10k     → PM≈2°
R15 = 39k     → PM<0
```

但它失稳的 crossover 在：

$$
\approx2.5MHz
$$

而不是100–110 kHz。

R16反过来即使大到390 kΩ，把 crossover 降到约144 kHz，PM仍约91°。

所以：

> **一个普通的R15/R16/R5错值不能同时解释“105 kHz + Cfb有效 + TP7干净”。**

[装配 fault matrix](sandbox:/mnt/data/PCB_AWARE_SPICE_fault_v2_release/results/assembly_fault_ac.csv)

当然，实际 BOM/贴装仍然应该实测核验；这里只是说明“这些典型错值的动力学特征不匹配”。

---

# 5. 一个此前隐藏的完整反馈链也补回来了

这次审查发现 `PCB_AWARE_SPICE_v1` 虽然放了 U4A 和 AD633，但实际上：

```text
U4A +IN → 0
AD633 X/Y → 0
```

所以真正的：

```text
OPA548 / RSH2
 ↓
INA149
 ↓
U4A ×50.9
 ↓
AD633
 ↓
U4B ×40
 ↓
OPA548 +IN
```

并没有闭合。

这次已经修正。

INA149官方 PSpice宏模型和 ngspice+AD633 联合 transient 存在数值兼容问题，因此 transient 使用按约500 kHz带宽建立的一阶 INA149 surrogate，避免把模型收敛问题当成电路不稳定。

新的完整链模型：

[完整电流反馈链 OFF 模型](sandbox:/mnt/data/PCB_AWARE_SPICE_fault_v2_release/PCB_AWARE_FULLCHAIN_OFF_v2_ina_surrogate.cir)

结果仍然稳定。

VK：

```text
-0.62
0
0.5
1
2
2.68 V
```

全部没有自激。

人为给 TP7：

$$
1mV_{pk}@105kHz
$$

得到：

$$
TP7\approx2mV_{pp}
$$

$$
TP8\approx80mV_{pp}
$$

正好是正常约40倍。

更重要的是：

$$
V_{RSH2,pp}\approx33nV
$$

几乎为零。

原因是 J4 OPEN 时：

```text
snubber current:
DRV → 4.7Ω → 47nF → PGND
```

根本不流过：

```text
RSH2
```

因此 INA149→U4A→AD633 这条全局阻抗控制链，在 J4 OPEN / OPA OFF 条件下基本闭合不起来。

这条也明显降级。

[完整链 VK/HF结果](sandbox:/mnt/data/PCB_AWARE_SPICE_fault_v2_release/results/fullchain_vk.csv)

---

# 6. 然后出现了现在最重要的定量约束

健康 PCB-aware 模型在：

$$
105kHz
$$

环路是：

$$
|T|\approx+22.51dB
$$

$$
\angle T\approx-93.04^\circ
$$

所以如果要让它在105 kHz满足 Barkhausen 附近条件：

$$
|T|\approx0dB
$$

$$
\angle T\approx-180^\circ
$$

缺失机制大约需要：

$$
\boxed{-22.5dB}
$$

额外幅度变化，同时：

$$
\boxed{-87^\circ}
$$

额外相移。

这已经是一个非常强的物理约束。

几十 nH、几 pF、几十 mΩ根本不是这个尺度。

---

# 7. 第一个真正命中105 kHz的 fault：U4B内部动态异常

我没有声称真实芯片“有一个8 kHz电容”。

这里建立的是一个**器件内部故障等效模型**：

```text
正常 OPA1656 macro
       ↓
额外动态退化
       ↓
真实PCB负载/反馈
```

先加一个等效低频极点，发现约：

$$
f_p\approx8kHz
$$

会把系统拉到：

$$
f_c\approx105kHz
$$

并只剩约1°左右 PM。

随后我加入第二个很高的弱极点，只提供剩余的一点相移。

修正过模型输出阻抗后的最终结果是：

```text
内部等效 pole 1 = 8 kHz
内部等效 pole 2 = 3 MHz
```

得到：

$$
\boxed{f_c=105.7kHz}
$$

$$
\boxed{PM=-0.75^\circ}
$$

这已经是真正的线性失稳。

而不是“1.3 MHz也振，所以算复现”。

---

# 8. 更重要的是 Cfb 行为也完全符合

同一个 fault：

| Cfb | crossover | PM |
|---:|---:|---:|
| DNP | **105.7 kHz** | **−0.75°** |
| 22 pF | 114.8 kHz | **29.2°** |
| 47 pF | 149.1 kHz | **52.8°** |

继续增加100 pF时也进入健康稳定区域。

所以它同时满足了两个很难同时满足的实板条件：

```text
没有Cfb
→ 105kHz失稳

加几十pF
→ 明显稳定
```

这目前是所有 fault family 里第一次真正做到。

---

# 9. transient也产生了105 kHz增长，不只是AC数学结果

我对修正后的两极点模型做了启动 transient。

只使用原模型自带的：

```text
1 mV startup kick
```

没有人为持续输入105 kHz。

Cfb=DNP：

开始后 TP8 的窗口 Vpp：

```text
约20～40 us   → 0.105 Vpp
随后          → 持续指数增长
到约200 us    → 0.21 Vpp
```

零交叉计算出的实际频率：

$$
\boxed{105.61kHz}
$$

增长时间常数约：

$$
\tau\approx231\mu s
$$

而此时 TP7 最后窗口只有：

$$
\boxed{\sim0.15\mu V_{pp}}
$$

所以这是当前第一次用 PCB-aware SPICE 得到：

```text
TP7几乎没有105kHz信号
        ↓
TP8自己产生105.6kHz增长
```

这正是实板最核心的现象之一。

[短时启动 transient](sandbox:/mnt/data/PCB_AWARE_SPICE_fault_v2_release/results/candidate_short_transient.csv)

---

## 继续跑到0.54 ms

为了确认不是短暂振铃，我单独延长了 DNP 模拟。

结果：

```text
0.10 ms → TP8约0.20 Vpp
0.20 ms → 约0.31 Vpp
0.30 ms → 约0.47 Vpp
0.40 ms → 约0.73 Vpp
0.50 ms → 约0.95 Vpp
```

仍持续增加。

TP7仍然只有亚 µV 级。

按照当前线性增长率，如果不进入非线性：

$$
\sim1ms
$$

附近就会达到数伏乃至接近轨。

实际厂商宏模型在约0.54 ms开始因 OFF surrogate 钳位/AD633宏模型的强非线性进入 timestep-too-small，所以我没有把“求解器失败”伪装成一个16 Vpp数值。

但在失败之前：

> **105 kHz模式是在增长，而不是衰减。**

这一点已经明确。

---

# 10. 加22 pF以后 transient立即变了

完全相同 fault：

$$
Cfb=22pF
$$

启动最大瞬态只有：

$$
\approx11.5mV
$$

随后迅速衰减到数 nV。

47 pF：

$$
\approx1.6mV
$$

随后也消失。

所以当前模型已经同时满足：

### A
$$
f\approx105.6kHz
$$

✓

### B

TP7极小、TP8自产生增长

✓

### D

OPA548为 OFF surrogate 时已经成立

✓

### E

22/47 pF明显消除

✓

这是目前远强于任何PCB正常寄生假设的匹配。

---

# 11. 另外一个有物理含义的 U4 fault 也命中105 kHz

你测的是：

```text
U4 pin6金属脚 → PCB pad
≈20mΩ
```

所以外部虚焊已否定。

但是这个测量**看不到封装内部**：

```text
metal lead
 ↓
bond / ESD / internal input structure
 ↓
silicon -IN
```

因此我重新把之前的高阻模型放到了封装内部，而不是PCB焊点：

```text
PCB U4B_N
   ↓
pin6 metal
   │   ← DMM测到这里都是20mΩ，仍正常
   ↓
Rinternal fault
   ↓
actual silicon -IN
```

PCB-aware结果：

$$
R_{internal}\approx1.8M\Omega
$$

并取非常小的内部寄生：

$$
C\approx0.05pF
$$

得到：

$$
\boxed{f_c=105.82kHz}
$$

$$
PM\approx5.18^\circ
$$

把内部寄生降到0.01 pF：

$$
PM\approx2.45^\circ
$$

而：

```text
22 pF → PM≈35.7°
47 pF → PM≈61.2°
100pF → PM≈74.6°
```

也符合补偿现象。

[U4内部输入路径 fault sweep](sandbox:/mnt/data/PCB_AWARE_SPICE_fault_v2_release/results/u4_internal_input_fault_ac.csv)

需要强调：

> **这不意味着我认为真实芯片里面一定存在1.8 MΩ。**

这个数字只是说：

> 某种能够把真正硅片−IN与外部pin6动态隔离的内部故障，其端口行为可以自然落到105 kHz。

它可以代表：

- 输入级损伤；
- ESD结构损伤；
- bond/die内部异常；
- 错型号器件；
- 假料/异常硅片；
- 其他宏模型完全没有表达的内部状态。

---

# 12. 因此现在根因排序已经实质性改变

新 fault matrix：

| 排名 | Fault family | 结论 |
|---:|---|---|
| **1** | **U4B内部动态/补偿异常** | **目前唯一真正得到105.6kHz负PM并被22–47pF修复的模型** |
| **2** | **U4B内部−IN路径异常** | **自然落到105kHz，外部20mΩ测量不能排除** |
| 3 | J2/ANA rail已有100–110kHz大幅污染 | 有真实传递路径，但需要非常大的rail ripple |
| 4 | OPA548 OFF真实非线性状态 | 仍可能解释J1≈6V后波形改变，但普通pF/MΩ耦合已否定 |
| 5 | 实际装配/错器件 | 普通R/C错值不匹配，但“U4错型号”仍然非常值得查 |
| 6 | VCMD→+IN互电容 | 合理pF范围已否定 |
| 7 | R15/local AGND ground bounce | 合理甚至夸张范围都基本否定 |

[完整 Fault Matrix 汇总](sandbox:/mnt/data/PCB_AWARE_SPICE_fault_v2_release/results/FAULT_MATRIX_SUMMARY.csv)

---

# 13. 外部电源105 kHz也被量化了

ANA rail→TP8 的传递确实存在：

100 kHz：

$$
ANA+\rightarrow TP8\approx2.21V/V
$$

$$
ANA-\rightarrow TP8\approx2.12V/V
$$

110 kHz约：

$$
2.48/2.39V/V
$$

但如果想得到：

$$
TP8=16V_{pp}
$$

所需100–110 kHz rail ripple 大约是：

$$
3.2\sim3.8V_{pk}
$$

这已经非常夸张。

所以普通：

```text
10mV
30mV
100mV
```

电源纹波不足以解释近轨TP8。

[达到不同TP8幅度所需rail ripple](sandbox:/mnt/data/PCB_AWARE_SPICE_fault_v2_release/results/required_rail_ripple.csv)

---

# 14. J1≈6V波形转变仍然是现在尚未完全闭合的一项

这个必须单独说。

目前最强 U4 fault 可以解释：

```text
A  105kHz             ✓
B  TP7小 / TP8增长     ✓
D  OPA OFF已经出现      ✓
E  Cfb强烈抑制          ✓
```

而过去 J4 OPEN 功率级测试已经证明：

```text
F  TP8大幅105kHz
   ↓
   OPA ON
   ↓
   4.7Ω+47nF snubber
   ↓
   70mA级甚至更大电流
```

也是成立的。

但是：

### C

```text
J1约±6V
→ 规则105kHz突然变成不规则纹波
```

还没有一个足够可信的 OPA548 OFF 宏模型进行定量闭环。

简单的：

```text
几pF
几MΩ
负导纳
```

我已经都试过，不够。

所以当前最合理的分层解释是：

```text
U4B异常动态
       ↓
首先产生105kHz
       ↓
TP8已经进入较大振幅
       ↓
OPA548 OFF内部真实高频非线性开始参与
       ↓
J1改变
→ 输入保护/内部shutdown状态改变
       ↓
极限环波形发生变化
```

即：

> **U4B更像振荡发生器，OPA548更像振荡状态改变器。**

这与我们更早的判断重新汇合了，但现在有了更强的 PCB-aware fault-matrix 支持。

---

# 15. 新的可运行 fault-matrix SPICE

我把这些 fault 全部做成了一个参数化版本：

[下载 PCB_AWARE_FAULT_MATRIX_v2.cir](sandbox:/mnt/data/PCB_AWARE_SPICE_fault_v2_release/PCB_AWARE_FAULT_MATRIX_v2.cir)

默认参数就是“无故障 PCB”：

```spice
.param C_VCMD_PLUS=1a

.param R_R15_GND=1u
.param L_R15_GND=1p

.param C_OFF_INP_OUT=1a
.param C_OFF_INP_P=1a
.param C_OFF_INP_N=1a
.param C_OFF_INP_INN=1a
.param R_OFF_INP_OUT=1T

.param U4N_RINT=1u
.param U4N_CINT=1a

.param U4_FP1=1e12
.param U4_FP2=1e12
```

无 fault 实测：

$$
f_c=1.1371MHz
$$

$$
PM=63.81^\circ
$$

和 full extraction 的63.79°基本重合。

验证表：

[新模型验证结果](sandbox:/mnt/data/PCB_AWARE_SPICE_fault_v2_release/validation_summary_v2.csv)

---

如果要重现目前最强候选，只需要改：

```spice
.param U4_FP1=8k
.param U4_FP2=3Meg
```

此时：

```text
Cfb=DNP
fc ≈105.7kHz
PM ≈ -0.75°
```

再改：

```spice
.param CFB=22p
```

得到：

```text
fc ≈114.8kHz
PM ≈29.2°
```

或者：

```spice
.param CFB=47p
```

得到：

```text
fc ≈149.1kHz
PM ≈52.8°
```

这已经是一个比较有用的“故障等效模型”，因为它明确告诉我们下一步实板应该验证什么：

> **不要再把重点放在PCB几pF/几十nH。现在优先确认U4是否真的是正确、健康的OPA1656，以及当前振荡板换一颗全新的、来源可靠的OPA1656后，Cfb仍DNP时100–110kHz是否立即消失。**

如果换 U4 后直接消失，这一轮 fault matrix 与实板会形成非常强的闭环。

目前尚未完全完成的只有一项：**OPA548 OFF真实高频非线性导致“J1≈6V波形转变”的器件级模型**。TI宏模型的 shutdown transient 不足以可信完成这一项，所以我没有用不可靠宏模型强行制造一个“全A–F通过”的结果。其他主要 fault family 已经完成了有效筛选。 memcite
