341151719/sine-resistor-pcb-analysis/实验还原部分/主动审计/EVIDENCE_REASSESSMENT_20260915.md

# 实验还原证据重新审查（2026-09-15）

审查基线：`b0989a9`。对象为现有 V7 实板记录及对应网表，V8 数据只用于识别版本差异。
本轮确认了分析错误和覆盖范围问题，尚未识别实板 100–110 kHz 的唯一物理根因。
没有修改 PCB、器件值、官方宏模型或历史原始日志。

## 1. 直接验证的错误：峰值电流不能证明持续 70 mA CC

`早期错误复现/02_opa_on_105k_amp2V.cir` 向 OPA548 注入已存在的 2 Vpk、105 kHz 信号。
保留原电路和时间窗，仅增加平均电流测量，ngspice-42 得到：

| 指标 | 正轨取电 | 负轨取电（幅值） |
|---|---:|---:|
| 瞬时峰值 | 69.14 mA | 68.75 mA |
| 0.2–0.5 ms 平均值 | 23.62 mA | 23.48 mA |

输出约 4.111 Vpp。原先由 69 mA 峰值推导“已解释约 70 mA CC”不成立。
模型只有理想电压源，没有台式电源限流控制，也没有板上 C5/C6=470 µF。
这些电容可以提供部分高频脉冲电流，电源的平均补充电流和瞬时器件取电并不等同。
是否进入 CC 还取决于供电动态、其他负载、实际波形及电源响应，不能只比较一个峰值。
平均值小于 70 mA 同样不能证明实板不可能 CC。

四个幅度案例均已增加 `IP_DRAW_AVG` 和 `IN_DRAW_AVG`。旧日志保留历史记录，
新复跑由 `reassess_evidence.py` 保存至 `results_reassessment/`。

## 2. 健康模型是否因为刺激太弱而漏检？

原 `fault_fixed_common.inc` 使用理想 ±10 V/±5 V 供电、E/S=V−+0.6 V，
输入为 1 mV、2 µs 单次脉冲。原结果只覆盖这一状态。

本轮追加 ±250 mV、10 µs 单次输入脉冲，将瞬态延长至 5 ms，最大步长 50 ns。
分别使用 Gear 和 trapezoidal 积分，考察 4.5–5 ms 的 TP8 峰峰值：

| 输入脉冲 | 算法 | 10–100 µs 的 TP8 摆幅 | 4.5–5 ms TP8 峰峰值 |
|---|---|---:|---:|
| +250 mV | Gear | 9.152 V | 约 1.69e-11 V |
| +250 mV | Trap | 9.150 V | 约 1.25e-7 V |
| −250 mV | Gear | 9.320 V | 约 1.22e-11 V |
| −250 mV | Trap | 9.319 V | 约 1.80e-7 V |

四例均有完整晚期测量。小残差按数值残余解读，不视为物理振荡。
这支持：在这个固定 OFF、理想供电拓扑中，单次较大扰动没有维持目标振荡。
它没有测试上电顺序、电源限流、任意初始条件或真实 E/S 动态，不能外推为实物安全。

## 3. “TP7 基本干净”需要带宽和幅值上限

同一健康拓扑在 105 kHz 的小信号 AC 传递：

- `|TP8 / SRC| ≈ 40.035`，相位约 −4.60°；SRC 经 100 Ω 连接 U4B +IN。
- 在这个线性模型内，18 Vpp 输出所需输入约为 `18 / 40.035 ≈ 0.450 Vpp`。
- 1 mVpp 的输入对应约 40 mVpp 输出，不能直接线性放大成 18 Vpp。

0.450 Vpp 只是线性估计，接近饱和时要做大信号分析。原记录没有提供同一时刻的
TP7 幅度上限、示波器带宽、倍率和完整波形，因此“干净”不能在模型中自动替换成
理想零阻抗、零交流信号。还需区分远端 TP7 与 U4 pin5 局部节点。

## 4. 反馈比例的适用条件被历史分析说得过强

V7/V8 PCB 都标注 R15=1 kΩ、R16=39 kΩ；V7 工程 BOM 将 C39 标为 DNP。
在没有反馈电容、输入电流可忽略且 R15 底端为同一参考地时，负输入约为输出的 1/40。
外部 pin6→U4B_N 约20 mΩ只验证该外部连接，不能证明其他元件的实装值。

如果 R16 并联 Cfb，反馈比例为：

`β(jω) = R15 / [R15 + R16/(1+jωR16Cfb)]`

105 kHz 正弦分量的示例：

| Cfb | β的幅值 | 输出为18 Vpp正弦时的负输入 |
|---:|---:|---:|
| 0 pF | 0.0250 | 0.450 Vpp |
| 22 pF | 0.0287 | 0.517 Vpp |
| 68 pF | 0.0503 | 0.906 Vpp |
| 220 pF | 0.1423 | 2.561 Vpp |

因此，历史“18 Vpp/0.9 Vpp 与1k/39k物理上不相容”的表述必须限定补偿状态、波形、
参考地和输入电流。68 pF 示例只证明比例受电容影响，不证明实板装了68 pF；
上述表格适用于正弦分量，不能直接套用方波的总峰峰值。补偿还会改变相位。
R16×220 pF 的18.5 kHz 是反馈阻抗转折频率，也不等于整个闭环只有一个18.5 kHz低通极点。

## 5. 历史结论与后续审计不同步

后续 `ACTIVE_AUDIT_REPORT.md` 已发现 H07/H08 的 OPA548 供电节点断链，
但总表及原假设页仍显示旧“已完成”。本轮同步状态：

- H07 后续改为其假设声明的固定±10/±5 V偏置；nominal、1Ω、10Ω三例均完成且TP8晚段0 Vpp。这不覆盖PWL上电过程。
- H08 修正版三例未复现，但 C27 从 V7 的10 pF换成 V8 的10 nF，属于版本改变。
  它不能单独代替 V7 原板的验证结果。
- H04 仍为未完成，不能计入有效负结果。

本轮重新运行了 H07/H08 固定偏置deck，并由 `run_checks.sh` 核对每个日志必须包含3个案例标记、3个数据块且无失败标志。

## 6. 因果判断与官方模型边界

### 命令 OFF 与硬件状态

记录有 TP9−TP14=0.55–0.65 V，但缺少振荡时刻的同步波形。
R10=100 kΩ 存在关断裕量风险，也不能据此认定所有记录中 OPA548 都确实 ON。
需要实际 E/S 相对负轨的动态值来确定。

“改变 J1 后振荡改变”支持功率支路参与，不能确定 U4B 先起振、OPA548 只改变形态。
二者可能共同构成反馈环路；尚缺 R5 拆除/恢复的可重复对照。
“新板 pin6 连通也正常”并没有证明新板上电后也同样振荡。

### H12 的 E/S 包装不是厂商保证的动态模型

`OPA548_ES_DELAYED` 用固定 IES、理想控制源和状态电容替代外部 E/S 行为，
把官方宏 E/S 与真实外部节点隔开。其0.8/2.4 V之间保持状态的实现是假设；
数据表的 LOW/HIGH 保证边界并不等价于保证有这样的迟滞记忆。
1/3 µs 也被当作一阶时间常数使用，不能直接等同于数据表的完整关断/开启时间。
H12可用于探索该假设，但无法排除它没有表达的输入—E/S—供电耦合。

### 数据表引用的两项限制

TI 的 [OPA548 数据表](https://www.ti.com/lit/ds/symlink/opa548.pdf)规定推荐供电最低±4 V。
早期±2.5 V实验及低压扫描超出这个范围，宏模型在那里收敛不构成行为保证。

同一数据表第7.4.1节的20 kHz提示位于输出禁用/多路复用语境：高频信号可能增加
关断器件泄漏。它没有证明+IN一定出现导致105 kHz的负阻抗，不能拿该文字直接定位根因。
第6.5节的输入线性范围和第6.1节的绝对额定范围也需分别考虑：
J2±10 V前级的数伏大信号通过100Ω进入低电压供电的OPA548，可能进入输入过驱状态。
是否实际钳位应由R5两端电压及器件脚位电压确认，不能只由TP8单点推断。

## 7. 当前最有区分力的实板证据

| 对照/测量 | 可以区分什么 |
|---|---|
| 相同上电与补偿条件下，R5接入→拆除→恢复 | 后级支路是否是维持振荡的必要条件；不能单独证明OPA548损坏 |
| 同步 TP8 与 E/S−V− | 异常是否在硬件确实关断时存在，是否伴随状态切换 |
| R5两端同步差值，除以实测R5 | 后级加载电流的方向和幅值，识别钳位/非线性负载参与 |
| R5断开后仍振时，用可靠来源U4替换并复测 | 器件/局部环路与后级支路的区分 |
| 同步供电电压、平均电流及CC状态 | 区分高频负载峰值、真实供电失稳和持续过载 |

沿用实板安全排障计划；断电改焊。普通示波器地夹接共同参考地，测E/S−V−或R5差值
用额定合适的差分测量，或共同参考下两通道相减；不把地夹接到负轨或信号节点。

## 8. 复现与结果解释

运行 `python3 实验还原部分/主动审计/reassess_evidence.py`。
需要ngspice及Python标准库；脚本保存9个仿真案例（4电流、1 AC、4启动）的输入/日志和JSON。
脚本检查返回值、失败标志、测量存在性与有限性，并验证峰值/均值关系、标称增益和启动衰减。
`checks_passed_root_cause_unresolved` 明确表示复核通过，硬件根因仍未确定。

现在可支持的判断是：健康固定OFF基线即使遭受较大扰动也不维持目标振荡；
实物与这个基线之间仍缺少状态、加载、器件或供电方面的必要条件。
本轮最明确的推进是纠正证据链，并把后续判别收敛到可观测的电流与状态；不能宣称已修复实板。
