341151719/sine-resistor-pcb-analysis/SPICE部分/validation_workspace_20260904_19wI9s/requirements/all_summary.csv

case | model | status | tail_start_s | softstart_tstart_s | softstart_tramp_s | pamp_pa | itest_amp_a | itest_freq_hz | rtarget_cmd_min_ohm | rtarget_cmd_max_ohm | rtarget_des_min_ohm | rtarget_des_max_ohm | rx_cmd_min_ohm | rx_cmd_max_ohm | iport_pk_a | iport_pk_tail_a | iport_threshold_for_reff_a | vspk_pk_v | vspk_pk_tail_v | vel_pk_mps | x_pk_m | xmax_ratio_pk | power_port_pk_w | qeff_min | qeff_max | rem_min | rem_max | synerr_rms_tail_v | synerr_abs_max_tail_v | synerr_norm_rms_tail | cmderr_rms_tail_v | cmderr_abs_max_tail_v | reff_fit_tail_ohm | rx_fit_tail_ohm | reff_fit_err_vs_tail_mean_ohm | rtarget_tail_mean_ohm | rtarget_tail_rms_dev_ohm | reff_fit_sample_count | reff_pointwise_rms_err_tail_ohm | reff_pointwise_abs_err_tail_max_ohm | reff_pointwise_valid_fraction_tail | opa548_vsat_max_v | follow_error_pk_v | follow_error_rms_tail_v | ilim_ratio_pk | ilim_ratio_tail_pk
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
