341151719/sine-resistor-pcb-analysis/KICAD部分/正弦电阻V8_KiCad10.0.4_稳定性修正版_2026-09-04/audit/KiCad_conversion_audit.xlsx

Sheet: Summary
正弦电阻 V7 — EasyEDA Pro → KiCad 10.0.4 转换审计
审计项目 | 结果
源 EPRO 原理图组件 | 142
KiCad 原理图组件 | 142；位号集合完全一致（FRAME/TP 名称规范化后）
源 EPRO PCB 组件 | 141
KiCad PCB 组件 | 141；位号集合完全一致
源 EPRO PCB 网络 | 76
KiCad PCB 网络 | 76；网络名称集合完全一致
BOM 受控位号 | 119 = 73 SMT + 44 DNP + 2 后焊
BOM 参数审计 | 0 项错误：Value / BOM Value / LCSC / DNP / Footprint 均已写回
非采购板级对象 | 22 个：J7 裸 SWD 焊盘 + 20 测试点 + TP21；均排除 BOM/CPL
图框对象 | FRAME1；排除 BOM/PCB
PCB 丢失网络修复 | 21 个焊盘 net 属性已按原理图 netlist 恢复
项目级符号库 | easyedapro.kicad_sym；41 个符号定义，已与原理图内嵌库对齐
项目级封装库 | easyedapro.pretty；20 种封装，从 PCB 内嵌封装恢复
SMT CPL | 73 行，与最终主 BOM 的 73 个 SMT 位号一致
ERC | 最终 436 条；已消除库不匹配/封装链接/标注错误，剩余主要为 EasyEDA 电气引脚类型与线端点语义
DRC | 最终 163 条，0 unconnected；短路项已清零。剩余为原设计几何/制造规则项
3D 模型 | 源 .epro 不含 STEP/WRL/OBJ 模型 payload；KiCad 中保留原模型路径引用，但无法补齐 3D 文件
结论 | 电气拓扑、PCB 元件/网络、BOM/装配状态、项目符号/封装库已完整转换并校正；3D 模型不完整是源文件缺失，不是转换丢失。

Sheet: Component Audit
Ref | 状态 | 转换前 Value | 校正后 Value | 最终 BOM Value | LCSC Part # | 转换后 Footprint | DNP | 是否改值
C1 | SMT | 2.2uF | 10uF | 10µF ±10% 25V X5R | C15850 | easyedapro:C0805 |  | YES
C2 | SMT | 2.2uF | 10uF | 10µF ±10% 25V X5R | C15850 | easyedapro:C0805 |  | YES
C3 | SMT | 10uF | 100nF | 100nF ±10% 50V X7R | C49678 | easyedapro:C0805 |  | YES
C4 | SMT | 10uF | 47nF | 47nF ±5% 50V X7R | C1845663 | easyedapro:C0805 |  | YES
C5 | SMT | 470uF | 470uF | 470µF ±20% 35V, 105°C | C2992611 | easyedapro:CAP-SMD_BD10.0-L10.3-W10.3-LS11.3-FD |  | NO
C6 | SMT | 470uF | 470uF | 470µF ±20% 35V, 105°C | C2992611 | easyedapro:CAP-SMD_BD10.0-L10.3-W10.3-LS11.3-FD |  | NO
C7 | SMT | 100nF | 100nF | 100nF ±10% 50V X7R | C49678 | easyedapro:C0805 |  | NO
C8 | SMT | 100nF | 100nF | 100nF ±10% 50V X7R | C49678 | easyedapro:C0805 |  | NO
C9 | SMT | 100nF | 100nF | 100nF ±10% 50V X7R | C49678 | easyedapro:C0805 |  | NO
C10 | SMT | 100nF | 100nF | 100nF ±10% 50V X7R | C49678 | easyedapro:C0805 |  | NO
C11 | SMT | 1uF | 1uF | 1µF ±10% 50V X7R | C344178 | easyedapro:C0805 |  | NO
C12 | SMT | 1uF | 1uF | 1µF ±10% 50V X7R | C344178 | easyedapro:C0805 |  | NO
C13 | DNP | 68pF | 1p/2.2p/4.7p EXP | DNP；实验备料1pF/2.2pF/4.7pF C0G 0805 |  | easyedapro:C0805 | DNP | YES
C14 | DNP | 100nF | 1p/2.2p/4.7p EXP | DNP；实验备料1pF/2.2pF/4.7pF C0G 0805 |  | easyedapro:C0805 | DNP | YES
C15 | SMT | 100nF | 100nF | 100nF ±10% 50V X7R | C49678 | easyedapro:C0805 |  | NO
C16 | SMT | 100nF | 100nF | 100nF ±10% 50V X7R | C49678 | easyedapro:C0805 |  | NO
C17 | SMT | 10uF | 10nF | 10nF ±5% 50V C0G | C342877 | easyedapro:C0805 |  | YES
C18 | SMT | 10uF | 100nF | 100nF ±10% 50V X7R | C49678 | easyedapro:C0805 |  | YES
C19 | SMT | 10uF | 100nF | 100nF ±10% 50V X7R | C49678 | easyedapro:C0805 |  | YES
C20 | SMT | 220nF | 100nF | 100nF ±10% 50V X7R | C49678 | easyedapro:C0805 |  | YES
C21 | SMT | 220nF | 100nF | 100nF ±10% 50V X7R | C49678 | easyedapro:C0805 |  | YES
C22 | SMT | 220nF | 100nF | 100nF ±10% 50V X7R | C49678 | easyedapro:C0805 |  | YES
C23 | SMT | 220nF | 220nF | 220nF ±10% 50V X7R | C45359963 | easyedapro:C0805 |  | NO
C24 | SMT | 220nF | 4.7uF | 4.7µF ±10% 16V X5R | C380342 | easyedapro:C0805 |  | YES
C25 | SMT | 220nF | 1uF | 1µF ±10% 50V X7R | C344178 | easyedapro:C0805 |  | YES
C26 | SMT | 220nF | 100nF | 100nF ±10% 50V X7R | C49678 | easyedapro:C0805 |  | YES
C27 | SMT | 10pF | 10pF | 10pF ±5% 50V C0G | C157608 | easyedapro:C0805 |  | NO
C28 | SMT | 100nF TRIM_LPF DNP | 1uF | 1µF ±10% 50V X7R | C344178 | easyedapro:C0805 |  | YES
C29 | DNP | 1uF IPORT_LPF DNP | 1uF | 1uF |  | easyedapro:C0805 | DNP | YES
C30 | DNP | 1uF SERVO_INT DNP | 1uF | 1uF |  | easyedapro:C0805 | DNP | YES
C31 | DNP | 4.7p COMP_A DNP | 4.7p | 4.7p |  | easyedapro:C0805 | DNP | YES
C32 | DNP | 10p COMP_A DNP | 10p | 10p |  | easyedapro:C0805 | DNP | YES
C33 | DNP | 22p COMP_A DNP | 22p | 22p |  | easyedapro:C0805 | DNP | YES
C34 | DNP | 47p COMP_A DNP | 47p | 47p |  | easyedapro:C0805 | DNP | YES
C35 | DNP | 100p COMP_A DNP | 100p | 100p |  | easyedapro:C0805 | DNP | YES
C36 | DNP | 10p-100p LEAD_A_C DNP | 10p-100p | 10p-100p |  | easyedapro:C0805 | DNP | YES
C37 | DNP | 4.7p COMP_B DNP | 4.7p | 4.7p |  | easyedapro:C0805 | DNP | YES
C38 | DNP | 10p COMP_B DNP | 10p | 10p |  | easyedapro:C0805 | DNP | YES
C39 | DNP | 22p COMP_B DNP | 22p | 22p |  | easyedapro:C0805 | DNP | YES
C40 | DNP | 47p COMP_B DNP | 47p | 47p |  | easyedapro:C0805 | DNP | YES
C41 | DNP | 100p COMP_B DNP | 100p | 100p |  | easyedapro:C0805 | DNP | YES
C42 | DNP | 10p-100p LEAD_B_C DNP | 10p-100p | 10p-100p |  | easyedapro:C0805 | DNP | YES
D1 | SMT | SS56 | SS56B | SS56B, 60V 5A Schottky | C14651 | easyedapro:SMB_L4.3-W3.6-LS5.4-RD |  | YES
D2 | SMT | SS56 | SS56B | SS56B, 60V 5A Schottky | C14651 | easyedapro:SMB_L4.3-W3.6-LS5.4-RD |  | YES
D3 | DNP | SS56 | SS56 +clamp SPK DNP | SS56 +clamp SPK DNP |  | easyedapro:SMB_L4.3-W3.6-LS5.4-RD | DNP | YES
D4 | DNP | SS56 | SS56 -clamp SPK DNP | SS56 -clamp SPK DNP |  | easyedapro:SMB_L4.3-W3.6-LS5.4-RD | DNP | YES
FB1 | SMT | MLB2012F-151T | 150R@100MHz | 150Ω@100MHz, 600mA, DCR 0.25Ω | C139474 | easyedapro:L0805 |  | YES
FB2 | SMT | MLB2012F-151T | 150R@100MHz | 150Ω@100MHz, 600mA, DCR 0.25Ω | C139474 | easyedapro:L0805 |  | YES
FB3 | SMT | MLB2012F-151T | 150R@100MHz | 150Ω@100MHz, 600mA, DCR 0.25Ω | C139474 | easyedapro:L0805 |  | YES
J1 | SMT | 2060-453/998-404 | WAGO 2060 3P | WAGO 2060 3P, 4mm pitch | C2765056 | easyedapro:CONN-SMD_2060-453 |  | YES
J2 | SMT | 2060-453/998-404 | WAGO 2060 3P | WAGO 2060 3P, 4mm pitch | C2765056 | easyedapro:CONN-SMD_2060-453 |  | YES
J3 | SMT | 2060-452/998-404 | WAGO 2060 2P | WAGO 2060 2P, 4mm pitch | C2765055 | easyedapro:CONN-SMD_2060-452 |  | YES
J4 | SMT | 2060-452/998-404 | WAGO 2060 2P | WAGO 2060 2P, 4mm pitch | C2765055 | easyedapro:CONN-SMD_2060-452 |  | YES
J5 | SMT | 2060-453/998-404 | WAGO 2060 3P | WAGO 2060 3P, 4mm pitch | C2765056 | easyedapro:CONN-SMD_2060-453 |  | YES
J6 | SMT | 2060-453/998-404 | WAGO 2060 3P | WAGO 2060 3P, 4mm pitch | C2765056 | easyedapro:CONN-SMD_2060-453 |  | YES
J8 | SMT | 2060-453/998-404 | WAGO 2060 3P | WAGO 2060 3P, 4mm pitch | C2765056 | easyedapro:CONN-SMD_2060-453 |  | YES
J9 | SMT | FAULT bare SMT pads | WAGO 2060 2P | WAGO 2060 2P, 4mm pitch | C2765055 | easyedapro:CONN-SMD_2060-452 |  | YES
J10 | DNP | EXP_SPI_TIM_DNP | EXP_SPI_TIM_DNP | EXP_SPI_TIM_DNP |  | easyedapro:AAI_C11_35_LOCAL_Footprints_AAI_PinHeader_1x05_P2_54mm_Vertical | DNP | NO
J11 | DNP | EXP_I2C_DAC_DNP | EXP_I2C_DAC_DNP | EXP_I2C_DAC_DNP |  | easyedapro:AAI_C11_35_LOCAL_Footprints_AAI_PinHeader_1x05_P2_54mm_Vertical | DNP | NO
J12 | POST | 2.54-1*5P母 | 1×5P 2.54mm母排 | 1×5P 2.54mm母排 | C50950 | easyedapro:HDR-TH_5P-P2.54-V-F |  | YES
J13 | POST | 2.54-1*5P母 | 1×5P 2.54mm母排 | 1×5P 2.54mm母排 | C50950 | easyedapro:HDR-TH_5P-P2.54-V-F |  | YES
J14 | SMT | 2060-451/998-404 | WAGO 2060 1P | WAGO 2060 1P, 4mm pitch | C2765054 | easyedapro:CONN-SMD_L12.7-W3.9_2060-451-998-404 |  | YES
R1 | DNP | 100Ω | 0R | 0R |  | easyedapro:R0805 | DNP | YES
R2 | DNP | 100Ω | 0R | 0R |  | easyedapro:R0805 | DNP | YES
R3 | SMT | 100Ω | 0R | 0Ω 125mW | C17477 | easyedapro:R0805 |  | YES
R4 | SMT | 100Ω | 0R | 0Ω 125mW | C17477 | easyedapro:R0805 |  | YES
R5 | SMT | 100Ω | 100R | 100Ω ±1% 125mW | C2988937 | easyedapro:R0805 |  | YES
R6 | SMT | 0Ω | 0R | 0Ω 125mW | C17477 | easyedapro:R0805 |  | YES
R7 | SMT | 100Ω | 57.6kR | 57.6kΩ ±1% 125mW | C5153977 | easyedapro:R0805 |  | YES
R8 | DNP | 100Ω | 33.2kR 1% | 33.2kΩ 1% |  | easyedapro:R0805 | DNP | YES
R9 | DNP | 100Ω | 22.1kR 1% | 22.1kΩ 1% |  | easyedapro:R0805 | DNP | YES
R10 | SMT | 100Ω | 100kR | 100kΩ ±1% 125mW | C2907217 | easyedapro:R0805 |  | YES
R11 | SMT | 100Ω | 1kR | 1kΩ ±1% 125mW | C95781 | easyedapro:R0805 |  | YES
R12 | SMT | 2mΩ | 4.7R | 4.7Ω ±1% 2W | C2897629 | easyedapro:R0805 |  | YES
R13 | SMT | 1kΩ | 1.000kR | 1.000kΩ ±0.1% 薄膜 | C110774 | easyedapro:R0805 |  | YES
R14 | SMT | 49.9kΩ | 49.9kR | 49.9kΩ ±0.05% 15ppm/°C | C1730568 | easyedapro:R0805 |  | YES
R15 | SMT | 1kΩ | 1.000kR | 1.000kΩ ±0.1% 薄膜 | C110774 | easyedapro:R0805 |  | YES
R16 | SMT | 1kΩ | 39.0kR | 39.0kΩ ±0.1% 10ppm/°C 200mW | C1720356 | easyedapro:R0805 |  | YES
R17 | SMT | 1.6Ω | 0R | 0Ω 125mW | C17477 | easyedapro:R0805 |  | YES
R18 | SMT | 1.6Ω | 100R | 100Ω ±1% 125mW | C2988937 | easyedapro:R0805 |  | YES
R19 | SMT | 1.6Ω | 30.9kR | 30.9kΩ ±0.1% ≤25ppm/°C 薄膜 | C865394 | easyedapro:R0805 |  | YES
R20 | SMT | 1.6Ω | 10.0kR | 10.0kΩ ±0.1% 薄膜 | C110775 | easyedapro:R0805 |  | YES
R21 | SMT | 1.6Ω | 10.0kR | 10.0kΩ ±0.1% 薄膜 | C110775 | easyedapro:R0805 |  | YES
R22 | SMT | 1.6Ω | 10.0kR | 10.0kΩ ±0.1% 薄膜 | C110775 | easyedapro:R0805 |  | YES
R23 | SMT | 100K | 100kR | 100kΩ ±1% 125mW | C2907217 | easyedapro:R0805 |  | YES
R24 | SMT | 2.4Ω | 10kR | 10kΩ ±1% 125mW | C2907219 | easyedapro:R0805 |  | YES
R25 | DNP | 1.6Ω | 6.49kR 0.1% | 6.49kΩ 0.1% |  | easyedapro:R0805 | DNP | YES
R26 | DNP | 1.6Ω | 10k | 10k |  | easyedapro:R0805 | DNP | YES
R27 | DNP | 1.6Ω | 100k | 100k |  | easyedapro:R0805 | DNP | YES
R28 | DNP | 1.6Ω | 100kR ±1% | 100kΩ ±1% |  | easyedapro:R0805 | DNP | YES
R29 | DNP | 1.6Ω | 10kR ±1% | 10kΩ ±1% |  | easyedapro:R0805 | DNP | YES
R30 | DNP | 1.6Ω | 100k | 100k |  | easyedapro:R0805 | DNP | YES
R31 | DNP | 1.6Ω | 10k | 10k |  | easyedapro:R0805 | DNP | YES
R32 | DNP | 360kΩ | 360kR ±1% | 360kΩ ±1% |  | easyedapro:R0805 | DNP | YES
R33 | DNP | 360kΩ | 360kR ±1% | 360kΩ ±1% |  | easyedapro:R0805 | DNP | YES
R34 | SMT | 1M ISIG_TRIM_INJ DNP | 1.000MR | 1.000MΩ ±0.1% 25ppm/°C | C2075448 | easyedapro:R0805 |  | YES
R35 | SMT | 10k TRIM_SRC DNP | 10.0kR | 10.0kΩ ±0.1% ≤25ppm/°C 薄膜 | C110775 | easyedapro:R0805 |  | YES
R36 | SMT | 0R Z_GND DEFAULT | 0R | 0Ω 125mW | C17477 | easyedapro:R0805 |  | YES
R37 | DNP | 1M ZTRIM_INJ DNP | 1MR | 1MΩ |  | easyedapro:R0805 | DNP | YES
R38 | DNP | 1M ZSERVO_INJ DNP | 1MR | 1MΩ |  | easyedapro:R0805 | DNP | YES
R39 | DNP | 10k IPORT_TAP DNP | 10kR | 10kΩ |  | easyedapro:R0805 | DNP | YES
R40 | DNP | 1M SERVO_IN DNP | 1MR | 1MΩ |  | easyedapro:R0805 | DNP | YES
R41 | DNP | 10M SERVO_FB DNP | 10MR | 10MΩ |  | easyedapro:R0805 | DNP | YES
R42 | DNP | 0R SERVO_RESET_DNP | 0R | 0Ω |  | easyedapro:R0805 | DNP | YES
R43 | DNP | 0R SERVO_DISABLE_DNP | 0R | 0Ω |  | easyedapro:R0805 | DNP | YES
R44 | DNP | 1k-10k LEAD_A_R DNP | 1k-10k | 1k–10k |  | easyedapro:R0805 | DNP | YES
R45 | DNP | 1k-10k LEAD_B_R DNP | 1k-10k | 1k–10k |  | easyedapro:R0805 | DNP | YES
R46 | SMT | 0R RISO default 0.05-0.2R option | 0R | 0Ω 125mW | C17477 | easyedapro:R0805 |  | YES
RSH2 | SMT | 0.1R 3W 2512 current sense + Kelvin pads | 0.100R | 0.100Ω ±1% 3W ±50ppm/°C | C393067 | easyedapro:AAI_C11_35_LOCAL_Footprints_AAI_SHUNT_4T_3920_Kelvin |  | YES
U1 | SMT | OPA548F/500 | OPA548F/500 | OPA548F/500 | C527496 | easyedapro:TO-263-7_L10.2-W10.4-P1.27-LS14.4-TL |  | NO
U2 | SMT | AD633ARZ-R7 | AD633ARZ-R7 | AD633ARZ-R7 | C77810 | easyedapro:SOIC-8_L4.9-W3.9-P1.27-LS6.0-BL |  | NO
U3 | SMT | INA149AIDR | INA149AIDR | INA149AIDR | C183089 | easyedapro:SOIC-8_L4.9-W3.9-P1.27-LS6.0-BL |  | NO
U4 | SMT | OPA1656IDR | OPA1656IDR | OPA1656IDR | C1849431 | easyedapro:SOIC-8_L4.9-W3.9-P1.27-LS6.0-BL |  | NO
U5 | SMT | STM32G431CBT6 | STM32G431CBT6 | STM32G431CBT6（冻结型号） | C529355 | easyedapro:LQFP-48_L7.0-W7.0-P0.50-LS9.0-BL |  | NO
U6 | SMT | AMS1117-3.3 | AMS1117-3.3 | AMS1117-3.3 | C6186 | easyedapro:SOT-223-3_L6.5-W3.4-P2.30-LS7.0-BR |  | NO
U7 | SMT | TLP185(GR-TPR,E | TLP185(GR-TPR,E | TLP185(GR-TPR,E | C393884 | easyedapro:SOP-6_4P-L3.7-W4.6-P2.54-LS7.0-BL |  | NO
U8 | SMT | OPA1656IDR | OPA1656IDR | OPA1656IDR | C1849431 | easyedapro:SOIC-8_L4.9-W3.9-P1.27-LS6.0-BL |  | NO
U9 | DNP | OPA1656IDR SERVO DNP | OPA1656IDR | OPA1656IDR |  | easyedapro:SOIC-8_L4.9-W3.9-P1.27-LS6.0-BL | DNP | YES
U10 | DNP | TMUX7219DGKRQ1 | TMUX7219DGKRQ1 | TMUX7219DGKRQ1 |  | easyedapro:VSSOP-8_L3.0-W3.0-P0.65-LS4.9-BL | DNP | NO

Sheet: Residual Checks
类型 | 检查项 | 数量 | 说明
ERC | pin_to_pin | 288 | 主要由 EasyEDA 导入符号的 electrical pin type 语义引起；不代表网络丢失。
ERC | unconnected_wire_endpoint | 105 | 源原理图画线/端点风格转换后的 ERC 语义；需逐项决定是否要整理图面。
ERC | endpoint_off_grid | 27 | 端点落在 KiCad 网格之外；属于图面规范问题。
ERC | pin_not_driven | 16 | 被动器件/连接器被导入为 Input 等电气类型造成的驱动规则问题。
DRC | annular_width | 72 | 源 PCB 的部分过孔环宽低于 KiCad/源规则下限；属于原板几何问题，不建议在转换阶段自动改铜。
DRC | silk_over_copper | 40 | 丝印与裸铜/焊盘重叠；制造可清理，但不影响网络转换。
DRC | hole_clearance | 23 | 孔到铜间距不足；属于原 PCB 几何/制造规则问题。
DRC | courtyards_overlap | 15 | 器件 courtyard 重叠；多为导入封装 courtyard 定义/布局问题。
DRC | copper_edge_clearance | 7 | 铜到板边间距；需按实际板厂能力复核。
DRC | silk_overlap | 3 | 丝印之间重叠。
DRC | clearance | 1 | 按源 EasyEDA 4 mil clearance 校正后仅剩少量真正间距问题。
DRC | via_dangling | 1 | 单个悬空过孔，建议人工复核。
DRC | track_dangling | 1 | 单个悬空走线端，建议人工复核。

Sheet: Production Crosscheck
LCSC Part # | BOM_5720434A_Y17 | BOM_PASTER | 结论
C110774 | FOUND | FOUND | 最终 BOM 型号可在生产资料中找到
C110775 | FOUND | FOUND | 最终 BOM 型号可在生产资料中找到
C139474 | FOUND | FOUND | 最终 BOM 型号可在生产资料中找到
C14651 | FOUND | FOUND | 最终 BOM 型号可在生产资料中找到
C157608 | FOUND | FOUND | 最终 BOM 型号可在生产资料中找到
C15850 | FOUND | FOUND | 最终 BOM 型号可在生产资料中找到
C1720356 | FOUND | NOT FOUND | 最终 BOM 型号可在生产资料中找到
C1730568 | FOUND | NOT FOUND | 最终 BOM 型号可在生产资料中找到
C17477 | FOUND | FOUND | 最终 BOM 型号可在生产资料中找到
C183089 | FOUND | FOUND | 最终 BOM 型号可在生产资料中找到
C1845663 | FOUND | FOUND | 最终 BOM 型号可在生产资料中找到
C1849431 | FOUND | FOUND | 最终 BOM 型号可在生产资料中找到
C2075448 | FOUND | FOUND | 最终 BOM 型号可在生产资料中找到
C2765054 | FOUND | FOUND | 最终 BOM 型号可在生产资料中找到
C2765055 | FOUND | FOUND | 最终 BOM 型号可在生产资料中找到
C2765056 | FOUND | FOUND | 最终 BOM 型号可在生产资料中找到
C2897629 | FOUND | FOUND | 最终 BOM 型号可在生产资料中找到
C2907217 | FOUND | FOUND | 最终 BOM 型号可在生产资料中找到
C2907219 | FOUND | FOUND | 最终 BOM 型号可在生产资料中找到
C2988937 | FOUND | FOUND | 最终 BOM 型号可在生产资料中找到
C2992611 | FOUND | FOUND | 最终 BOM 型号可在生产资料中找到
C342877 | FOUND | FOUND | 最终 BOM 型号可在生产资料中找到
C344178 | FOUND | FOUND | 最终 BOM 型号可在生产资料中找到
C380342 | FOUND | FOUND | 最终 BOM 型号可在生产资料中找到
C393067 | FOUND | FOUND | 最终 BOM 型号可在生产资料中找到
C393884 | FOUND | FOUND | 最终 BOM 型号可在生产资料中找到
C45359963 | FOUND | FOUND | 最终 BOM 型号可在生产资料中找到
C49678 | FOUND | FOUND | 最终 BOM 型号可在生产资料中找到
C5153977 | FOUND | FOUND | 最终 BOM 型号可在生产资料中找到
C527496 | FOUND | FOUND | 最终 BOM 型号可在生产资料中找到
C529355 | FOUND | FOUND | 最终 BOM 型号可在生产资料中找到
C6186 | FOUND | FOUND | 最终 BOM 型号可在生产资料中找到
C77810 | FOUND | FOUND | 最终 BOM 型号可在生产资料中找到
C865394 | FOUND | FOUND | 最终 BOM 型号可在生产资料中找到
C95781 | FOUND | FOUND | 最终 BOM 型号可在生产资料中找到
