341151719/sine-resistor-pcb-analysis/SPICE部分/validation_workspace_20260904_19wI9s/project/SPICE_project_repaired_20260710_FINAL/verification_results/fixed_signoff_compact.csv

case | simulation_status | acceptance_status | rtarget_tail_mean_ohm | ztotal_real_ohm | ztotal_imag_ohm | ztotal_mag_ohm | ztotal_phase_deg | iport_dc_fit_a | fixed_real_error_ohm | fixed_real_tolerance_ohm | fixed_imag_tolerance_ohm | acceptance_reasons
full_einj_fixed_r1_f1000 | completed | fail | 0.999262225 | 1.053686865986414 | 0.3418316279497157 | 1.107747657826016 | 17.973830805603896 | 0.0041069720905113 | 0.054424640986414 | 0.1 | 0.1 | fixed_imag=0.341832ohm>0.1ohm
signoff_fixed_r5_carrier1k | completed | pass | 4.998821329999998 | 5.045566416964352 | 0.1220073454652043 | 5.047041337293162 | 1.3852050207532822 | -0.0066196788753052 | 0.0467450869643535 | 0.2499410664999999 | 0.2499410664999999
full_einj_fixed_r7p2_f1000 | completed | pass | 7.1985788300000015 | 7.248698619736763 | -0.0078742601173634 | 7.248702896639236 | -0.0622403713710337 | -0.007923004424911 | 0.0501197897367617 | 0.3599289415000001 | 0.3599289415000001
signoff_fixed_r20_carrier1k | completed | pass | 19.997168 | 20.00076724632736 | -0.7666569735245501 | 20.015455362214848 | -2.195151506402176 | -0.0092257395486224 | 0.0035992463273615 | 0.9998584 | 0.9998584
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
