341151719/sine-resistor-pcb-analysis/SPICE部分/validation_workspace_20260904_19wI9s/project/SPICE_project_repaired_20260710_FINAL/reports/HISTORICAL_RESULTS_NOTICE.md

# Historical report notice

Reports in this directory predate the 2026-07-10 acceptance repair. They remain historical engineering evidence, but `status=ok` may mean only that ngspice completed.

New authoritative runs must use the repaired runner and distinguish `simulation_status` from `acceptance_status`. Fixed impedance is now a DC-aware complex phasor; dynamic impedance is evaluated with local carrier phasors. Old point-wise V/I data is diagnostic only.
