341151719/sine-resistor-pcb-analysis/SPICE部分/validation_workspace_20260904_19wI9s/project/SPICE_project_repaired_20260710_FINAL/verification_results/signoff_dynamic_fm100_carrier10k_dynamic_phasor.csv

time_s | rtarget_ohm | ztotal_real_ohm | ztotal_imag_ohm | real_error_ohm | real_rel_error | imag_rel | carrier_current_peak_a | iport_dc_fit_a | vspk_dc_fit_v
0.03005 | 51.786498936100024 | 41.128351745011756 | -22.65742439986121 | -10.658147191088268 | -0.20580937908622637 | -0.4375160488802009 | 0.00034338064640596343 | -0.007190174720584607 | 0.05575208548426508
0.030100000000000002 | 53.33997232856004 | 42.200593413929234 | -23.435481588154538 | -11.139378914630804 | -0.20883735833260642 | -0.43936058766206715 | 0.0003335918255721748 | -0.007166663004906687 | 0.05571848837775942
0.030150000000000003 | 54.890636825940135 | 43.45787952496925 | -24.2324421616519 | -11.432757300970884 | -0.20828246786832702 | -0.44146768124577795 | 0.0003230380650010231 | -0.00714421751874771 | 0.05567484882073413
0.030200000000000005 | 56.43696227934013 | 44.52685479622202 | -25.003912614657168 | -11.91010748311811 | -0.21103381546596886 | -0.44304143250832523 | 0.0003143330751957479 | -0.007123677777739714 | 0.055642906888806694
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
