341151719/sine-resistor-pcb-analysis/故障假设排查_20260908/H12_OPA548_ES_R5动态耦合/fast_sweep_summary.csv

case | returncode | R10VAL | LSRC | IESVAL | ENHIGH | tp8_pp | tp8_rms | f_dom_hz | es_min | es_max | state_min | state_max | state_crossings | TON | TOFF | EN_DELAY | EN_WIDTH | GND_L
r10_100k_lsrc_0.2u | 0 | 100k | 0.2u | 70u | 0 | 2.40446897e-09 | 1.769215128251941e-10 | 425000.0 | 3.5003599199999993 | 3.5003658800000004 | 0.960551085 | 0.999996994 | 0
r10_100k_lsrc_1u | 0 | 100k | 1u | 70u | 0 | 1.2530779110000001e-09 | 9.26330698735325e-11 | 425000.0 | 3.5003599199999993 | 3.5003741 | 0.958479749 | 0.999996994 | 0
r10_100k_lsrc_3u | 0 | 100k | 3u | 70u | 0 | 1.075378641e-09 | 7.95325007573464e-11 | 425000.0 | 3.5003599199999993 | 3.50037497 | 0.957873623 | 0.999996994 | 0
r10_100k_lsrc_10u | 0 | 100k | 10u | 70u | 0 | 1.1032001890000002e-09 | 8.070539188740237e-11 | 425000.0 | 3.5003597799999997 | 3.5003676 | 0.957613433 | 0.999996994 | 0
r10_6.8k_lsrc_0.2u | 0 | 6.8k | 0.2u | 70u | 0 | 5.1358366877999996e-11 | 1.2390511437932905e-11 | 10000.0 | 0.4827971499999997 | 0.4867988000000001 | 0.0 | 0.0 | 0
r10_6.8k_lsrc_1u | 0 | 6.8k | 1u | 70u | 0 | 4.8970277492e-11 | 1.1708229678636426e-11 | 10000.0 | 0.48279705999999933 | 0.4925592299999999 | 0.0 | 0.0 | 0
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
