341151719/sine-resistor-pcb-analysis/故障假设排查_20260908/H02_R16_漏装/fixed_H02_R16_1T.cir

* H2 single component fault: R16 is DNP/open (represented as 1 teraohm).
* The U4 pin6-to-R16 copper path remains present; only the resistor body is
* removed.  This is not the previously rejected assumption of an open trace.
.param R16VAL=1e12
.include "fault_fixed_common.inc"
.control
set noaskquit
echo "CASE H2 R16=1T open resistor, J1=+/-5, J2=+/-10, OPA548 OFF"
tran 0.05u 0.5m 0 0.05u
meas tran TP8_MAX MAX v(TP8) from=0.25m to=0.5m
meas tran TP8_MIN MIN v(TP8) from=0.25m to=0.5m
meas tran OUT_MAX MAX v(OPA_OUT) from=0.25m to=0.5m
meas tran OUT_MIN MIN v(OPA_OUT) from=0.25m to=0.5m
meas tran TP8_EARLY_MAX MAX v(TP8) from=10u to=0.25m
meas tran TP8_EARLY_MIN MIN v(TP8) from=10u to=0.25m
meas tran IP_FINAL FIND i(VJ1P) AT=0.5m
meas tran IN_FINAL FIND i(VJ1N) AT=0.5m
meas tran I2P_FINAL FIND i(VJ2P) AT=0.5m
meas tran I2N_FINAL FIND i(VJ2N) AT=0.5m
let TP8_PP=TP8_MAX-TP8_MIN
let OUT_PP=OUT_MAX-OUT_MIN
echo "RESULT H2"
print TP8_PP OUT_PP TP8_EARLY_MAX TP8_EARLY_MIN IP_FINAL IN_FINAL I2P_FINAL I2N_FINAL
wrdata results/fixed_H2_R16_1T.dat time v(TP8) v(U4O) v(OPA_OUT) v(ES) v(VPLUS) v(VMINUS) i(VJ1P) i(VJ1N) i(VJ2P) i(VJ2N)
quit
.endc
.end
