341151719/sine-resistor-pcb-analysis/故障假设排查_20260908/H05_U4B输入输出焊桥/fixed_H05_pin6_pin7_bridge.cir

* H05 physical replacement: nearest U4B input/output solder bridge.
* U4N is U4 pin 6 (U4B_N, inverting input); U4O is pin 7 (VCMD, output).
* The 1 mΩ element is the only changed connection and bypasses R16.
.param R16VAL=39k
.include "fault_fixed_common.inc"
RBRIDGE_U4N_U4O U4N U4O 1m
.control
set noaskquit
echo "CASE H05 nearest adjacent pin6-pin7 bridge, R16=39k, J1=+/-5, J2=+/-10, OPA548 OFF"
tran 0.05u 0.5m 0 0.05u
meas tran TP8_MAX MAX v(TP8) from=0.25m to=0.5m
meas tran TP8_MIN MIN v(TP8) from=0.25m to=0.5m
meas tran OUT_MAX MAX v(OPA_OUT) from=0.25m to=0.5m
meas tran OUT_MIN MIN v(OPA_OUT) from=0.25m to=0.5m
meas tran TP8_EARLY_MAX MAX v(TP8) from=10u to=0.25m
meas tran TP8_EARLY_MIN MIN v(TP8) from=10u to=0.25m
meas tran U4O_MAX MAX v(U4O) from=0.25m to=0.5m
meas tran U4O_MIN MIN v(U4O) from=0.25m to=0.5m
meas tran IP_FINAL FIND i(VJ1P) AT=0.5m
meas tran IN_FINAL FIND i(VJ1N) AT=0.5m
meas tran I2P_FINAL FIND i(VJ2P) AT=0.5m
meas tran I2N_FINAL FIND i(VJ2N) AT=0.5m
let TP8_PP=TP8_MAX-TP8_MIN
let OUT_PP=OUT_MAX-OUT_MIN
let U4O_PP=U4O_MAX-U4O_MIN
echo "RESULT H05"
print TP8_PP OUT_PP U4O_PP TP8_EARLY_MAX TP8_EARLY_MIN IP_FINAL IN_FINAL I2P_FINAL I2N_FINAL
wrdata results/fixed_H05_pin6_pin7_bridge.dat time v(TP8) v(U4O) v(OPA_OUT) v(ES) v(VPLUS) v(VMINUS) i(VJ1P) i(VJ1N) i(VJ2P) i(VJ2N)
quit
.endc
.end
