341151719/sine-resistor-pcb-analysis/实际遇到的问题/PCB_AWARE_full_extracted_loop.cir

* PCB_AWARE_full_extracted_loop.cir
* Direct segmented-copper extraction reference model.
* NOTE: OPA548 vendor macro is retained here for AC loading only; do not use
* its shutdown transient as a calibrated OFF-state truth model.
.include "models/OPA1656.LIB"
.include "models/OPA548.LIB"
.include "models/AD633.cir"
.options method=gear reltol=2e-4 abstol=1e-11 vntol=1e-8 gmin=1e-12
R_ANA_P_1 ANA_P_N0 ANA_P_M0 0.00159213048
L_ANA_P_1 ANA_P_M0 ANA_P_N1 0.7389n
R_ANA_P_2 ANA_P_N2 ANA_P_M1 0.00448453318
L_ANA_P_2 ANA_P_M1 ANA_P_N3 5.55n
R_ANA_P_3 ANA_P_N4 ANA_P_M2 0.000453786277
L_ANA_P_3 ANA_P_M2 ANA_P_N5 0.351n
R_ANA_P_4 ANA_P_N5 ANA_P_M3 0.00178428637
L_ANA_P_4 ANA_P_M3 ANA_P_N6 1.38013102n
R_ANA_P_5 ANA_P_N7 ANA_P_M4 0.000719455565
L_ANA_P_5 ANA_P_M4 ANA_P_N8 0.333895822n
R_ANA_P_6 ANA_P_N9 ANA_P_M5 0.00314030446
L_ANA_P_6 ANA_P_M5 ANA_P_N10 1.4574n
R_ANA_P_7 ANA_P_N11 ANA_P_M6 0.00165467154
L_ANA_P_7 ANA_P_M6 ANA_P_N12 2.0478n
R_ANA_P_8 ANA_P_N3 ANA_P_M7 0.00123264061
L_ANA_P_8 ANA_P_M7 ANA_P_N13 1.5255n
R_ANA_P_9 ANA_P_N14 ANA_P_M8 0.00145444319
L_ANA_P_9 ANA_P_M8 ANA_P_N15 1.125n
R_ANA_P_10 ANA_P_N16 ANA_P_M9 0.00148805699
L_ANA_P_10 ANA_P_M9 ANA_P_N11 1.3812n
R_ANA_P_11 ANA_P_N17 ANA_P_M10 0.000840344957
L_ANA_P_11 ANA_P_M10 ANA_P_N18 0.78n
R_ANA_P_12 ANA_P_N1 ANA_P_M11 0.00119910761
L_ANA_P_12 ANA_P_M11 ANA_P_N19 0.5565n
R_ANA_P_13 ANA_P_N19 ANA_P_M12 0.0011317484
L_ANA_P_13 ANA_P_M12 ANA_P_N9 0.525238917n
R_ANA_P_14 ANA_P_N20 ANA_P_M13 0.00184850034
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
RPAD_SPK_R6_1_0 SPK_PAD_R6_1 SPK_N15 1m
RPAD_SPK_RSH2_2_0 SPK_PAD_RSH2_2 SPK_N11 1m
RPAD_SPK_RSH2_2_1 SPK_PAD_RSH2_2 SPK_N12 1m
RPAD_SPK_RSH2_2_2 SPK_PAD_RSH2_2 SPK_N19 1m
RPAD_SPK_R25_1_0 SPK_PAD_R25_1 SPK_N5 1m
RPAD_SPK_R25_1_1 SPK_PAD_R25_1 SPK_N16 1m
RPAD_SPK_R25_1_2 SPK_PAD_R25_1 SPK_N17 1m
RPAD_SPK_D4_1_0 SPK_PAD_D4_1 SPK_N18 1m
RG_SPK_0 SPK_N0 0 1e12
RG_SPK_1 SPK_N1 0 1e12
RG_SPK_2 SPK_N2 0 1e12
RG_SPK_3 SPK_N3 0 1e12
RG_SPK_4 SPK_N4 0 1e12
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
